greghulette/Wireless_Communication_Board-WCB/docs/hil_plan/WCB.md

# WCB HIL coverage re-scan: work plan WCB-WP12 to WCB-WP59

> Written 2026-09-27 by planning agents that read the code (and, for WCB, a verified coverage re-scan), for the
> away week's goal: a complete HIL tool for the WCBs, NaviCore and Intellex. It is a plan, not a spec: line numbers
> drift, and any claim is to be confirmed against the code before acting on it. Progress is tracked in
> [../HIL_TEST_AUDIT.md](../HIL_TEST_AUDIT.md) §6 and decisions in [../HIL_WEEK_DECISIONS.md](../HIL_WEEK_DECISIONS.md).

2026-09-27. Input: `scratchpad/wcb_rescan_gaps.json` (11 groups, 295 confirmed gap entries; the 5 refuted entries are
excluded). Code: HEAD `1f629a8`. Read-only: no port opened, nothing run.

**Line numbers.** The WP tables keep the scan's citations, which were taken at `c619dd6`. Commit `1f629a8` (tracker #94,
RMT PWM pulses) landed after the scan. It moved `WCB.ino` by -3 lines after :7949 and moved `WCB_PWM.cpp` by about
+80 lines after :155. §3 cites `1f629a8`, and every line there was re-checked by hand. For the full how, nearest test and
verifier notes of any row, look its id up in the JSON.

**Codes.** Mode: U = unattended; O = opt-in (bench.json key named); A = attended (per D7 these still run in the nightly
full runs when ticked). Effort: S = under half a day, M = about a day, L = several days, or reboot-heavy, or needs a
firmware fix first. **BUG-n** = the test is expected to fail until §3 item n is fixed. Write it as a `(should)` test.

---

## 1. How much of the WCB is not covered

The re-scan verified 295 gap entries against 1,941 checked behaviours (the two mechanical scans account for 644 of
those): 19 high, 98 medium and 178 low risk, of which 208 are untested and 87 partial. The two mechanical scans overlap the behaviour groups heavily. After merging
duplicates, **214 distinct behaviours** remain uncovered: **18 high, 75 medium, 121 low**. 177 are firmware
(9 H / 54 M / 114 L) and 37 are Wizard (9 H / 21 M / 7 L).

Testability of the 214:
- 176 can be tested unattended on today's bench.
- 25 need an opt-in or someone at the bench.
- 13 are blocked: 4 need a probe feature, 2 need hardware the bench lacks, and 7 need a firmware fault knob or are dead
  code.

The command surface itself is well pinned. What is missing falls into four areas:
- **Concurrency and ordering:** the loop-prevention race, restart versus config pull, and the boot load order.
- **Multi-actor mesh paths the bench never combines:** relay pushes, Wizard-origin FRAGs, permanent auto-join,
  controller-routed traffic, and daisy-chained Maestros.
- **Persistence:** non-default values across a reboot, and behaviour on a full NVS.
- **The Wizard's push side:** only a single one-label direct push is tested.

The scan also exposed **32 firmware findings, 3 high and 12 medium (§3). 26 are outright defects.** Among them:
- saved PWM mappings load before the board number;
- `?HW` accepts the other chip's pin map (a boot loop on a classic ESP32);
- a race drops typed broadcasts from the mesh;
- ETM characterisation phase 3 never loads the mesh.

---

## 2. Work packages
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
