greghulette/Wireless_Communication_Board-WCB/Code/bin/WCB_S3_custom_bootloader_README.md

# WCB ESP32-S3 custom bootloader

**File:** `WCB_S3_custom_bootloader_16MB_wdt3s.bin`

A drop-in replacement for the stock Arduino-ESP32 3.3.4 S3 bootloader, identical
to it **except** the RTC watchdog timeout is shortened from 9000 ms → **3000 ms**.
Purpose: if a cold/marginal board stalls in the pre-app boot window, it
auto-resets and retries in ~3 s instead of sitting dark until someone presses
reset. The RTC WDT runs off the internal RC oscillator, so it still fires even
when a cold crystal is what's stalling the boot.
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
