greghulette/Wireless_Communication_Board-WCB/Images/21cropped.jpg

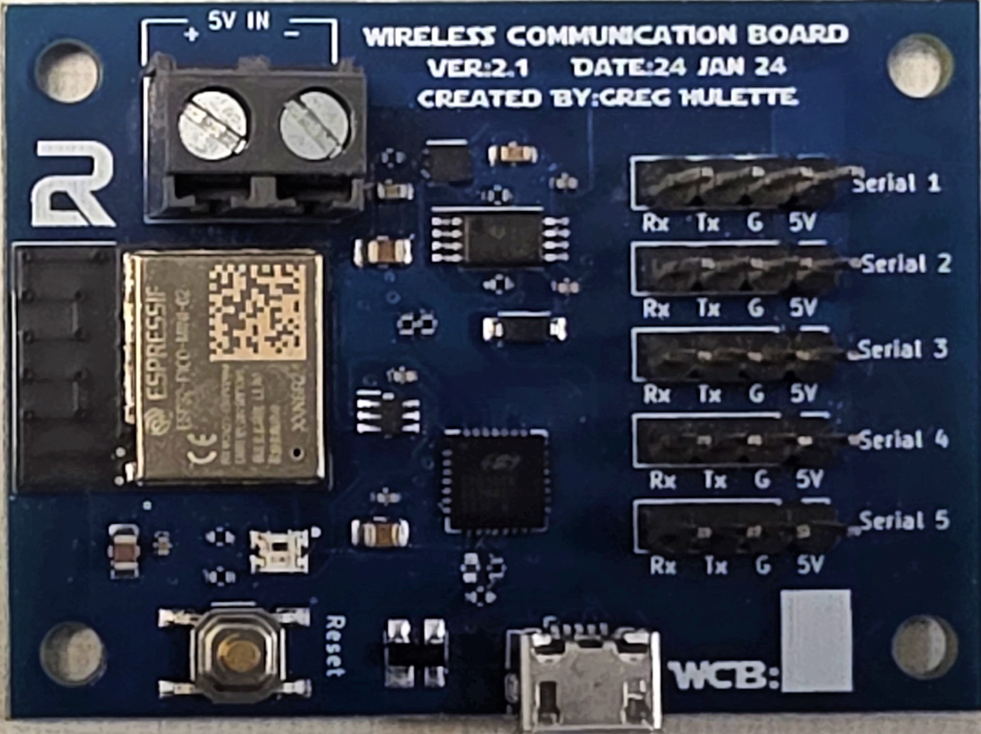
Images/21cropped.jpg
