greghulette/Wireless_Communication_Board-WCB/Images/24-1.png

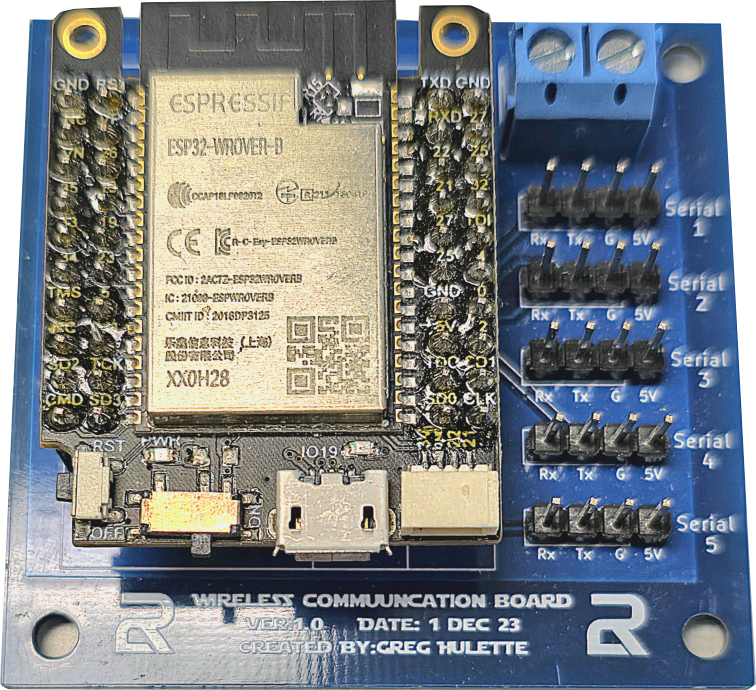
Images/24-1.png
