greghulette/Wireless_Communication_Board-WCB/Images/24.png

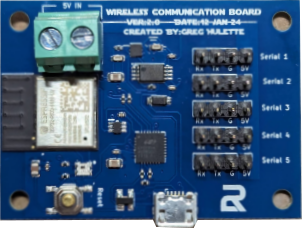
Images/24.png
