greghulette/Wireless_Communication_Board-WCB/Images/24cropped.jpg

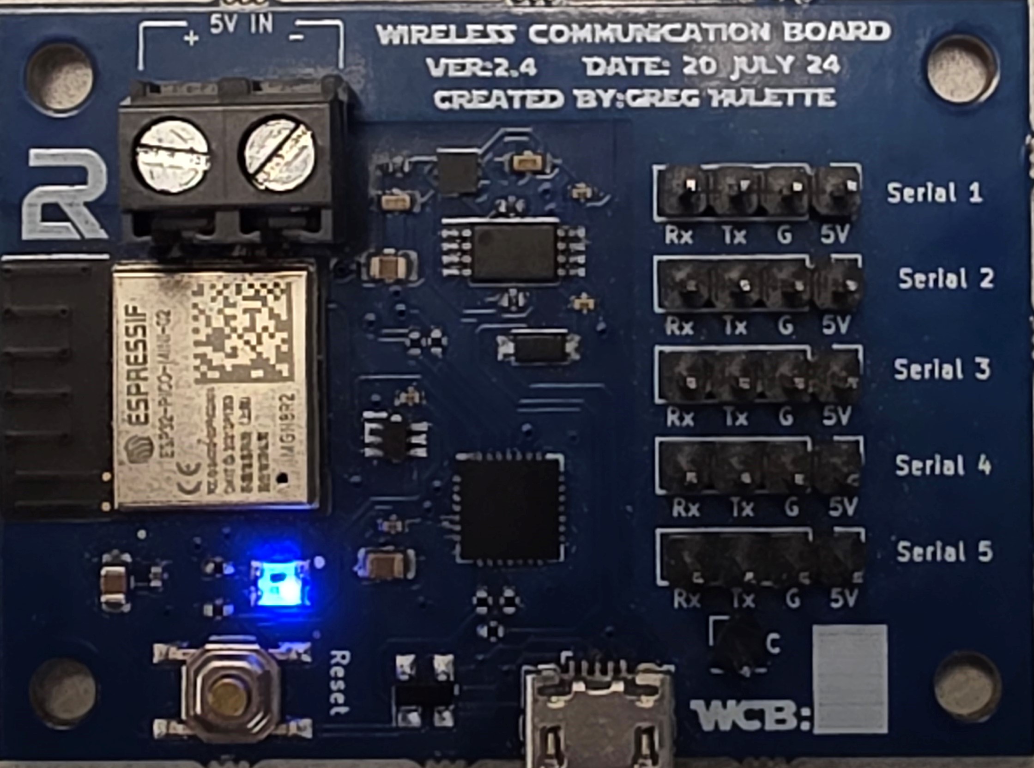
Images/24cropped.jpg
