greghulette/Wireless_Communication_Board-WCB/Images/32-1.png

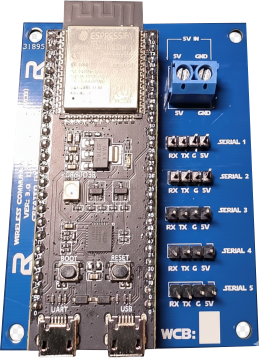
Images/32-1.png
