greghulette/Wireless_Communication_Board-WCB/Images/CAD3.1.png

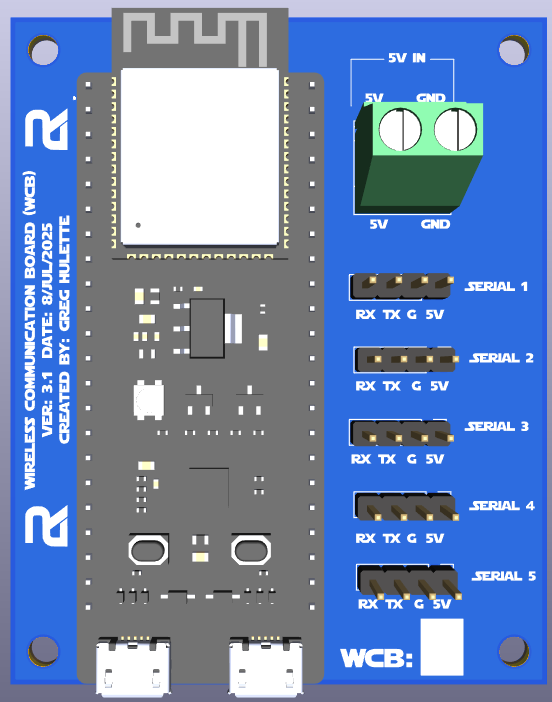
Images/CAD3.1.png
