greghulette/Wireless_Communication_Board-WCB/Images/CAD3.1_Bare.png

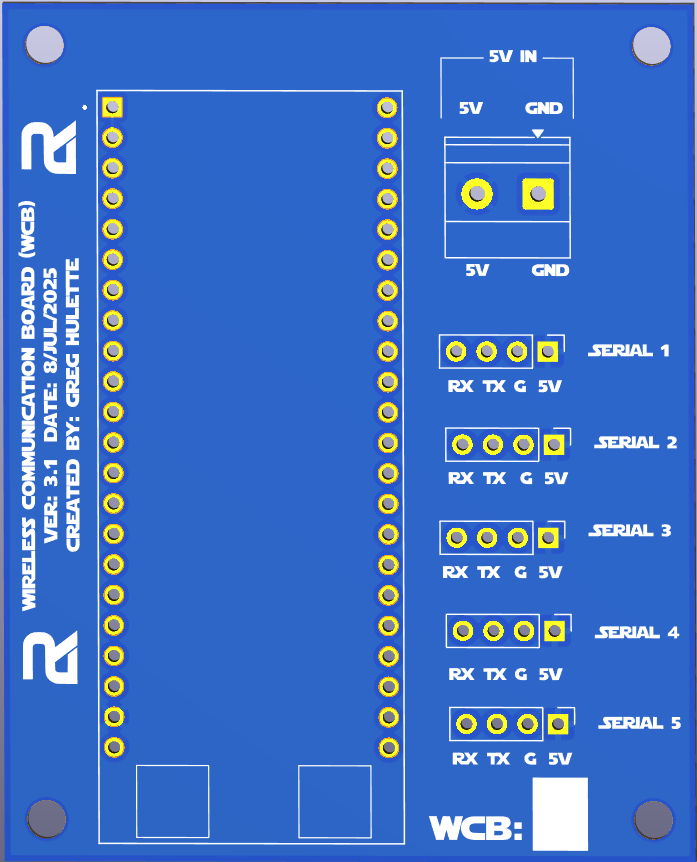
Images/CAD3.1_Bare.png
