greghulette/Wireless_Communication_Board-WCB/Images/CAD3.2.png

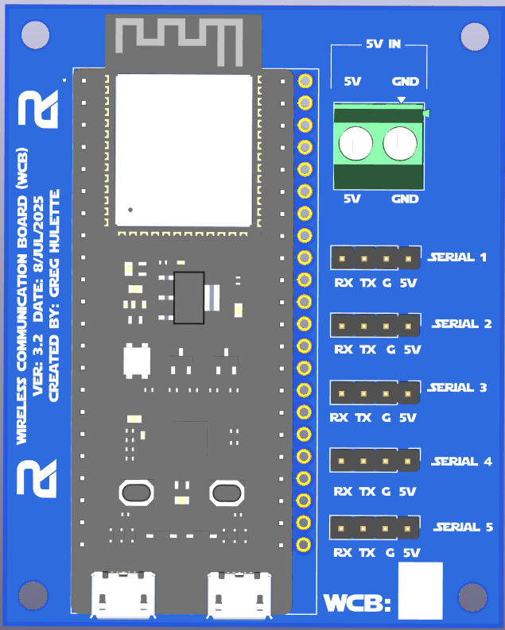
Images/CAD3.2.png
