greghulette/Wireless_Communication_Board-WCB/Images/CAD3.2_Bare.png

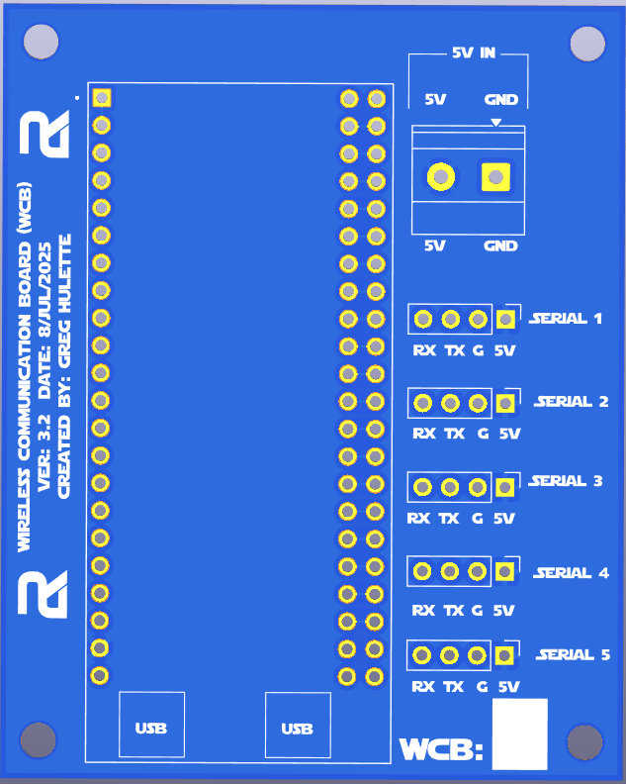
Images/CAD3.2_Bare.png
