greghulette/Wireless_Communication_Board-WCB/Images/CADImage.png

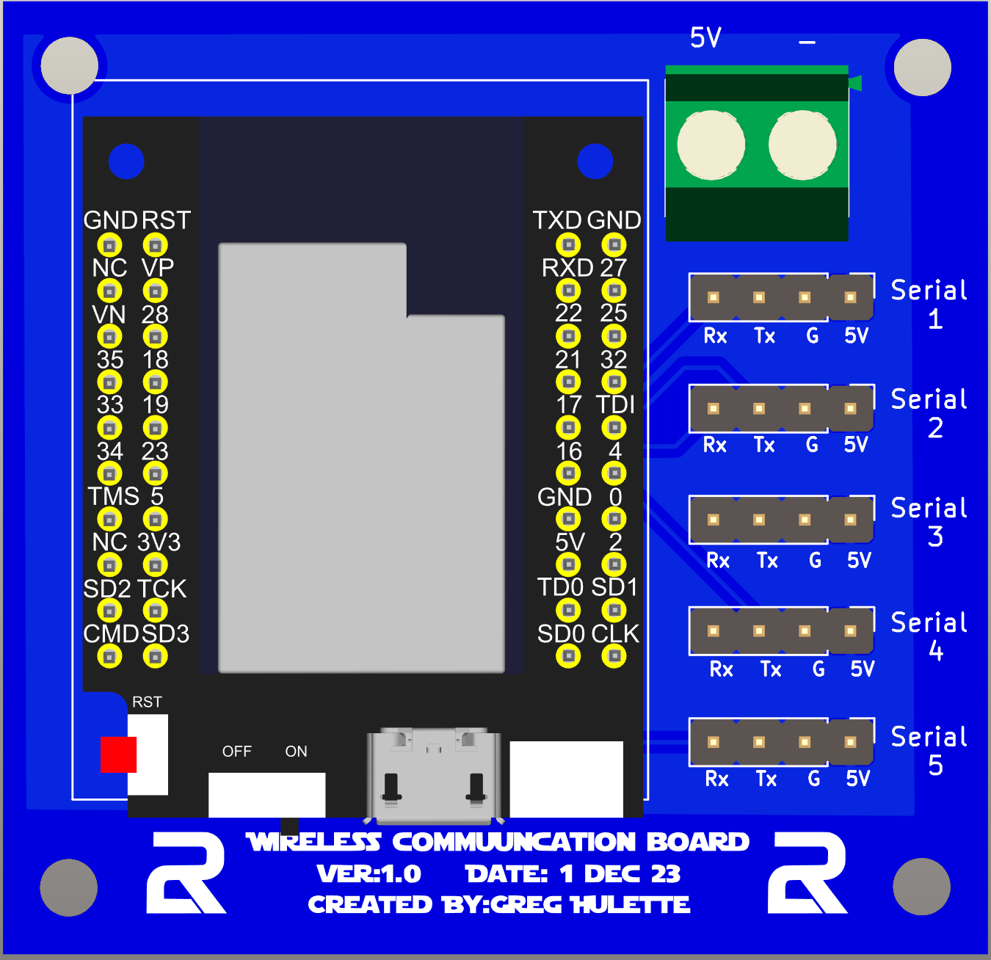
Images/CADImage.png
