greghulette/Wireless_Communication_Board-WCB/Images/Code_Preferences.png

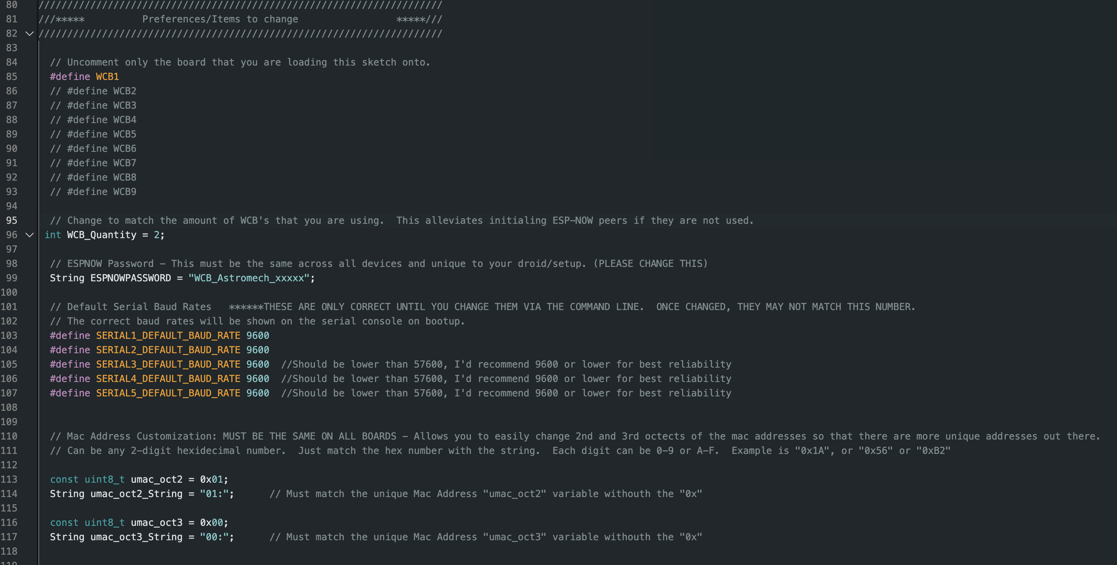
Images/Code_Preferences.png
