greghulette/Wireless_Communication_Board-WCB/Images/DataConnection.png

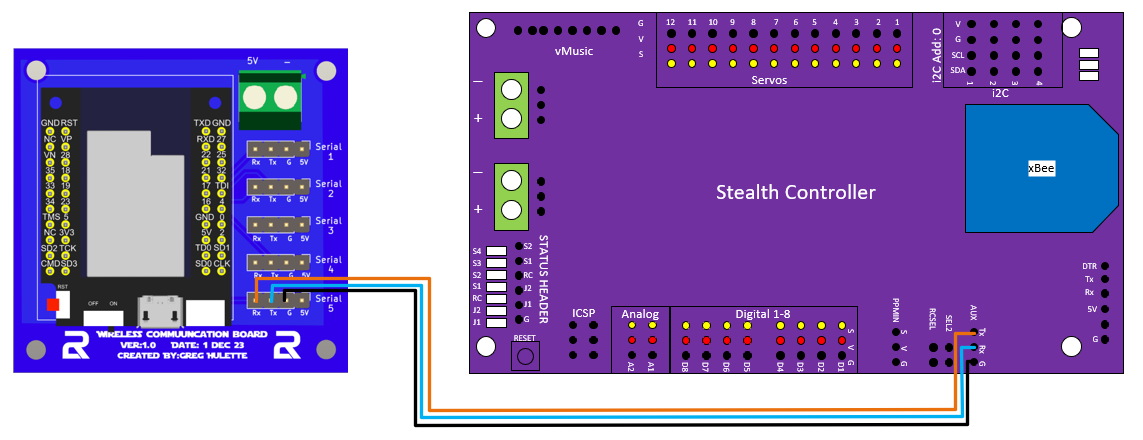
Images/DataConnection.png
