greghulette/Wireless_Communication_Board-WCB/Images/DimensionsV1.0.png

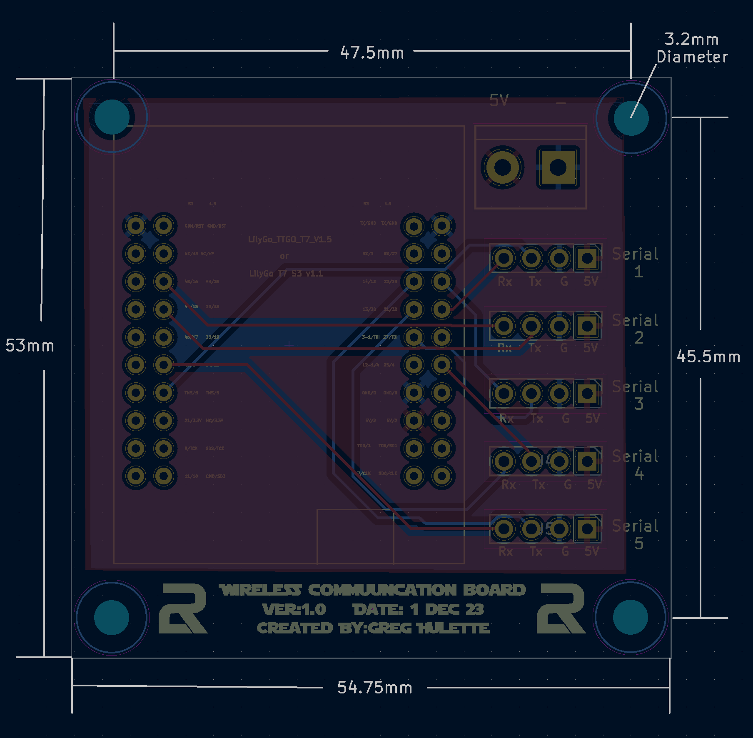
Images/DimensionsV1.0.png
