greghulette/Wireless_Communication_Board-WCB/Images/DimensionsV2.1.png

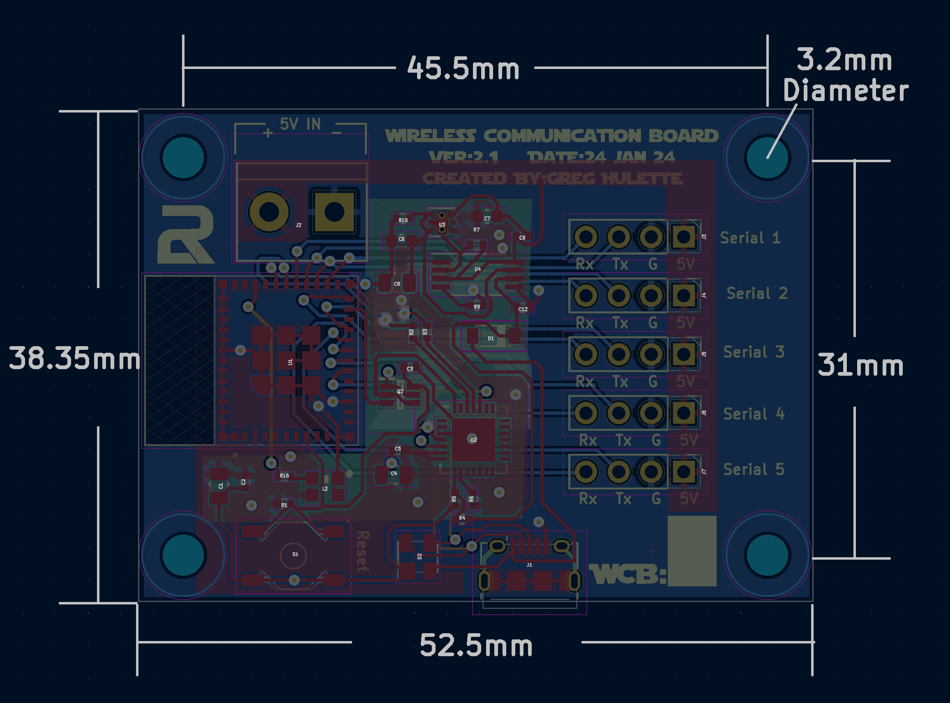
Images/DimensionsV2.1.png
