greghulette/Wireless_Communication_Board-WCB/Images/DimensionsV3.1.png

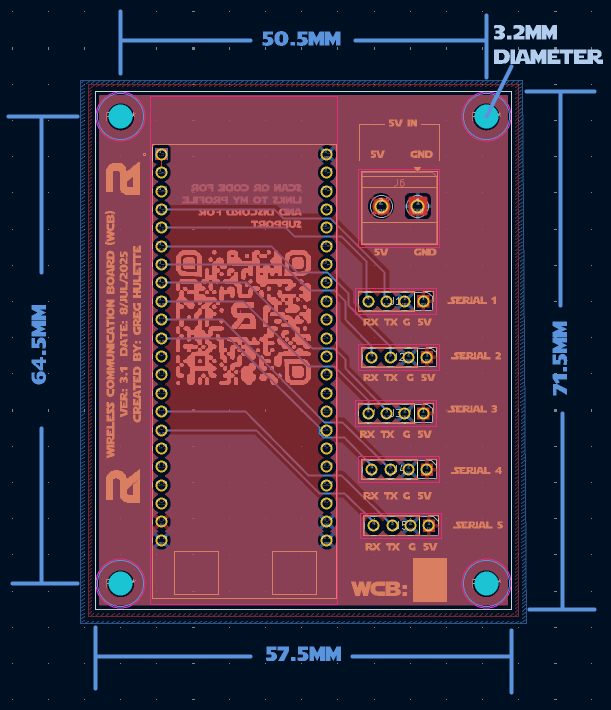
Images/DimensionsV3.1.png
