greghulette/Wireless_Communication_Board-WCB/Images/gif/Broadcasts/OverviewImage Pololu Forum.png

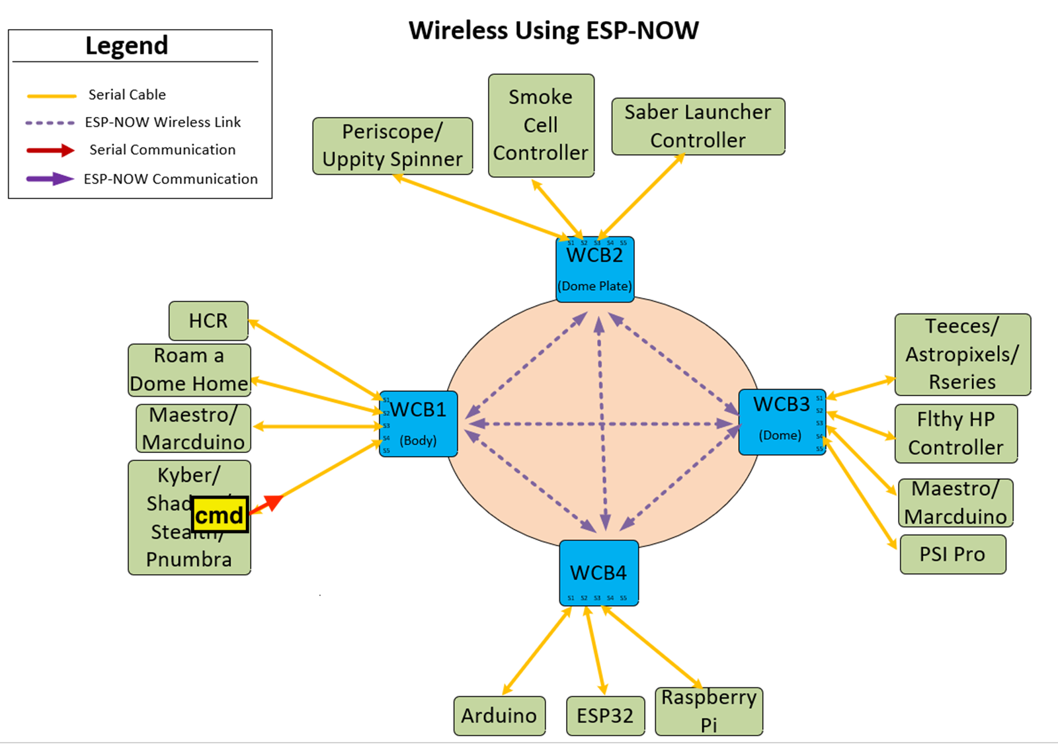
Images/gif/Broadcasts/OverviewImage Pololu Forum.png
