greghulette/Wireless_Communication_Board-WCB/Images/HW2.3CAD.png

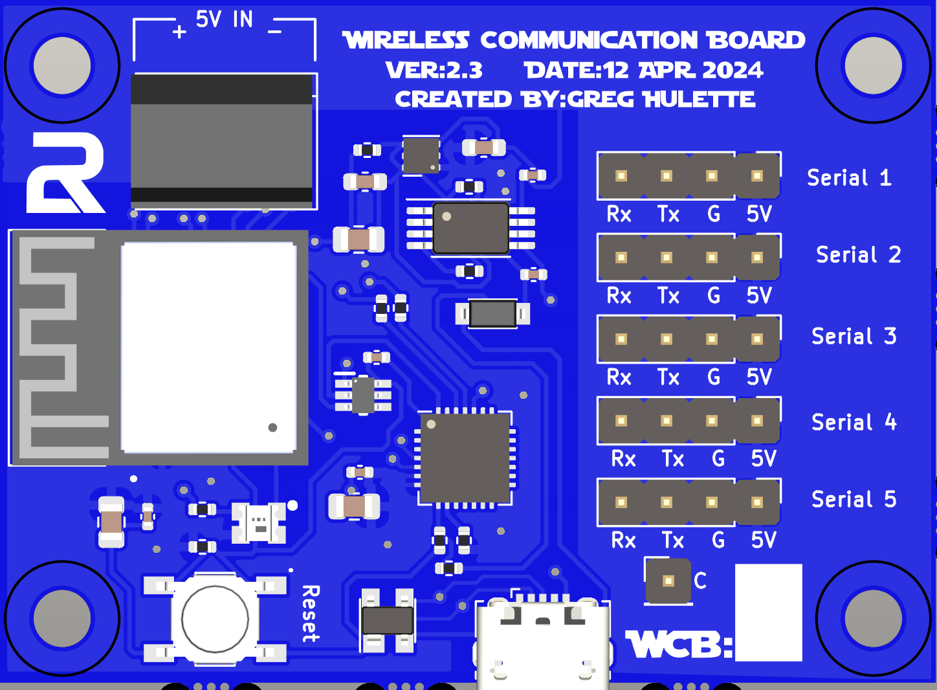
Images/HW2.3CAD.png
