greghulette/Wireless_Communication_Board-WCB/Images/HWV2.1_CAD.png

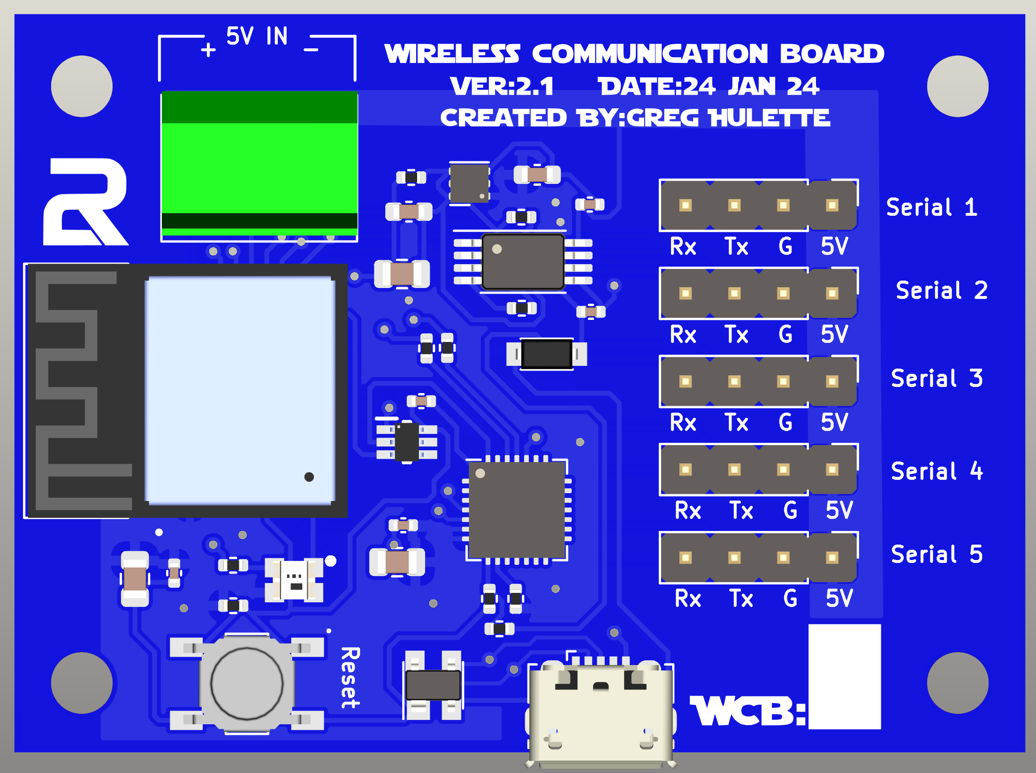
Images/HWV2.1_CAD.png
