greghulette/Wireless_Communication_Board-WCB/Images/Kyber_Close_Up.png

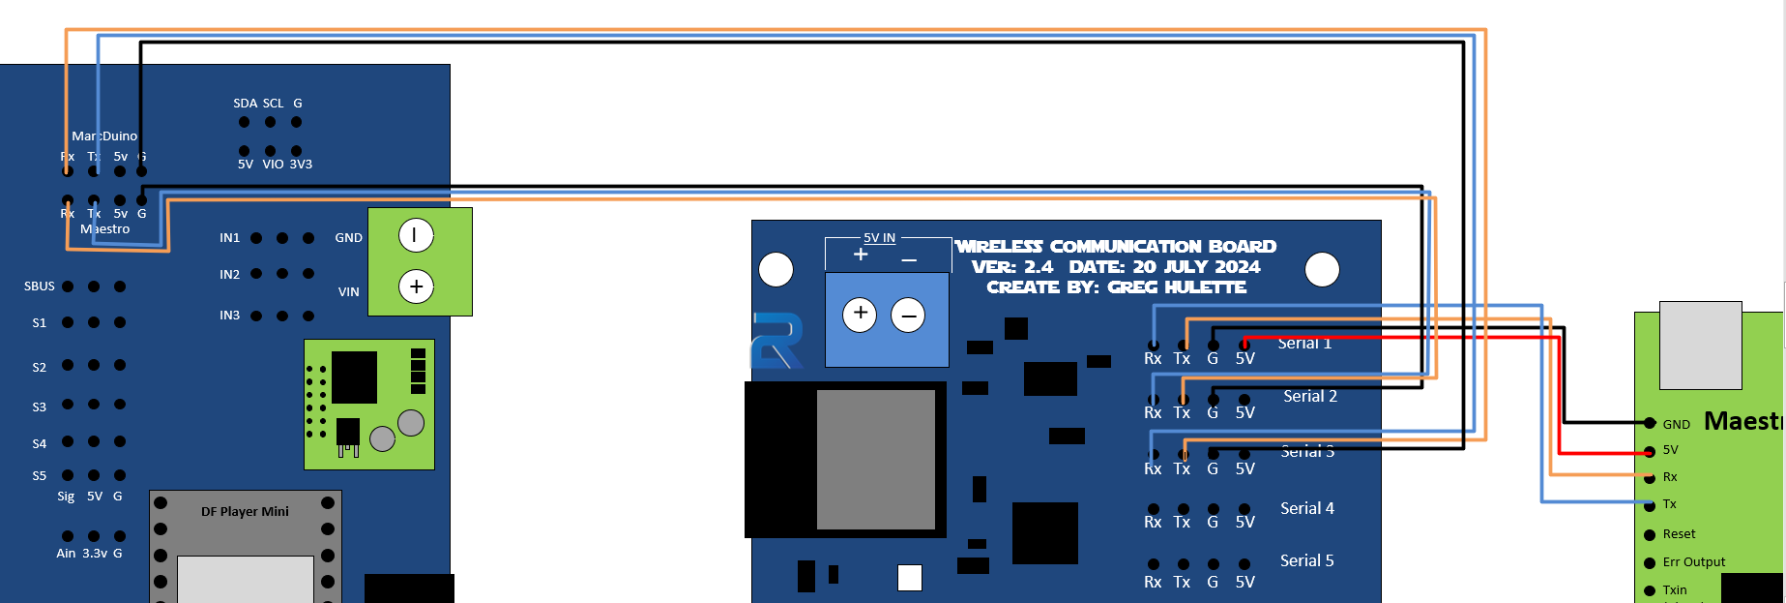
Images/Kyber_Close_Up.png
