greghulette/Wireless_Communication_Board-WCB/Images/LabelOnly.jpg

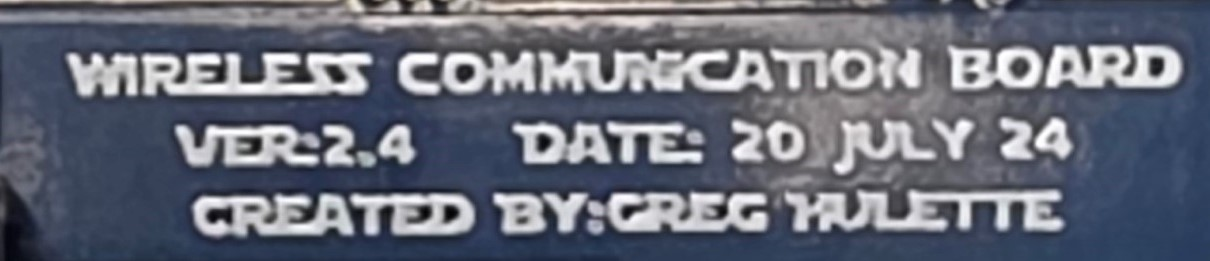
Images/LabelOnly.jpg
