greghulette/Wireless_Communication_Board-WCB/Images/Network_Model_1.jpg

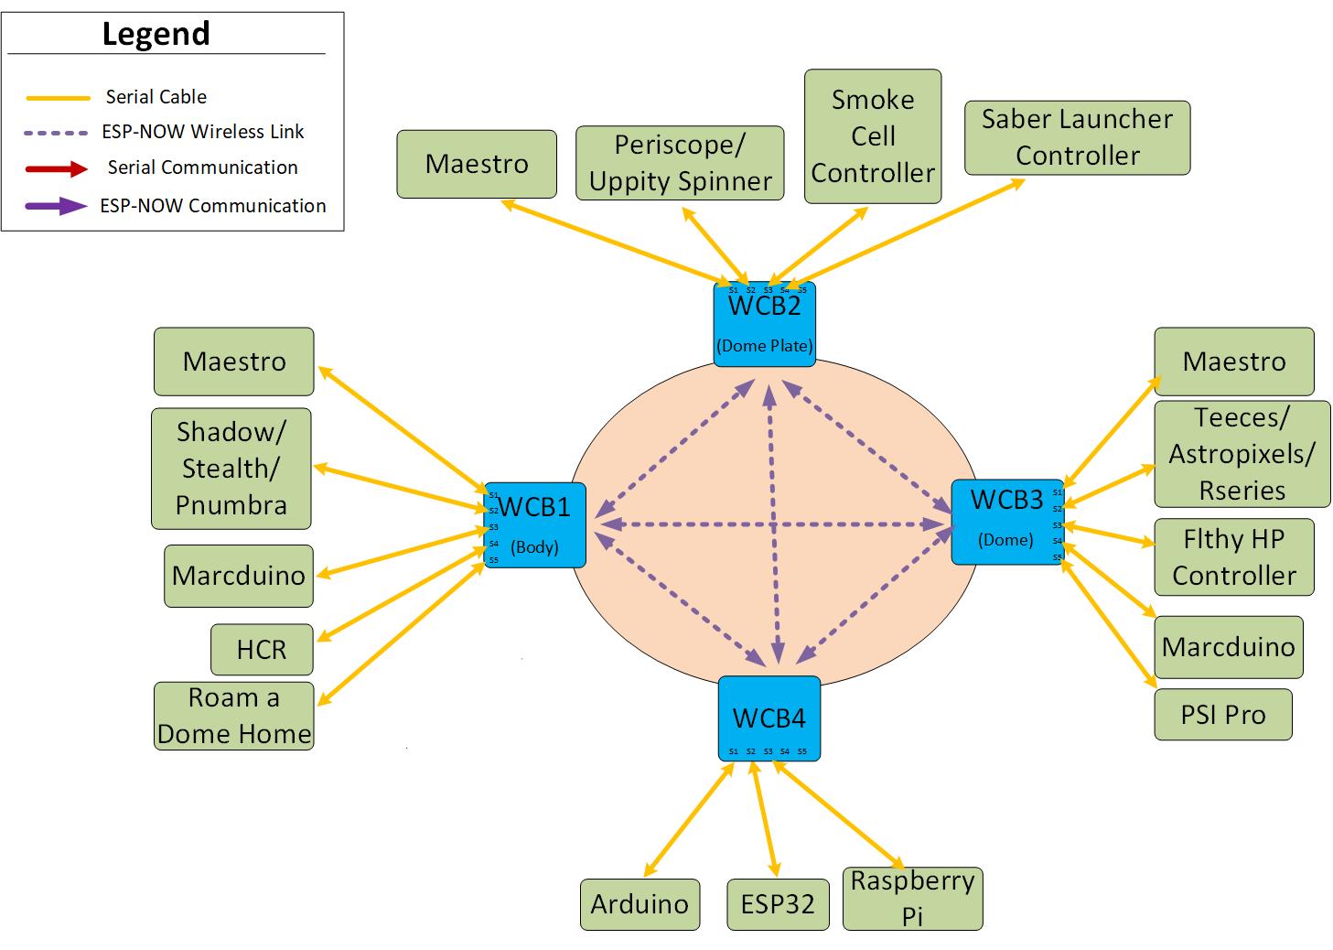
Images/Network_Model_1.jpg
