greghulette/Wireless_Communication_Board-WCB/Images/PowerOptions.png

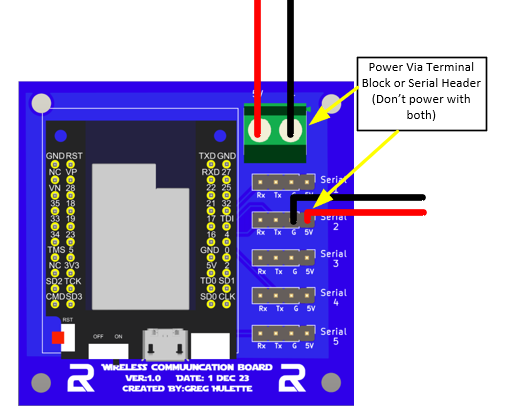
Images/PowerOptions.png
