greghulette/Wireless_Communication_Board-WCB/Images/PowerV2.1.png

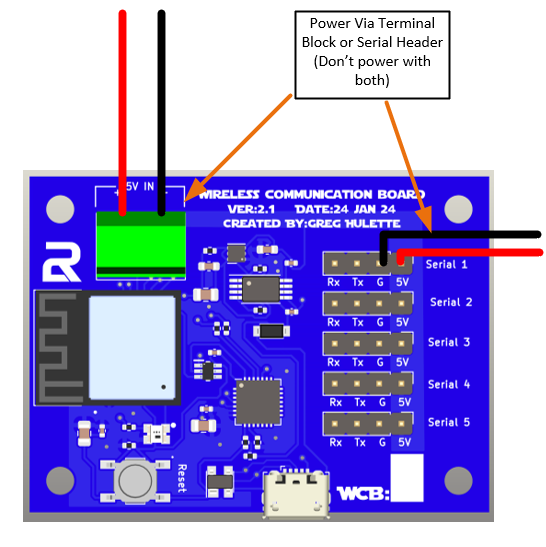
Images/PowerV2.1.png
