greghulette/Wireless_Communication_Board-WCB/Images/Preferences_Overview.png

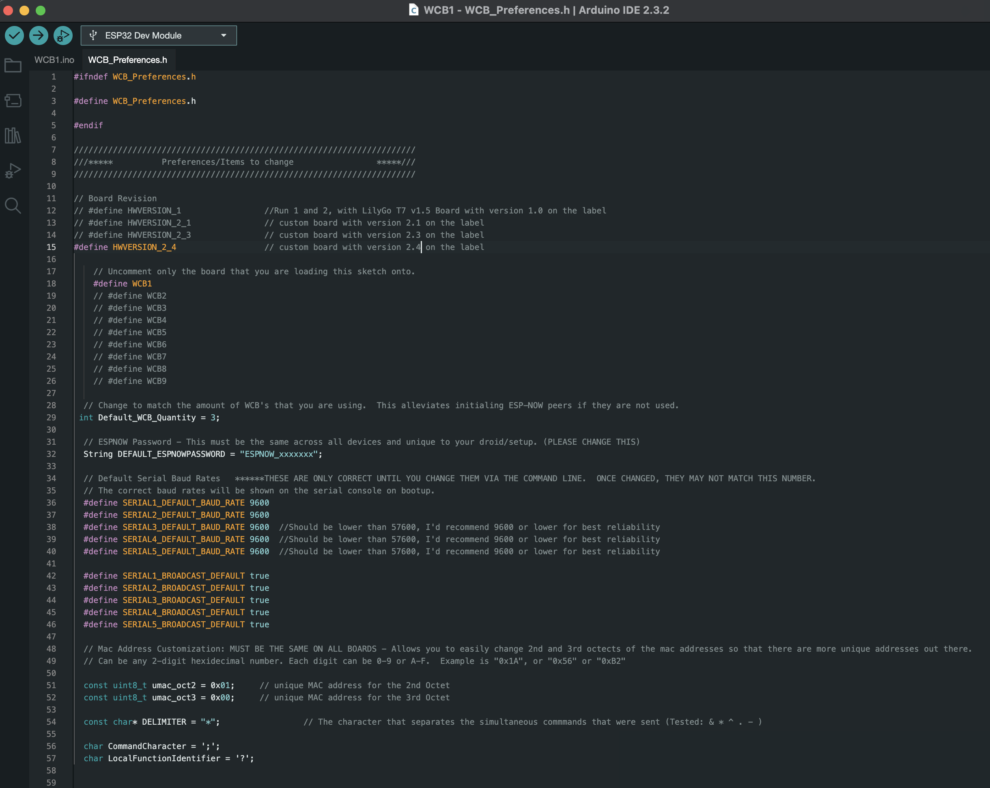
Images/Preferences_Overview.png
