greghulette/Wireless_Communication_Board-WCB/Images/SerialOnlyConceptTransmissionOption1.png

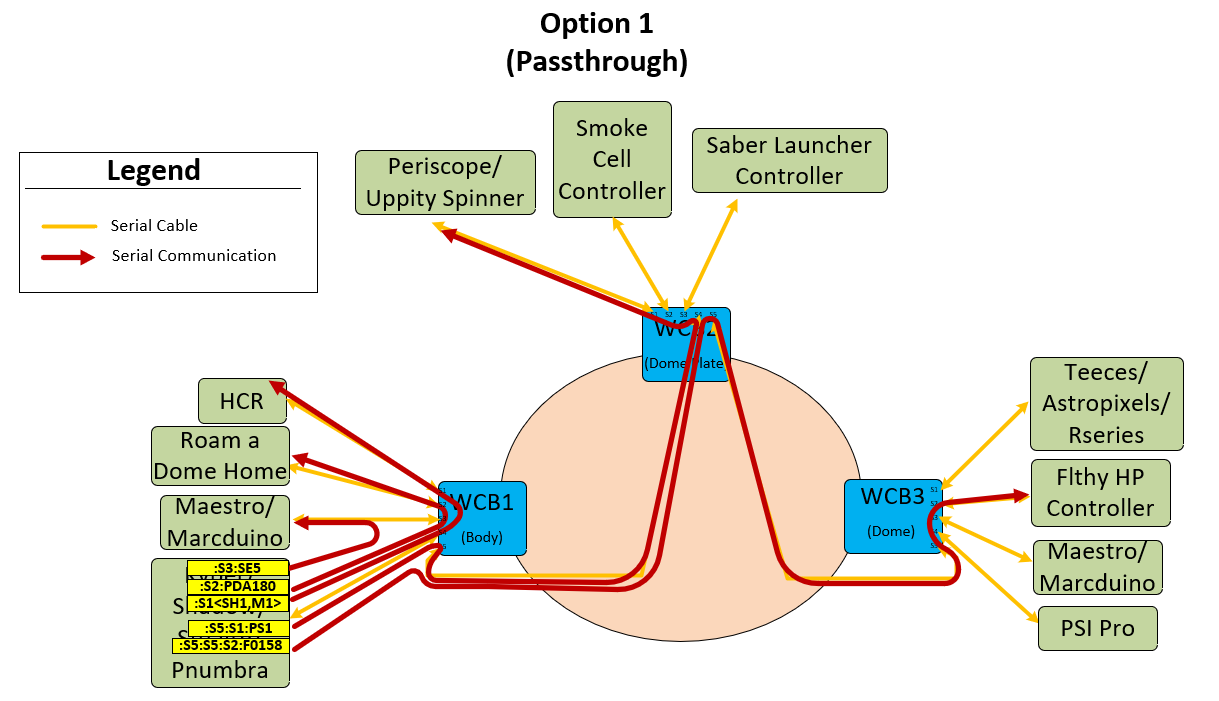
Images/SerialOnlyConceptTransmissionOption1.png
