greghulette/Wireless_Communication_Board-WCB/Images/SerialOnlyConceptTransmissionOption2.png

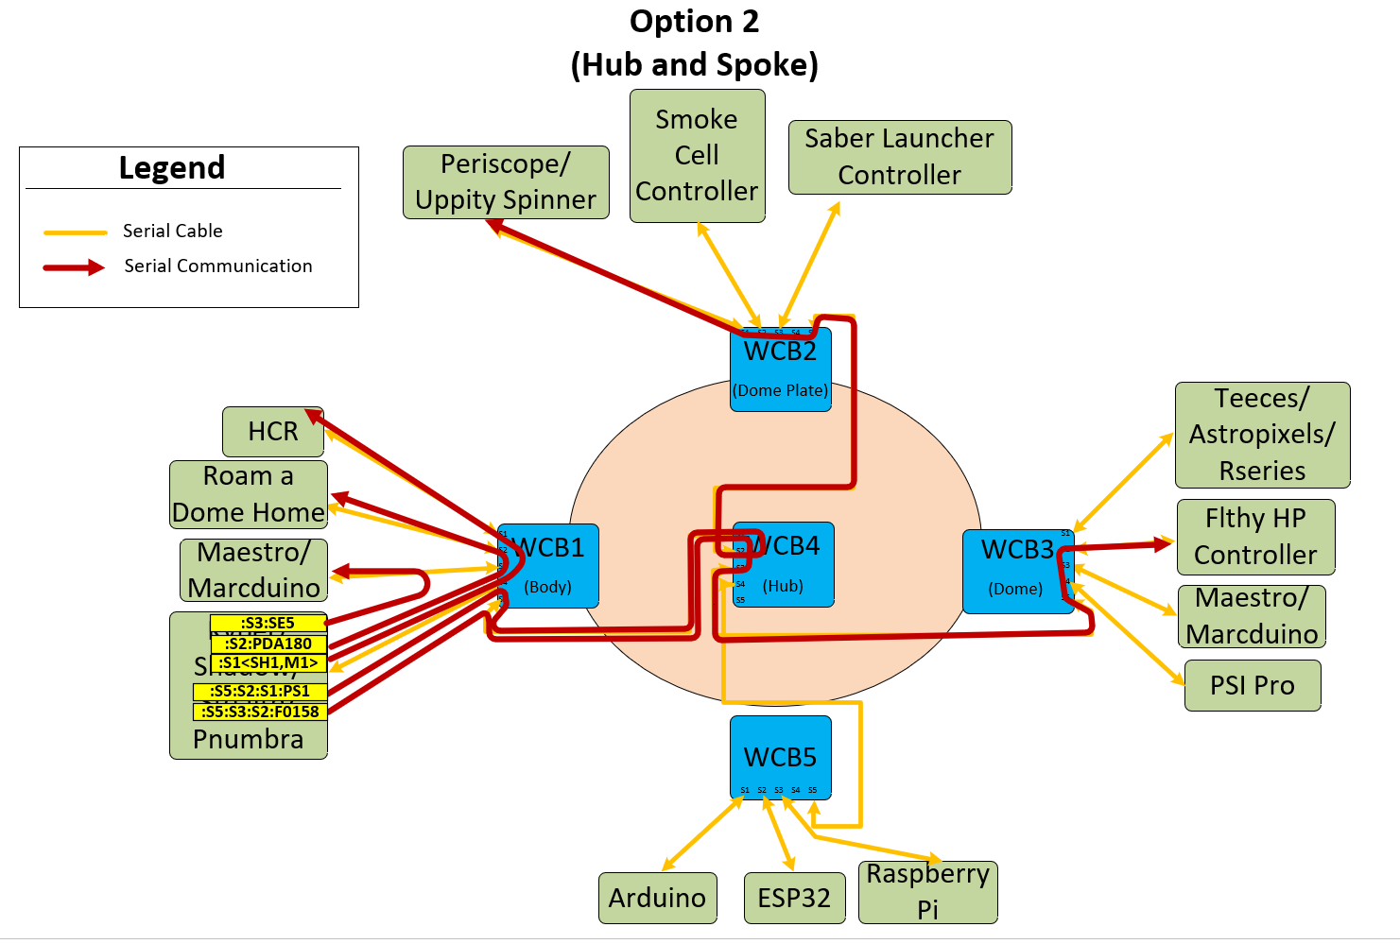
Images/SerialOnlyConceptTransmissionOption2.png
