greghulette/Wireless_Communication_Board-WCB/Images/Title.png

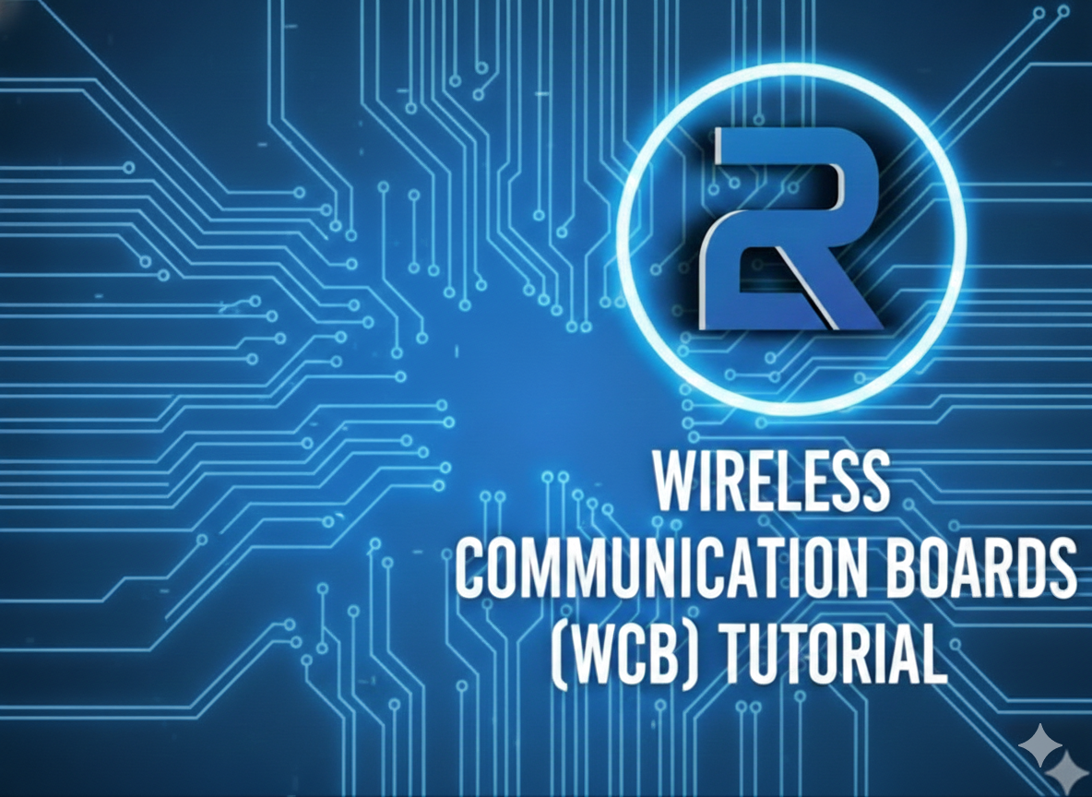
Images/Title.png
