greghulette/Wireless_Communication_Board-WCB/Images/Title_1.png

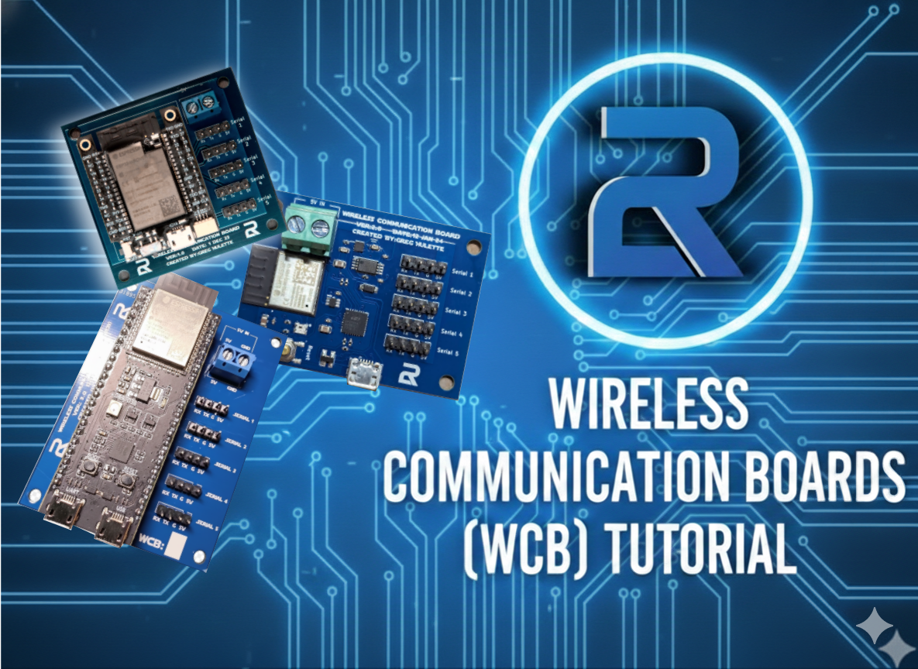
Images/Title_1.png
