greghulette/Wireless_Communication_Board-WCB/Images/WCB_Preferences_Tab.png

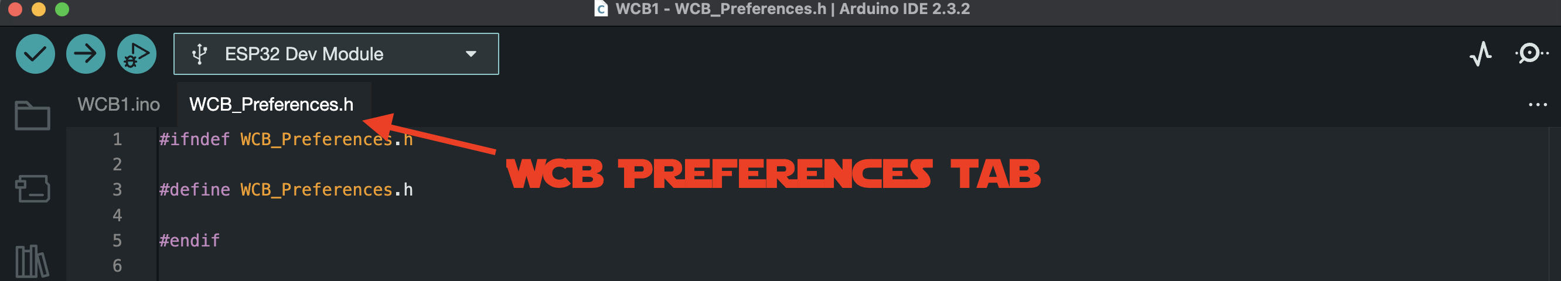
Images/WCB_Preferences_Tab.png
