greghulette/Wireless_Communication_Board-WCB/PCB/Wireless Communication Board (WCB)V3.2/Images/Comparison2.4to3.0.png

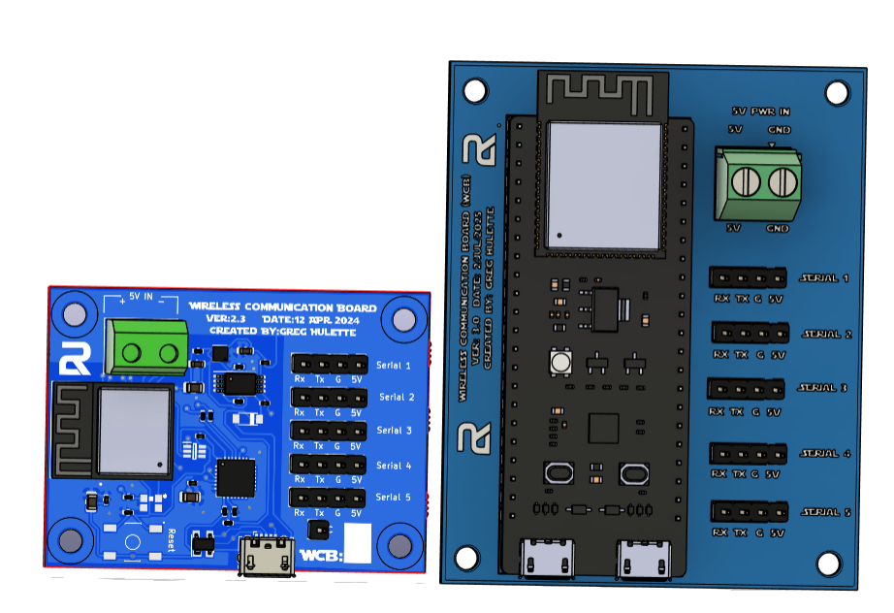
PCB/Wireless Communication Board (WCB)V3.2/Images/Comparison2.4to3.0.png
