greghulette/Wireless_Communication_Board-WCB/PCB/Wireless Communication Board (WCB)V3.2/Images/Image_of_3.1.jpg

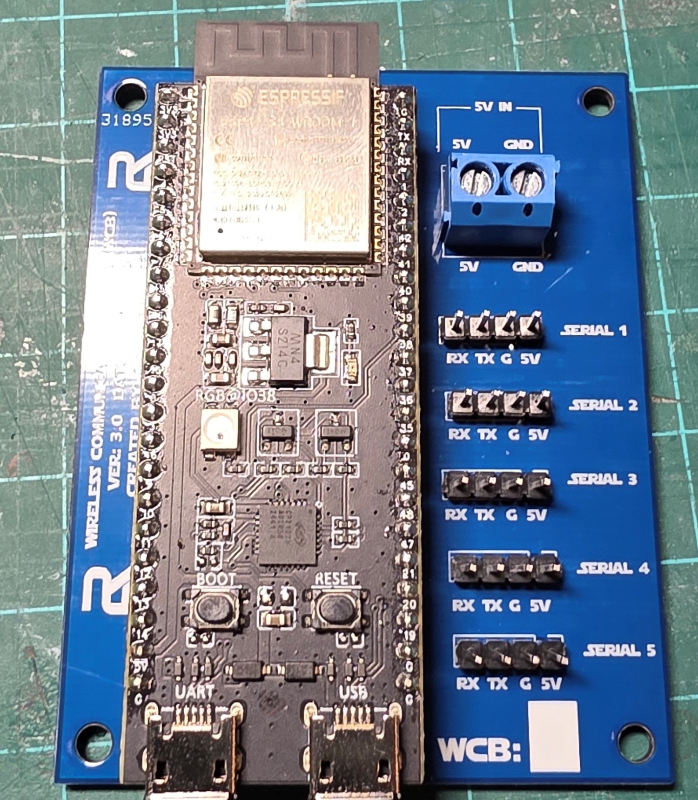
PCB/Wireless Communication Board (WCB)V3.2/Images/Image_of_3.1.jpg
