greghulette/Wireless_Communication_Board-WCB/Images/3.1_Instructions/components.jpg

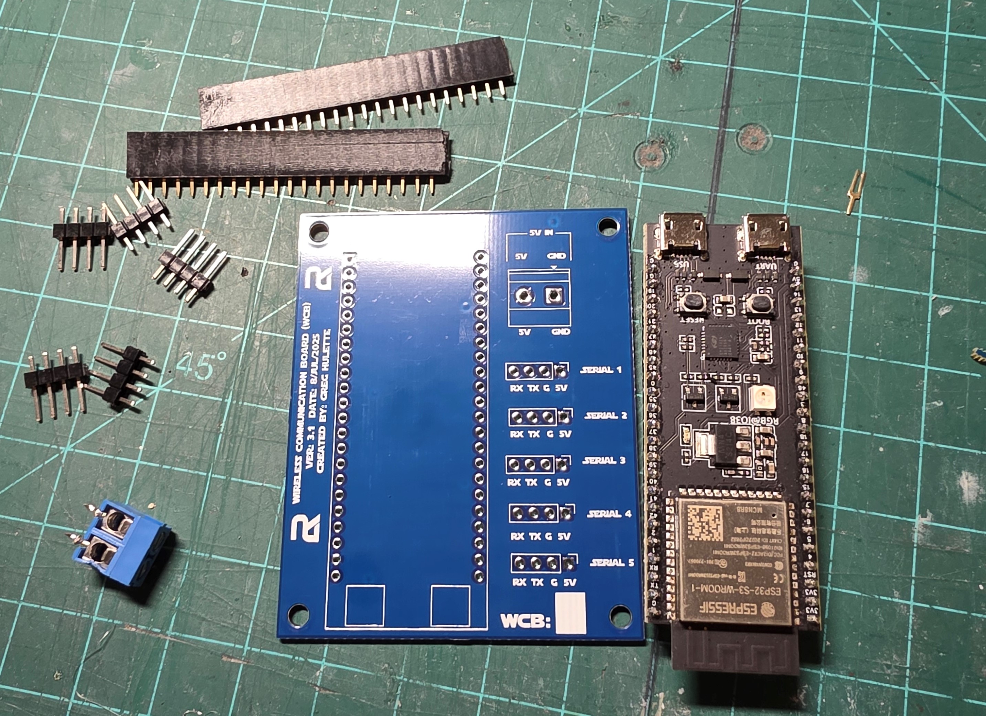
Images/3.1_Instructions/components.jpg
