greghulette/Wireless_Communication_Board-WCB/Images/3.1_Instructions/jlc_order2.png

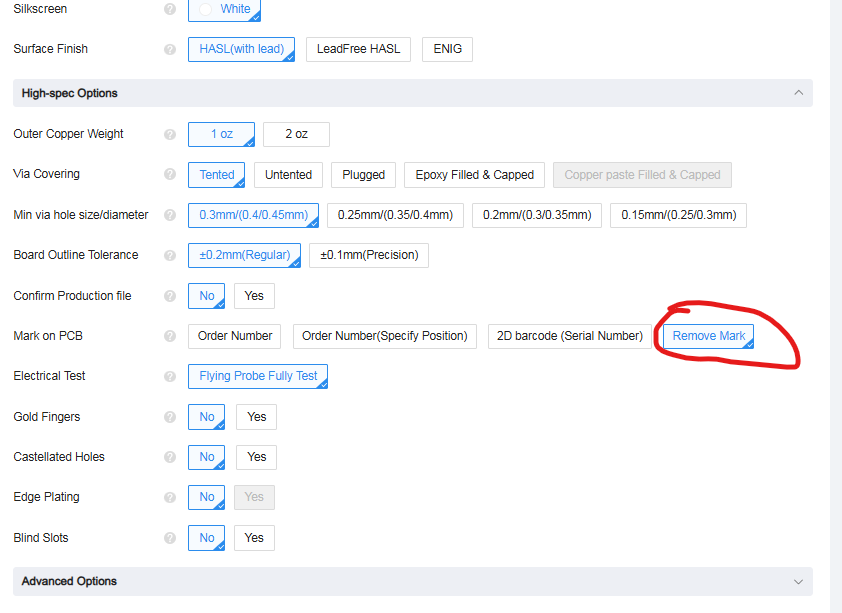
Images/3.1_Instructions/jlc_order2.png
