greghulette/Wireless_Communication_Board-WCB/Images/3.1_Instructions/jlc_home.png

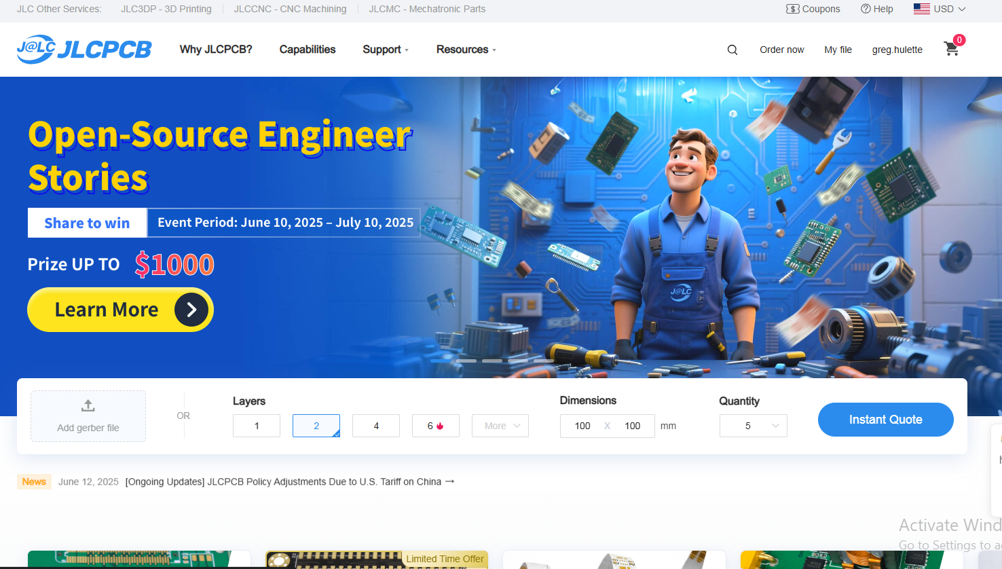
Images/3.1_Instructions/jlc_home.png
