greghulette/Wireless_Communication_Board-WCB/Images/3.1_Instructions/Solder13.jpg

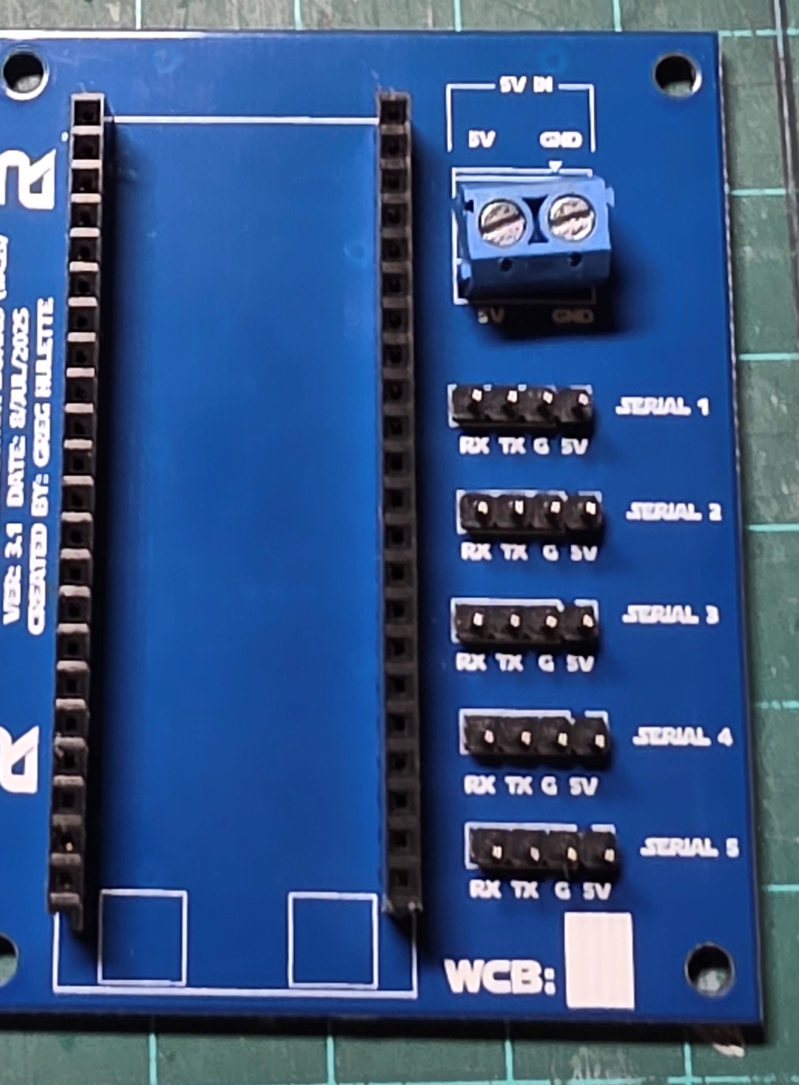
Images/3.1_Instructions/Solder13.jpg
