greghulette/Wireless_Communication_Board-WCB/Images/3.1_Instructions/Solder14.jpg

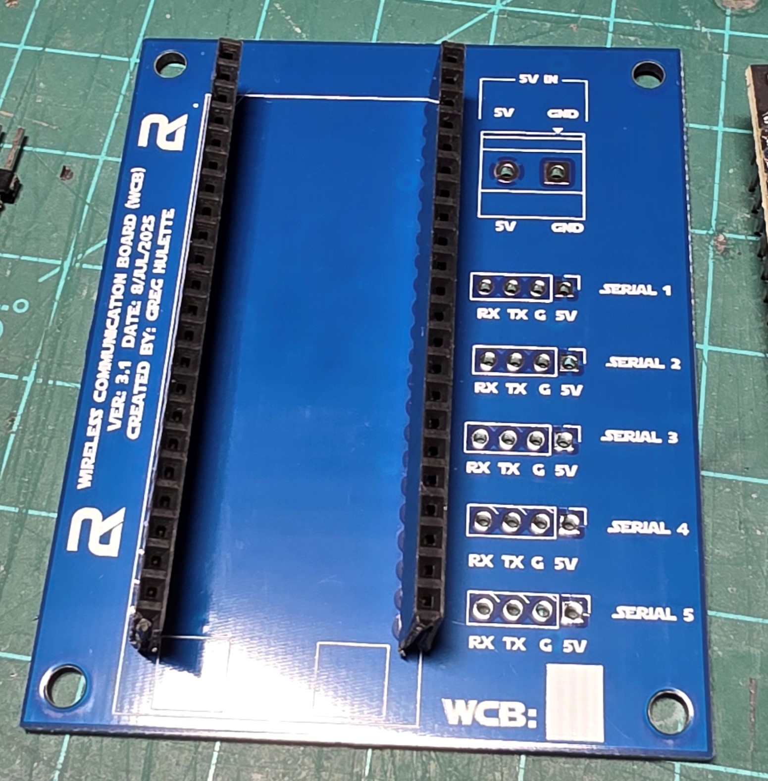
Images/3.1_Instructions/Solder14.jpg
