greghulette/Wireless_Communication_Board-WCB/Images/Kyber Wiring.png

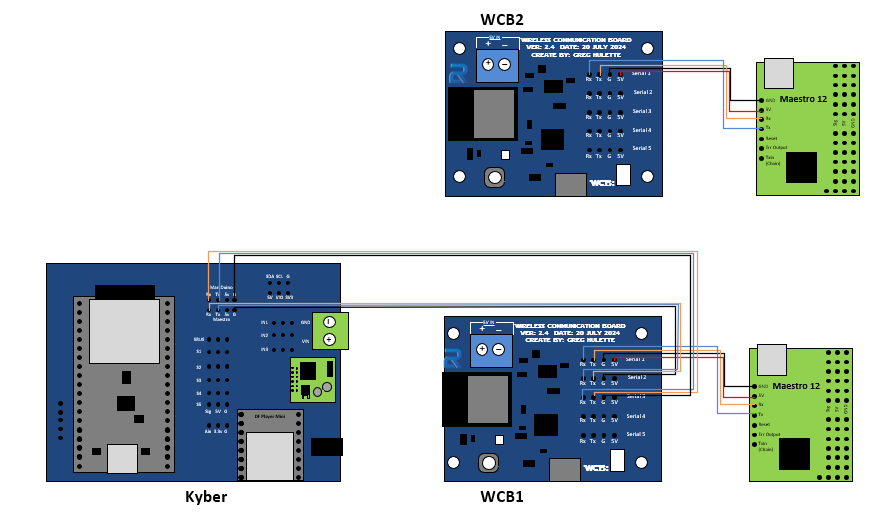
Images/Kyber Wiring.png
