greghulette/Wireless_Communication_Board-WCB/Images/SerialOnlyWiring.png

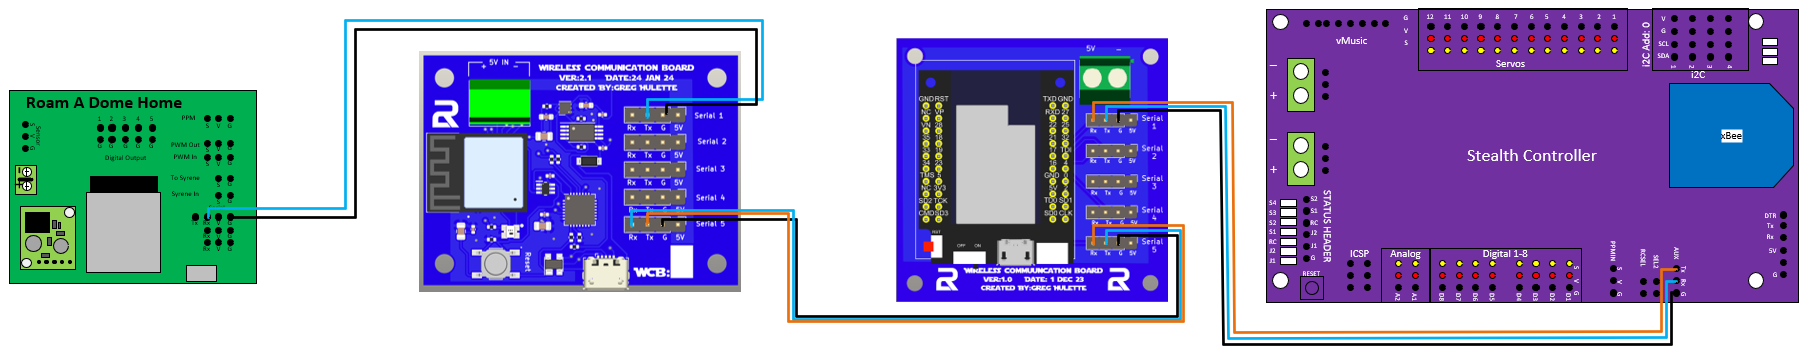
Images/SerialOnlyWiring.png
