greghulette/Wireless_Communication_Board-WCB/Images/Cropped_Actual_Pin_Issue.jpeg

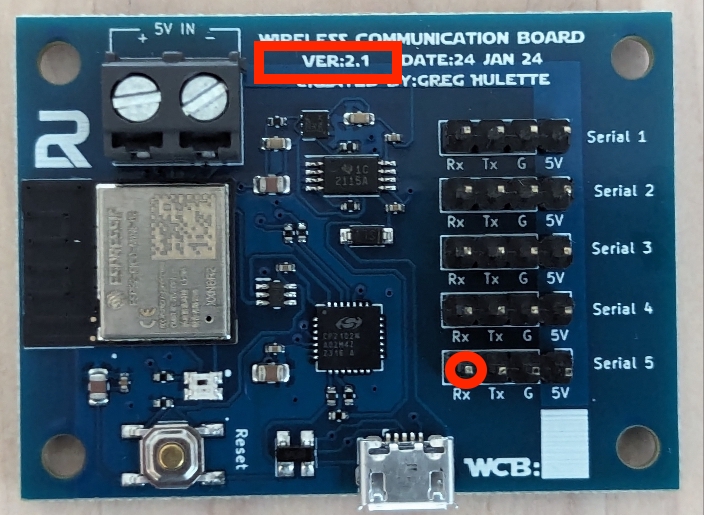
Images/Cropped_Actual_Pin_Issue.jpeg
