greghulette/Wireless_Communication_Board-WCB/Images/Issues with 2.3/Chain 5V Layer.png

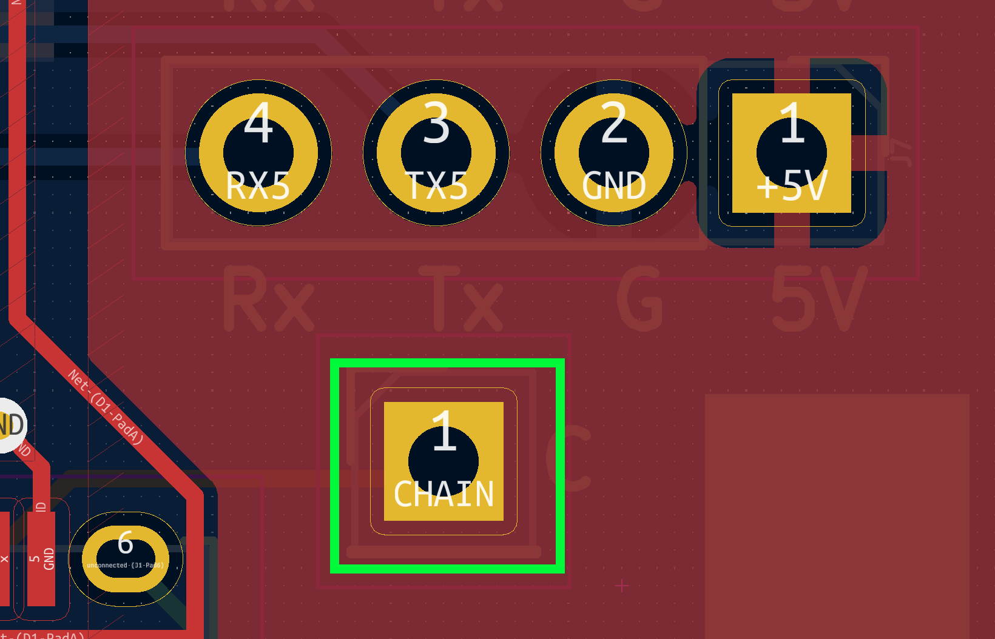
Images/Issues with 2.3/Chain 5V Layer.png
