greghulette/Wireless_Communication_Board-WCB/Images/Issues with 2.3/Xray.jpg

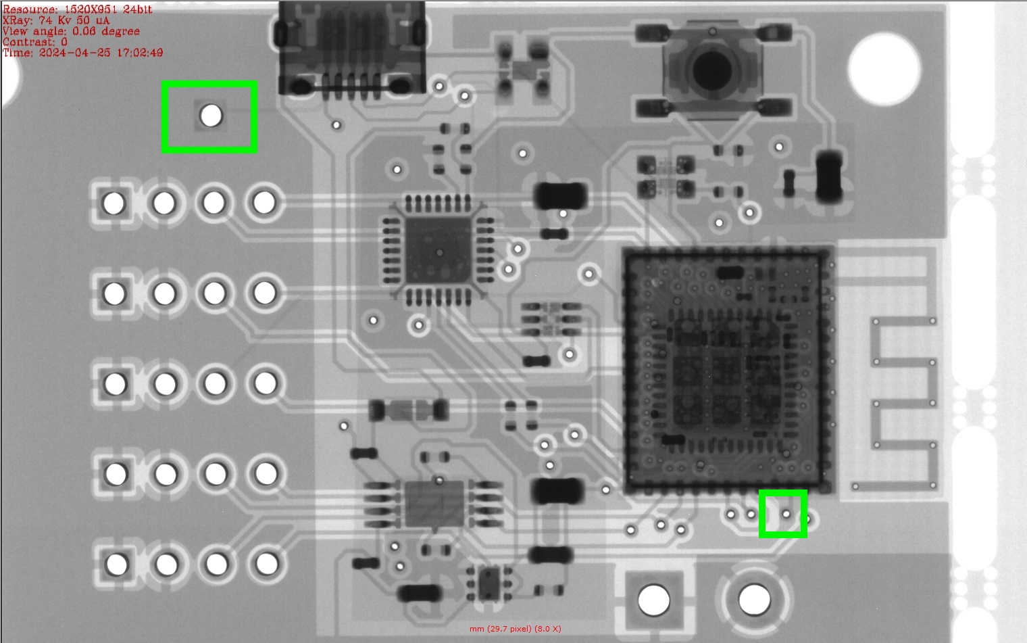
Images/Issues with 2.3/Xray.jpg
