greghulette/Wireless_Communication_Board-WCB/Code/WCB/WCB_Help.cpp

#include "WCB_RemoteTerm.h"  // Must be first — redirects Serial → WCBDebugSerial
#include "WCB_Help.h"
#include "WCB_Storage.h"

extern char commandDelimiter;
extern char LocalFunctionIdentifier;
extern char CommandCharacter;


void printCommandHelp(const String &cmd) {
    String c = cmd;
    c.trim();
    c.toUpperCase();

    // ================================================================
    if (c == "DEBUG") {

        Serial.println(F("---------------------------------------------------"));
        Serial.println(F("---------------------------------------------------"));
        Serial.println(F("\nUsage: ?DEBUG,<command>[,value]"));
        Serial.println(F("\nDescription:"));
        Serial.println(F("  Controls debug output for various subsystems. Debug output is"));
        Serial.println(F("  printed to the USB serial monitor. Enabling debug on a busy"));
        Serial.println(F("  system can produce a lot of output and may affect performance."));
        Serial.println(F("\nCommands:"));
        Serial.println(F("  ON                Enable main debug output"));
        Serial.println(F("  OFF               Disable main debug output"));
        Serial.println(F("  MAESTRO,ON        Enable Maestro and Kyber frame debug"));
        Serial.println(F("  MAESTRO,OFF       Disable it (KYBER,ON / KYBER,OFF set the same flag)"));
        Serial.println(F("  PWM,ON            Enable PWM passthrough debug"));
        Serial.println(F("                      Shows pulse widths and output routing"));
        Serial.println(F("  PWM,OFF           Disable PWM passthrough debug"));
        Serial.println(F("  ETM,ON            Enable ETM packet/ACK/retry debug"));
        Serial.println(F("                      Shows sequence numbers, ACKs, retries"));
        Serial.println(F("  ETM,OFF           Disable ETM debug"));
        Serial.println(F("\nTest knobs (mesh config pull, see ?MGMT?):"));
        Serial.println(F("  PULLFAULT,OOM     The next config pull this board accepts fails its"));
        Serial.println(F("                      reply buffer allocation and answers CFGERR"));
        Serial.println(F("                      NOMEM (+ an empty reply if it fits one line)."));
        Serial.println(F("                      One-shot; disarms after firing or after 60 s"));
        Serial.println(F("  PULLFAULT,LINE    For 60 s every config walk (?backup, a config"));
        Serial.println(F("                      pull) loses its WCBCH line as if out of"));
        Serial.println(F("                      memory: ?backup warns, a pull answers NOMEM"));
        Serial.println(F("  PULLFAULT,OFF     Disarm PULLFAULT (both kinds)"));
        Serial.println(F("  SEQNVS            The next boot (once) keeps stored sequences in"));
        Serial.println(F("                      NVS, the sequence store's fallback; the boot"));
        Serial.println(F("                      after moves them back into the store"));
        Serial.println(F("  PULLPART,<n>      Data bytes per part when this board sends a"));
        Serial.println(F("                      config in parts (512-2880; 0 or OFF = 2880)"));
        Serial.println(F("\nExamples:"));
        Serial.println(F("  ?DEBUG,ON"));
        Serial.println(F("  ?DEBUG,ETM,ON"));
        Serial.println(F("  ?DEBUG,PWM,OFF"));
        Serial.println(F("  ?DEBUG,PULLPART,600    - Split a large config into more parts"));
        Serial.println(F("\nNotes:"));
        Serial.println(F("  - Debug settings are NOT saved to NVS and reset on reboot"));
        Serial.println(F("  - PULLFAULT, PULLPART and SEQNVS are RAM-only and never in ?backup"));
        Serial.println(F("  - ETM debug is very verbose during characterization runs"));
        Serial.println(F("  - PWM debug will print for every pulse received"));
        Serial.println(F("\nLegacy commands:"));
        Serial.println(F("  ?DON / ?DOFF           - Main debug"));
        Serial.println(F("  ?DMON / ?DMOFF         - Maestro/Kyber debug (also ?DKON / ?DKOFF)"));
        Serial.println(F("  ?DPWMON / ?DPWMOFF     - PWM debug"));
        Serial.println(F("  ?DETMON / ?DETMOFF     - ETM debug"));

    // ================================================================
    } else if (c == "MAP") {
        Serial.println(F("---------------------------------------------------"));
        Serial.println(F("---------------------------------------------------"));
        Serial.println(F("\nUsage: ?MAP,<type>,<options>"));
        Serial.println(F("\nDescription:"));
        Serial.println(F("  Configures how data is routed between serial ports, both locally"));
        Serial.println(F("  and across WCB boards via ESP-NOW. Two mapping types exist:"));
        Serial.println(F("  SERIAL maps string commands from one port to destinations."));
        Serial.println(F("  PWM maps RC pulse-width signals from an input port to outputs."));
        Serial.println(F("  Mappings are saved to NVS and restored on reboot."));
        Serial.println(F("\nSERIAL Commands:"));
        Serial.println(F("  SERIAL,Sx,dest        Map port x to destination (string/command mode)"));
        Serial.println(F("                          Data is forwarded as text strings"));
        Serial.println(F("  SERIAL,Sx,R,dest      Map port x to destination (raw/binary mode)"));
        Serial.println(F("                          Raw bytes forwarded, no string processing"));
        Serial.println(F("  SERIAL,LIST           List all active serial mappings"));
        Serial.println(F("  SERIAL,CLEAR,Sx       Remove mapping for port x"));
        Serial.println(F("  SERIAL,CLEAR,ALL      Remove all serial mappings"));
        Serial.println(F("\nPWM Commands:"));
        Serial.println(F("  PWM,Sx,dest           Map PWM input port x to destination"));
        Serial.println(F("                          Triggers reboot to apply pin changes"));
        Serial.println(F("  PWM,OUT,Sx            Designate port x as PWM output only"));
        Serial.println(F("                          Used on remote boards receiving PWM"));
        Serial.println(F("  PWM,LIST              List all active PWM mappings"));
        Serial.println(F("  PWM,CLEAR,Sx          Remove PWM mapping for port x"));
        Serial.println(F("  PWM,CLEAR,ALL         Remove all PWM mappings"));
        Serial.println(F("\nCombined:"));
        Serial.println(F("  CLEAR,ALL             Remove ALL serial and PWM mappings"));
        Serial.println(F("\nDestination format:"));
        Serial.println(F("  Sx                    Local serial port x (1-5)"));
        Serial.println(F("  WxSy                  Remote WCB x, serial port y"));
        Serial.println(F("  Multiple destinations can be comma separated"));
        Serial.println(F("\nExamples:"));
        Serial.println(F("  ?MAP,SERIAL,S3,S4              - Forward S3 to local S4"));
        Serial.println(F("  ?MAP,SERIAL,S3,W2S1            - Forward S3 to WCB2 S1"));
        Serial.println(F("  ?MAP,SERIAL,S3,R,S4            - Forward S3 raw to S4"));
        Serial.println(F("  ?MAP,PWM,S3,S4                 - PWM passthrough S3 to S4"));
        Serial.println(F("  ?MAP,PWM,S3,W2S1               - PWM passthrough S3 to WCB2 S1"));
        Serial.println(F("  ?MAP,PWM,OUT,S4                - Set S4 as PWM output"));
        Serial.println(F("\nNotes:"));
        Serial.println(F("  - PWM input ports cannot be used for normal serial communication"));
        Serial.println(F("  - PWM cannot use the Kyber port (Kyber LOCAL) or S1 (Maestro REMOTE)"));
        Serial.println(F("  - Remote PWM destinations auto-configure the remote board"));
        Serial.println(F("  - PWM mappings trigger a reboot to apply hardware changes"));
        Serial.println(F("\nLegacy commands:"));
        Serial.println(F("  ?SMSx,dest    / ?SMSxR,dest    - Serial map string/raw"));
        Serial.println(F("  ?SMRSx        - Remove serial mapping"));
        Serial.println(F("  ?SMLIST       - List serial mappings"));
        Serial.println(F("  ?SMCLEAR      - Clear all serial mappings"));
        Serial.println(F("  ?PMSx,dest    - PWM map"));
        Serial.println(F("  ?POSx         - PWM output port"));
        Serial.println(F("  ?PRSx         - Remove PWM mapping"));
        Serial.println(F("  ?PLIST        - List PWM mappings"));
        Serial.println(F("  ?PCLEAR       - Clear all PWM mappings"));

    // ================================================================
    } else if (c == "BAUD") {
        Serial.println(F("---------------------------------------------------"));
        Serial.println(F("---------------------------------------------------"));
        Serial.println(F("\nUsage: ?BAUD,Sx,<rate>"));
        Serial.println(F("\nDescription:"));
        Serial.println(F("  Sets the baud rate for a serial port and saves it to NVS."));
        Serial.println(F("  Takes effect immediately without reboot."));
        Serial.println(F("  Hardware serial (S1, S2) supports all standard rates."));
        Serial.println(F("  Software serial (S3, S4, S5) works best at 9600-57600."));
        Serial.println(F("\nParameters:"));
        Serial.println(F("  Sx            Serial port number (S1-S5)"));
        Serial.println(F("  rate          Baud rate - valid values:"));
        Serial.println(F("                  110, 300, 600, 1200, 2400, 9600, 14400,"));
        Serial.println(F("                  19200, 38400, 57600, 115200, 128000, 256000"));
        Serial.println(F("\nExamples:"));
        Serial.println(F("  ?BAUD,S1,57600     - Set S1 to 57600 (Maestro default)"));
        Serial.println(F("  ?BAUD,S2,9600      - Set S2 to 9600"));
        Serial.println(F("  ?BAUD,S3,38400     - Set S3 to 38400"));
        Serial.println(F("\nNotes:"));
        Serial.println(F("  - Default baud rate for all ports is 9600"));
        Serial.println(F("  - Maestro servo controllers require 57600"));
        Serial.println(F("  - Configure a Maestro with ?MAESTRO,M<id>:W<wcb>S<port>:<baud> (see ?MAESTRO)"));
        Serial.println(F("  - Saved to NVS, persists across reboots"));
        Serial.println(F("\nLegacy commands:"));
        Serial.println(F("  ?BAUDSx,rate  (e.g. ?BAUDS1,57600)"));
        Serial.println(F("  ?Sxrate       (e.g. ?S157600 - no comma; ?Sx,rate is NOT accepted)"));

    // ================================================================
    } else if (c == "LABEL") {
        Serial.println(F("---------------------------------------------------"));
        Serial.println(F("---------------------------------------------------"));
        Serial.println(F("\nUsage: ?LABEL,Sx,<text>  /  ?LABEL,CLEAR,Sx  /  ?LABEL,CLEAR,ALL"));
        Serial.println(F("\nDescription:"));
        Serial.println(F("  Assigns a human-readable label to a serial port. Labels appear"));
        Serial.println(F("  in debug output and config listings to make it easier to identify"));
        Serial.println(F("  which device is connected to which port."));
        Serial.println(F("\nCommands:"));
        Serial.println(F("  Sx,text           Set label for port x"));
        Serial.println(F("                      Maximum 30 characters"));
        Serial.println(F("  CLEAR,Sx          Remove label from port x"));
        Serial.println(F("  CLEAR,ALL         Remove all port labels"));
        Serial.println(F("\nExamples:"));
        Serial.println(F("  ?LABEL,S1,Marcduino"));
        Serial.println(F("  ?LABEL,S2,MP3 Trigger"));
        Serial.println(F("  ?LABEL,S3,Periscope"));
        Serial.println(F("  ?LABEL,CLEAR,S1"));
        Serial.println(F("  ?LABEL,CLEAR,ALL"));
        Serial.println(F("\nNotes:"));
        Serial.println(F("  - Labels are saved to NVS and persist across reboots"));
        Serial.println(F("  - Labels appear in ?CONFIG and ?BACKUP output"));
        Serial.println(F("  - Labels appear in debug serial output when enabled"));
        Serial.println(F("\nLegacy commands:"));
        Serial.println(F("  ?SLSx,label   - Set label  (e.g. ?SLS1,Marcduino)"));
        Serial.println(F("  ?SLCSx        - Clear label (e.g. ?SLCS1)"));

    // ================================================================
    } else if (c == "BCAST") {
        Serial.println(F("---------------------------------------------------"));
        Serial.println(F("---------------------------------------------------"));
        Serial.println(F("\nUsage: ?BCAST,<IN/OUT>,Sx,<ON/OFF>  /  ?BCAST,RESET"));
        Serial.println(F("\nDescription:"));
        Serial.println(F("  Controls broadcast behavior per serial port. Two independent"));
        Serial.println(F("  settings exist per port: INPUT controls whether commands received"));
        Serial.println(F("  on that port get broadcast to other ports and ESP-NOW. OUTPUT"));
        Serial.println(F("  controls whether broadcast commands get sent OUT that port."));
        Serial.println(F("\nCommands:"));
        Serial.println(F("  IN,Sx,ON          Allow broadcasts from port x input"));
        Serial.println(F("                      Commands received on Sx will be broadcast"));
        Serial.println(F("  IN,Sx,OFF         Block broadcasts from port x input"));
        Serial.println(F("                      Commands received on Sx stay local only"));
        Serial.println(F("  OUT,Sx,ON         Include port x in broadcast output"));
        Serial.println(F("                      Broadcast commands will be sent to Sx"));
        Serial.println(F("  OUT,Sx,OFF        Exclude port x from broadcast output"));
        Serial.println(F("                      Broadcast commands will NOT be sent to Sx"));
        Serial.println(F("  RESET             Reset all broadcast settings to defaults"));
        Serial.println(F("                      All ports enabled for input and output"));
        Serial.println(F("\nExamples:"));
        Serial.println(F("  ?BCAST,IN,S3,OFF       - Don't broadcast S3 input (e.g. sensor)"));
        Serial.println(F("  ?BCAST,OUT,S2,OFF      - Don't send broadcasts to S2"));
        Serial.println(F("  ?BCAST,IN,S1,ON        - Re-enable broadcasting from S1"));
        Serial.println(F("  ?BCAST,RESET           - Restore all defaults"));
        Serial.println(F("\nNotes:"));
        Serial.println(F("  - Settings are saved to NVS and persist across reboots"));
        Serial.println(F("  - Serial mappings (?MAP,SERIAL) override broadcast behavior"));
        Serial.println(F("  - Maestro ports are automatically excluded from broadcasts"));
        Serial.println(F("  - PWM output ports are automatically excluded from broadcasts"));
        Serial.println(F("\nLegacy commands:"));
        Serial.println(F("  ?SBISxON / ?SBISxOFF   - Broadcast input  (e.g. ?SBIS3OFF)"));
        Serial.println(F("  ?SBOSxON / ?SBOSxOFF   - Broadcast output (e.g. ?SBOS2OFF)"));
        Serial.println(F("  ?RESET_BROADCAST        - Reset all settings"));

    // ================================================================
    } else if (c == "KYBER") {
        Serial.println(F("---------------------------------------------------"));
        Serial.println(F("---------------------------------------------------"));
        Serial.println(F("\nUsage: ?KYBER,<command>"));
        Serial.println(F("\nDescription:"));
        Serial.println(F("  Configures integration with the Kyber RC system for lightsaber"));
        Serial.println(F("  and droid sound/motion control. Kyber communicates via a"));
        Serial.println(F("  proprietary serial protocol that is forwarded across WCB boards."));
        Serial.println(F("  LOCAL means Kyber is physically connected to this board."));
        Serial.println(F("  REMOTE means the Maestro is local but Kyber is on another board."));
        Serial.println(F("\nCommands:"));
        Serial.println(F("  LOCAL             Kyber on this board, broadcast mode"));
        Serial.println(F("                      Keeps the Kyber's current port (S2 if not local yet)"));
        Serial.println(F("                      The other hardware port stays normal (Maestro, device or PWM)"));
        Serial.println(F("                      Kyber data broadcast to all remote WCBs"));
        Serial.println(F("  LOCAL,Sx,Mx:WxSx:baud,...  Configure Kyber local AND all Maestros"));
        Serial.println(F("                                in a single command"));
        Serial.println(F("                                Sx  = Kyber serial port on this board"));
        Serial.println(F("                                Then list Maestro configs same as ?MAESTRO"));
        Serial.println(F("                                Generates copy-paste setup for all WCBs"));
        Serial.println(F("  REMOTE            Maestro local, Kyber on another board"));
        Serial.println(F("                      S1=Maestro only"));
        Serial.println(F("                      Receives Kyber data via ESP-NOW"));
        Serial.println(F("  CLEAR             Disable Kyber integration entirely"));
        Serial.println(F("  LIST              Show current Kyber configuration and targets"));
        Serial.println(F("\nExamples:"));
        Serial.println(F("  ?KYBER,LOCAL      - Kyber here, broadcast mode (current port, else S2)"));
        Serial.println(F("  ?KYBER,LOCAL,S1,M1:W1S2:115200,M2:W2S1:115200,M3:W3S1:57600"));
        Serial.println(F("  ?MAESTRO,REMOTE   - This board has Maestro, controller elsewhere (canonical)"));
        Serial.println(F("  ?KYBER,REMOTE     - Alias for ?MAESTRO,REMOTE (same function)"));
        Serial.println(F("  ?KYBER,CLEAR      - Disable Kyber"));
        Serial.println(F("  ?KYBER,LIST       - Show configuration"));
        Serial.println(F("\nNotes:"));
        Serial.println(F("  - 'REMOTE' = this board hosts a Maestro driven remotely (Kyber OR NaviCore)."));
        Serial.println(F("    It accepts Pololu/Maestro packets over the mesh. ?MAESTRO,REMOTE is the"));
        Serial.println(F("    canonical name; ?KYBER,REMOTE remains a working alias."));
        Serial.println(F("  - Kyber LOCAL owns only its own port: S1 or S2 (S3-S5 are refused)."));
        Serial.println(F("    That port cannot also host a local Maestro - either command refuses it."));
        Serial.println(F("    The other hardware port is an ordinary port (command, Maestro, device or PWM)."));
        Serial.println(F("  - Moving the Kyber to the other port, ?MAESTRO,REMOTE and ?KYBER,CLEAR each give"));
        Serial.println(F("    the old Kyber port back (9600 baud, broadcasts in/out on) unless a Maestro or"));
        Serial.println(F("    another device is configured there."));
        Serial.println(F("  - Targeted mode: a local Maestro's Kyber target follows its slot - a new"));
        Serial.println(F("    ?MAESTRO slot adds it, ?MAESTRO,CLEAR removes it (the freed port then"));
        Serial.println(F("    follows its ?BCAST flags)."));
        Serial.println(F("  - HCR/MP3/DFP/WLED and PWM refuse only the Kyber's own port"));
        Serial.println(F("  - REMOTE reserves S1 only (Maestro)"));
        Serial.println(F("  - ?KYBER,LOCAL refuses a port a device, PWM or local Maestro already uses"));
        Serial.println(F("  - Setting is saved to NVS and restored on reboot"));
        Serial.println(F("  - Reboot required after changing mode"));
        Serial.println(F("\nLegacy commands:"));
        Serial.println(F("  ?KYBER_LOCAL / ?KYBER_REMOTE / ?KYBER_CLEAR / ?KYBER_LIST"));
        Serial.println(F("  ?MAESTRO_REMOTE  (canonical underscore form)"));

    // ================================================================
    } else if (c == "ETM") {
        Serial.println(F("---------------------------------------------------"));
        Serial.println(F("---------------------------------------------------"));
        Serial.println(F("\nUsage: ?ETM,<command>[,value]"));
        Serial.println(F("\nDescription:"));
        Serial.println(F("  Ensured Transmission Mode (ETM) guarantees command delivery"));
        Serial.println(F("  between WCB boards using ACK packets, automatic retries, and"));
        Serial.println(F("  heartbeat monitoring. When enabled, every unicast and broadcast"));
        Serial.println(F("  command is acknowledged. Unacknowledged commands are retried up"));
        Serial.println(F("  to 3 times before being marked as failed. Heartbeats track which"));
        Serial.println(F("  boards are online. ALL boards must have ETM set the same way or"));
        Serial.println(F("  messages will be silently ignored."));
        Serial.println(F("\nCommands:"));
        Serial.println(F("  ON                Enable ETM on this board"));
        Serial.println(F("  OFF               Disable ETM on this board"));
        Serial.println(F("  TIMEOUT,ms        Milliseconds to wait for ACK before retry"));
        Serial.println(F("                      Default: 500ms"));
        Serial.println(F("                      Recommended: run ?ETM,CHAR to find best value"));
        Serial.println(F("  HB,sec            Heartbeat broadcast interval in seconds"));
        Serial.println(F("                      Default: 10 sec (+/- 1 sec random)"));
        Serial.println(F("  MISS,count        Missed heartbeats before board marked offline"));
        Serial.println(F("                      Default: 3"));
        Serial.println(F("  BOOT,sec          Random heartbeat window on boot"));
        Serial.println(F("                      Prevents all boards transmitting simultaneously"));
        Serial.println(F("                      Default: 2 sec"));
        Serial.println(F("  COUNT,n           Test messages per board per phase during CHAR"));
        Serial.println(F("                      Range: 10-200, Default: 20"));
        Serial.println(F("  DELAY,ms          Delay between messages during CHAR"));
        Serial.println(F("                      Default: 100ms"));
        Serial.println(F("  CHAR              Run network characterization test"));
        Serial.println(F("                      Tests 3 phases: baseline, broadcast, loaded"));
        Serial.println(F("                      Outputs recommended TIMEOUT value when done"));
        Serial.println(F("                      ETM debug is auto-disabled during test for"));
        Serial.println(F("                      accurate timing and restored when complete"));
        Serial.println(F("  CHKSM,ON/OFF      Enable/disable CRC32 checksum on ETM packets"));
        Serial.println(F("                      Detects corrupted packets before execution"));
        Serial.println(F("                      Default: ON"));
        Serial.println(F("                      ALL boards must match or packets are rejected"));
        Serial.println(F("\nExamples:"));
        Serial.println(F("  ?ETM,ON"));
        Serial.println(F("  ?ETM,TIMEOUT,300"));
        Serial.println(F("  ?ETM,HB,15"));
        Serial.println(F("  ?ETM,MISS,5"));
        Serial.println(F("  ?ETM,CHAR"));
        Serial.println(F("\nNotes:"));
        Serial.println(F("  - ETM packet size is 252 bytes vs 249 bytes normal"));
        Serial.println(F("  - PWM passthrough always bypasses ETM for low latency"));
        Serial.println(F("  - Raw Kyber data always bypasses ETM"));
        Serial.println(F("  - Boards not yet seen via heartbeat will still receive commands"));
        Serial.println(F("  - Run ?ETM,CHAR before setting TIMEOUT for best results"));
        Serial.println(F("  - Settings saved to NVS and persist across reboots"));
        Serial.println(F("  - CHKSM adds 12 bytes overhead, reducing max command to 187 chars"));
        Serial.println(F("  - CHKSM must match across all boards or all packets are rejected"));
        Serial.println(F("\nLegacy commands:"));
        Serial.println(F("  ?ETMON / ?ETMOFF"));
        Serial.println(F("  ?ETMTIMEOUTms      (e.g. ?ETMTIMEOUT300)"));
        Serial.println(F("  ?ETMHBsec          (e.g. ?ETMHB10)"));
        Serial.println(F("  ?ETMMISScount      (e.g. ?ETMMISS3)"));
        Serial.println(F("  ?ETMBOOTsec        (e.g. ?ETMBOOT2)"));
        Serial.println(F("  ?ETMCHARCOUNTn     (e.g. ?ETMCHARCOUNT20)"));
        Serial.println(F("  ?ETMCHARDELAYms    (e.g. ?ETMCHARDELAY100)"));
        Serial.println(F("  ?ETMCHAR"));

    // ================================================================
    } else if (c == "MAC") {
        Serial.println(F("---------------------------------------------------"));
        Serial.println(F("---------------------------------------------------"));
        Serial.println(F("\nUsage: ?MAC,<octet>,<hex_value>"));
        Serial.println(F("\nDescription:"));
        Serial.println(F("  Sets the 2nd and 3rd octets of the ESP-NOW MAC address used by"));
        Serial.println(F("  all WCB boards. These two octets form a group identifier - only"));
        Serial.println(F("  boards sharing the same octets 2 and 3 will communicate with"));
        Serial.println(F("  each other. This allows multiple independent WCB systems to"));
        Serial.println(F("  operate in the same RF space without interference."));
        Serial.println(F("\nParameters:"));
        Serial.println(F("  octet         Which octet to set: 2 or 3"));
        Serial.println(F("  hex_value     Two hex digits (00-FF)"));
        Serial.println(F("\nExamples:"));
        Serial.println(F("  ?MAC,2,AB          - Set 2nd octet to 0xAB"));
        Serial.println(F("  ?MAC,3,CD          - Set 3rd octet to 0xCD"));
        Serial.println(F("\nNotes:"));
        Serial.println(F("  - ALL boards in the same system must have identical octets 2 and 3"));
        Serial.println(F("  - Default value is 0x00 for both octets"));
        Serial.println(F("  - Full MAC format: 02:xx:xx:00:00:WCB# (xx = your octets)"));
        Serial.println(F("  - The receive filter changes at once, so this board stops hearing the old group;"));
        Serial.println(F("    its own address and its peers' change at the next reboot - reboot every board"));
        Serial.println(F("  - Saved to NVS and persists across reboots"));
        Serial.println(F("\nLegacy commands:"));
        Serial.println(F("  ?M2xx   (e.g. ?M2AB)"));
        Serial.println(F("  ?M3xx   (e.g. ?M3CD)"));

    // ================================================================
    } else if (c == "EPASS") {
        Serial.println(F("---------------------------------------------------"));
        Serial.println(F("---------------------------------------------------"));
        Serial.println(F("\nUsage: ?EPASS,<password>"));
        Serial.println(F("\nDescription:"));
        Serial.println(F("  Sets the ESP-NOW network password used to validate incoming"));
        Serial.println(F("  messages. Only messages containing the correct password are"));
        Serial.println(F("  processed. This provides a basic layer of protection against"));
        Serial.println(F("  messages from other ESP-NOW devices in the area."));
        Serial.println(F("\nParameters:"));
        Serial.println(F("  password      1-39 characters, lowercase recommended"));
        Serial.println(F("\nExamples:"));
        Serial.println(F("  ?EPASS,mysecretpassword"));
        Serial.println(F("  ?EPASS,r2d2_droid_network"));
        Serial.println(F("\nNotes:"));
        Serial.println(F("  - ALL boards in the system must use the same password"));
        Serial.println(F("  - Default: change_me_or_risk_takeover"));
        Serial.println(F("  - Maximum 39 characters"));
        Serial.println(F("  - Saved to NVS and persists across reboots"));
        Serial.println(F("  - Takes effect immediately without reboot"));
        Serial.println(F("\nLegacy commands:"));
        Serial.println(F("  ?EPASSpassword   (e.g. ?EPASSmy_password)"));

    // ================================================================
    } else if (c == "WCB") {
        Serial.println(F("---------------------------------------------------"));
        Serial.println(F("---------------------------------------------------"));
        Serial.println(F("\nUsage: ?WCB,<number>"));
        Serial.println(F("\nDescription:"));
        Serial.println(F("  Sets this board's WCB number (1-20). The WCB number determines"));
        Serial.println(F("  the board's MAC address and how it is addressed in unicast"));
        Serial.println(F("  commands. Each board in a system must have a unique number."));
        Serial.println(F("  WCB1 is typically the primary/master board."));
        Serial.println(F("\nParameters:"));
        Serial.println(F("  number        1-20, must be unique in the system"));
        Serial.println(F("\nExamples:"));
        Serial.println(F("  ?WCB,1         - Set this board as WCB1"));
        Serial.println(F("  ?WCB,2         - Set this board as WCB2"));
        Serial.println(F("\nNotes:"));
        Serial.println(F("  - Reboot required after changing WCB number"));
        Serial.println(F("  - MAC address last byte will be set to this number"));
        Serial.println(F("  - Use ?WCBQ to set the total number of boards in the system"));
        Serial.println(F("  - Saved to NVS and persists across reboots"));
        Serial.println(F("\nLegacy commands:"));
        Serial.println(F("  ?WCBx   (e.g. ?WCB2)"));

    // ================================================================
    } else if (c == "WCBQ") {
        Serial.println(F("---------------------------------------------------"));
        Serial.println(F("---------------------------------------------------"));
        Serial.println(F("\nUsage: ?WCBQ,<quantity>"));
        Serial.println(F("\nDescription:"));
        Serial.println(F("  Sets the baseline (FLOOR) number of WCB boards in the system —"));
        Serial.println(F("  boards 1..quantity are always registered as ESP-NOW peers. With WDP"));
        Serial.println(F("  auto-join on (the default), boards heard on the mesh beyond this floor"));
        Serial.println(F("  are added automatically, so WCBQ no longer has to cover every board."));
        Serial.println(F("\nParameters:"));
        Serial.println(F("  quantity      Baseline number of WCB boards (1-20)"));
        Serial.println(F("\nExamples:"));
        Serial.println(F("  ?WCBQ,1        - Single board (rely on auto-join for the rest)"));
        Serial.println(F("  ?WCBQ,2        - Two board floor"));
        Serial.println(F("  ?WCBQ,3        - Three board floor"));
        Serial.println(F("\nNotes:"));
        Serial.println(F("  - Takes effect immediately — peer registrations reconcile live (no reboot)"));
        Serial.println(F("  - WDP auto-join (?WDP,AUTOJOIN) can extend membership above this floor"));
        Serial.println(F("  - ETM uses membership to know which boards to expect heartbeats from"));
        Serial.println(F("  - Saved to NVS and persists across reboots"));
        Serial.println(F("\nLegacy commands:"));
        Serial.println(F("  ?WCBQx   (e.g. ?WCBQ2)"));

    // ================================================================
    } else if (c == "MAESTRO") {
        Serial.println(F("---------------------------------------------------"));
        Serial.println(F("---------------------------------------------------"));
        Serial.println(F("\nUsage: ?MAESTRO,<command>[,options]"));
        Serial.println(F("\nDescription:"));
        Serial.println(F("  Configures Pololu Maestro servo controller integration. Multiple"));
        Serial.println(F("  Maestro controllers can be configured across different WCB boards."));
        Serial.println(F("  Each Maestro is assigned an ID (M1-M8) and mapped to a specific"));
        Serial.println(F("  WCB board and serial port. Commands targeting a Maestro ID are"));
        Serial.println(F("  automatically routed to the correct board and port."));
        Serial.println(F("\nCommands:"));
        Serial.println(F("  Mx:WxSx:baud      Configure a Maestro mapping"));
        Serial.println(F("                      Mx  = Maestro ID (M1-M8; 9 & 0 are reserved"));
        Serial.println(F("                            runtime targets - all-local / all)"));
        Serial.println(F("                      WxSx = WCB number and serial port"));
        Serial.println(F("                      baud = serial baud rate (usually 57600)"));
        Serial.println(F("  LIST              List all configured Maestro mappings"));
        Serial.println(F("  CLEAR,x           Clear Maestro config by ID number"));
        Serial.println(F("  CLEAR,ALL         Clear all Maestro configurations"));
        Serial.println(F("\nExamples:"));
        Serial.println(F("  ?MAESTRO,M1:W1S1:57600              - Maestro 1 on WCB1 S1"));
        Serial.println(F("  ?MAESTRO,M1:W1S1:57600,M2:W2S1:57600 - Two Maestros"));
        Serial.println(F("  ?MAESTRO,LIST                       - Show all configurations"));
        Serial.println(F("  ?MAESTRO,CLEAR,ALL                  - Remove all configs"));
        Serial.println(F("\nTriggering a Maestro at runtime (;M commands):"));
        Serial.println(F("  ;M<id><seq>            Restart script at subroutine (NO comma)"));
        Serial.println(F("                           id 1-8 = a Maestro ; seq = 0-255"));
        Serial.println(F("                           ;M11 = Maestro1 sub1 ; ;M25 = M2 sub5"));
        Serial.println(F("                           ;M0<seq> = ALL Maestros (e.g. ;M02)"));
        Serial.println(F("                           ;M9<seq> = all LOCAL Maestros (this board)"));
        Serial.println(F("  ;M<dev>,<n>[,<param>]  Same trigger, comma spelling. ;M1,1 is"));
        Serial.println(F("                           identical to ;M11. Optional param -> 0x28."));
        Serial.println(F("  ;M<dev>,<verb>[,args]  Native Pololu servo/query (dev 1-8; 0=all, 9=local):"));
        Serial.println(F("    setTarget,<ch>,<val>   channel <ch> to target (1/4-us, 0-16383)"));
        Serial.println(F("    setSpeed,<ch>,<val>    channel speed limit (0-16383)"));
        Serial.println(F("    setAccel,<ch>,<val>    channel acceleration (0-255)"));
        Serial.println(F("    goHome                 all channels to home"));
        Serial.println(F("    stopScript             stop the running Maestro script"));
        Serial.println(F("    sub,<n>[,<param>]      run subroutine <n> 0-255 [+param 0-16383]"));
        Serial.println(F("    getPosition,<ch>       -> RAM var m<dev>pos<ch>  (0-16383)"));
        Serial.println(F("    getMovingState         -> RAM var m<dev>moving   (0 or 1)"));
        Serial.println(F("    getErrors              -> RAM var m<dev>err (clears on read)"));
        Serial.println(F("    e.g. ;M2,setTarget,0,6000  ;M2,goHome  ;M5,setSpeed,3,10"));
        Serial.println(F("  After the comma: a number = subroutine, a verb name = servo."));
        Serial.println(F("  A bad verb/arg is rejected (nothing is sent to the Maestro)."));
        Serial.println(F("\nget* queries are ASYNC (device 1-8 only): the reply lands in a"));
        Serial.println(F("  RAM variable (not saved to NVS) that IF reads. Query and IF must"));
        Serial.println(F("  be SEPARATE triggers (IF evaluates when its chain is invoked, so"));
        Serial.println(F("  the reply must already have arrived, ~5ms):"));
        Serial.println(F("    step1:  ;M2,getMovingState"));
        Serial.println(F("    step2:  IF,m2moving=0^;SEQnextmove   (triggered after step1)"));
        Serial.println(F("  Cross-board: issue the query from the ASKING board (;M2,getMovingState);"));
        Serial.println(F("  it auto-forwards to the host and the answer routes back to THIS board's"));
        Serial.println(F("  RAM var. Do NOT ;w-wrap a get — the reply would stay on the target board."));
        Serial.println(F("\nNotes:"));
        Serial.println(F("  - Maestro requires 57600 baud on the connected serial port"));
        Serial.println(F("  - Set baud rate with: ?BAUD,Sx,57600"));
        Serial.println(F("  - Commands are sent as binary Pololu protocol packets"));
        Serial.println(F("  - Trigger scripts / drive servos with the ;M runtime commands above"));
        Serial.println(F("  - Saved to NVS and persists across reboots"));
        Serial.println(F("  - No slot for this board's own id? ;M<own id>, ;M9 and the ;M0 extra frame use the"));
        Serial.println(F("    legacy Maestro on S1 (device id = WCB number) - unless S1 is the Kyber port or"));
        Serial.println(F("    an HCR/MP3/DFPlayer/WLED/PWM port, when nothing is sent."));
        Serial.println(F("\nLegacy commands:"));
        Serial.println(F("  ?MAESTRO_LIST / ?MAESTRO_CLEAR (every slot) / ?MAESTRO_DEFAULT"));
        Serial.println(F("  ?MAESTROconfig    (e.g. ?MAESTROM1:W1S1:57600)"));

    // ================================================================
    } else if (c == "MP3") {
        Serial.println(F("---------------------------------------------------"));
        Serial.println(F("---------------------------------------------------"));
        Serial.println(F("\nUsage: ?MP3,<command>[,options]"));
        Serial.println(F("\nDescription:"));
        Serial.println(F("  Configures and controls a SparkFun MP3 Trigger v2.x connected to"));
        Serial.println(F("  a local serial port. One MP3 Trigger per WCB board. Any free serial"));
        Serial.println(F("  port (S1-S5) can be used. Audio commands are sent via ;A,..."));
        Serial.println(F("  Volume is sent automatically before every play command."));
        Serial.println(F("\nConfiguration Commands:"));
        Serial.println(F("  S<port>:<baud>:V<vol>  Configure MP3 Trigger (all fields required)"));
        Serial.println(F("                           port: 1-5 (any free port)"));
        Serial.println(F("                           baud: 9600 or 38400 (either works on any port)"));
        Serial.println(F("                           vol:  0-64 (0=loudest, 64=inaudible)"));
        Serial.println(F("  LIST                   Show current configuration"));
        Serial.println(F("  CLEAR                  Remove configuration, free the port"));
        Serial.println(F("  ONERR,<key>            Run stored command <key> on device error"));
        Serial.println(F("  ONERR,CLEAR            Remove error callback"));
        Serial.println(F("\nExamples:"));
        Serial.println(F("  ?MP3,S2:9600:V25              - MP3 Trigger on S2, 9600 baud, vol 25"));
        Serial.println(F("  ?MP3,S1:38400:V20             - S1 at 38400 baud, vol 20"));
        Serial.println(F("  ?MP3,LIST                     - Show configuration"));
        Serial.println(F("  ?MP3,CLEAR                    - Remove configuration"));
        Serial.println(F("  ?MP3,ONERR,errsequence        - Run ;Cerrsequence on error"));
        Serial.println(F("  ?MP3,ONERR,CLEAR              - Remove error callback"));
        Serial.println(F("\nAudio Playback Commands (use ;A,...):"));
        Serial.println(F("  ;A,PLAY,<n>                Play track n (1-255, by filename order)"));
        Serial.println(F("  ;A,PLAY,<n>,ONFIN,<key>    Play track n, run ;C<key> when finished"));
        Serial.println(F("  ;A,PLAY,<n>,<key>          Same — implicit callback syntax"));
        Serial.println(F("  ;A,PLAYFS,<n>              Play track n (0-255, by SD card order)"));
        Serial.println(F("  ;A,PLAYFS,<n>,ONFIN,<key>  Play by SD order with finish callback"));
        Serial.println(F("  ;A,PLAYFS,<n>,<key>        Same — implicit callback syntax"));
        Serial.println(F("  ;A,STOP                    Start/Stop toggle"));
        Serial.println(F("  ;A,NEXT                    Skip to next track"));
        Serial.println(F("  ;A,PREV                    Skip to previous track"));
        Serial.println(F("  ;A,VOL,<n>                 Set volume: 0=loudest, 64=inaudible"));
        Serial.println(F("  ;A,VOLUP                   Louder by 5 steps (floor: 0)"));
        Serial.println(F("  ;A,VOLDN                   Quieter by 5 steps (ceiling: 64)"));
        Serial.println(F("  ;A,COUNT                   Request total track count (prints to USB)"));
        Serial.println(F("  ;A,VER                     Request firmware version (prints to USB)"));
        Serial.println(F("\nCallback Notes:"));
        Serial.println(F("  - Callbacks are per-play only — not global"));
        Serial.println(F("  - New ;A,PLAY overwrites any pending callback from previous play"));
        Serial.println(F("  - 'X' (finished) fires callback  |  'x' (cancelled) clears it"));
        Serial.println(F("  - Callback key refers to a stored sequence (see ?SEQ)"));
        Serial.println(F("\nStatus Responses (printed to USB serial):"));
        Serial.println(F("  [MP3] Track finished  - Received 'X' — track completed normally"));
        Serial.println(F("  [MP3] Track cancelled - Received 'x' — stopped during playback"));
        Serial.println(F("  [MP3] Error: ...      - Received 'E' — track not found or fault"));
        Serial.println(F("  [MP3] Status: ...     - Received '=' string (version / track count)"));
        Serial.println(F("\nMulti-WCB Usage:"));
        Serial.println(F("  Each WCB has its own MP3 Trigger on its own serial port."));
        Serial.println(F("  To trigger audio on another WCB, use the ;W routing:"));
        Serial.println(F("    ;W2,;A,PLAY,5             Play track 5 on WCB2's MP3 Trigger"));
        Serial.println(F("    ;W2,;A,PLAY,5,ONFIN,done  Play on WCB2 with finish callback"));
        Serial.println(F("\nNotes:"));
        Serial.println(F("  - Port is dedicated: broadcast I/O is disabled on the MP3 port"));
        Serial.println(F("  - Volume is sent before every PLAY/PLAYFS command automatically"));
        Serial.println(F("  - Current volume tracked in NVS and persists across reboots"));
        Serial.println(F("  - MP3 Trigger always boots at full volume (hardware default)"));
        Serial.println(F("  - Saved to NVS and persists across reboots"));

    // ================================================================
    } else if (c == "DFP" || c == "DFPLAYER") {
        Serial.println(F("---------------------------------------------------"));
        Serial.println(F("---------------------------------------------------"));
        Serial.println(F("\nUsage: ?DFP,<command>[,options]   (config/query)"));
        Serial.println(F("       ;D,<command>[,options]    (runtime playback)"));
        Serial.println(F("\nDescription:"));
        Serial.println(F("  Configures and controls a DFRobot DFPlayer Mini (and YX5300 /"));
        Serial.println(F("  MH2024K clones) on a local serial port. One DFPlayer per WCB."));
        Serial.println(F("  It is the ALTERNATE audio device to the MP3 Trigger (?MP3 / ;A);"));
        Serial.println(F("  a board can host both, on different ports."));
        Serial.println(F("\n  TWO DIFFERENCES FROM THE MP3 TRIGGER:"));
        Serial.println(F("    - Baud is FIXED at 9600 by the module. Nothing else works."));
        Serial.println(F("    - Volume is 0-30 where 0=SILENT and 30=LOUDEST. That is the"));
        Serial.println(F("      INVERSE of the MP3 Trigger's 0-64 (0=loudest). Do not copy"));
        Serial.println(F("      a volume value between the two."));
        Serial.println(F("\nConfiguration Commands:"));
        Serial.println(F("  S<port>[:<baud>][:V<vol>]  Configure DFPlayer"));
        Serial.println(F("                           port: 1-5 (any free port)"));
        Serial.println(F("                           baud: optional, must be 9600"));
        Serial.println(F("                           vol:  0-30 (0=silent, 30=loudest)"));
        Serial.println(F("  LIST                   Show current configuration"));
        Serial.println(F("  CLEAR                  Remove configuration, free the port"));
        Serial.println(F("  REMOTE,W<n>            Route ;D to the DFPlayer on WCB<n>"));
        Serial.println(F("  REMOTE,OFF             Stop routing ;D to a remote host"));
        Serial.println(F("  ONERR,<key>            Run stored command <key> on device error"));
        Serial.println(F("  ONERR,CLEAR            Remove error callback"));
        Serial.println(F("\nExamples:"));
        Serial.println(F("  ?DFP,S2                       - DFPlayer on S2, 9600 baud, vol 20"));
        Serial.println(F("  ?DFP,S2:9600:V20              - Same, fully spelled out"));
        Serial.println(F("  ?DFP,S3:V25                   - S3, baud implied, volume 25"));
        Serial.println(F("  ?DFP,LIST                     - Show configuration"));
        Serial.println(F("  ?DFP,CLEAR                    - Remove configuration"));
        Serial.println(F("\nPlayback Commands (use ;D,...):"));
        Serial.println(F("  ;D,PLAY,<n>                Play track n (1-2999, global index)"));
        Serial.println(F("  ;D,PLAY,<n>,ONFIN,<key>    Play track n, run ;C<key> when finished"));
        Serial.println(F("  ;D,FOLDER,<f>,<t>          Play /<f>/<t>.mp3 (f 1-99, t 1-255)"));
        Serial.println(F("  ;D,MP3FOLDER,<n>           Play track n from the /MP3 folder"));
        Serial.println(F("  ;D,STOP                    Stop playback"));
        Serial.println(F("  ;D,NEXT / ;D,PREV          Skip forward / back"));
        Serial.println(F("  ;D,PAUSE / ;D,RESUME       Pause / resume"));
        Serial.println(F("  ;D,RANDOM                  Play a random track"));
        Serial.println(F("  ;D,VOL,<n>                 Set volume: 0=silent, 30=loudest"));
        Serial.println(F("  ;D,VOLUP / ;D,VOLDN        Louder / quieter by 2 steps"));
        Serial.println(F("  ;D,LOOP,<n>                Repeat track n forever"));
        Serial.println(F("  ;D,LOOPALL,<0|1>           Loop the whole card off / on"));
        Serial.println(F("  ;D,LOOPFOLDER,<f>          Loop folder f"));
        Serial.println(F("  ;D,EQ,<0-5>                Normal/Pop/Rock/Jazz/Classic/Bass"));
        Serial.println(F("  ;D,DEVICE,<n>              1=USB 2=SD 3=AUX 4=Sleep 5=Flash"));
        Serial.println(F("  ;D,RESET                   Reset the module"));
        Serial.println(F("  ;D,STATUS                  Query play status (prints to USB)"));
        Serial.println(F("\nMulti-board:"));
        Serial.println(F("    ;W2,;D,PLAY,5             Play track 5 on WCB2's DFPlayer"));
        Serial.println(F("  A ;D on a board with no DFPlayer is auto-routed to the board"));
        Serial.println(F("  that advertises one (WDP capability), same as ;A and ;H."));
        Serial.println(F("\nNotes:"));
        Serial.println(F("  - Port is dedicated: broadcast I/O is disabled on the DFPlayer port"));
        Serial.println(F("  - A DFPlayer needs ~1.5-3s after power-on before it accepts commands"));
        Serial.println(F("  - Volume is NOT re-sent before each play (the module remembers it)"));
        Serial.println(F("  - Current volume tracked in NVS and persists across reboots"));
        Serial.println(F("  - Clone modules vary: RANDOM/EQ/LOOPFOLDER may be no-ops on some"));

    // ================================================================
    } else if (c == "HCR") {
        Serial.println(F("---------------------------------------------------"));
        Serial.println(F("---------------------------------------------------"));
        Serial.println(F("\nUsage: ?HCR,<command>[,options]   (config/query)"));
        Serial.println(F("       ;H,<command>[,options]    (runtime actions)"));
        Serial.println(F("\nDescription:"));
        Serial.println(F("  Native Human-Cyborg Relations (HCR) Vocalizer integration."));
        Serial.println(F("  One HCR per WCB on a reserved serial port. The WCB sends"));
        Serial.println(F("  commands and polls live status. Drive it locally (serial/web),"));
        Serial.println(F("  remotely (ESP-NOW unicast), or via the RC-Controller raw"));
        Serial.println(F("  forward - all to the same HCR."));
        Serial.println(F("\nConfiguration Commands (?HCR,...):"));
        Serial.println(F("  PORT,Sx:baud      Reserve & configure the HCR port"));
        Serial.println(F("                      baud: 9600/19200/38400/57600/115200"));
        Serial.println(F("                      (S3-S5 software serial: up to 57600)"));
        Serial.println(F("  CLEAR             Release the HCR port"));
        Serial.println(F("  LIST              Show HCR configuration and link status"));
        Serial.println(F("  POLL,<sec>        Auto-poll interval (default 10; OFF to stop)"));
        Serial.println(F("  STATUS            Show cached HCR status  [HCR:...]"));
        Serial.println(F("  REFRESH           Poll the HCR immediately"));
        Serial.println(F("  GET,<field>       Show one cached value (EMOTION,H|S|M|C /"));
        Serial.println(F("                      DURATION / OVERRIDE / MUSE / WAVCOUNT /"));
        Serial.println(F("                      PLAYING,V|A|B / VOL,V|A|B). VOL also"));
        Serial.println(F("                      asks the HCR; the answer shows next time"));
        Serial.println(F("\nRuntime Actions (use ;H,...):"));
        Serial.println(F("  ;H,STIM,e,lvl       Stimulate  e=H|S|M|C  lvl=MOD|STRONG"));
        Serial.println(F("  ;H,TRIGGER,e,lvl    Trigger (same payload as STIM)"));
        Serial.println(F("  ;H,OVERLOAD         Overload vocalization"));
        Serial.println(F("  ;H,SETEMOTION,e,0-100  Set an emotion level directly"));
        Serial.println(F("  ;H,RESETEMOTIONS    Reset all emotions to 0"));
        Serial.println(F("  ;H,OVERRIDE,0|1     Personality-chip emotion override"));
        Serial.println(F("  ;H,STOPEMOTE[,NOW|GRACEFUL]"));
        Serial.println(F("                      Stop the current emote. NOW (default)"));
        Serial.println(F("                      cuts it off; GRACEFUL lets the vocalizer"));
        Serial.println(F("                      finish the sound it is making"));
        Serial.println(F("  ;H,MUSE             Trigger one muse"));
        Serial.println(F("  ;H,MUSE,0|1|TOGGLE  Disable / enable / toggle muse"));
        Serial.println(F("  ;H,MUSE,GAP,min,max Set muse gap range (seconds)"));
        Serial.println(F("  ;H,PLAY,A|B,0-9999  Play a WAV on channel A/B"));
        Serial.println(F("  ;H,PLAY,A|B,file,FADEIN,sec  Play, ramp 0->current vol"));
        Serial.println(F("  ;H,STOPWAV,A|B      Stop WAV on a channel"));
        Serial.println(F("  ;H,VOL[,V|A|B],0-100  Set volume (no channel = all V/A/B)"));
        Serial.println(F("  ;H,VOLUP[,V|A|B][,step]  Volume up (no channel = all; step default 5)"));
        Serial.println(F("  ;H,VOLDN[,V|A|B][,step]  Volume down (no channel = all; step default 5)"));
        Serial.println(F("  ;H,FADEIN,A|B,sec   Ramp 0 -> current volume"));
        Serial.println(F("  ;H,FADEOUT,A|B,sec  Ramp -> 0, StopWAV, restore vol"));
        Serial.println(F("  ;H,STOP[,NOW|GRACEFUL]"));
        Serial.println(F("                      Stop all audio and emotes. GRACEFUL"));
        Serial.println(F("                      applies to the vocalizer only — WAV"));
        Serial.println(F("                      channels always stop at once"));
        Serial.println(F("  ;H,FN,fn,chan,track Numeric dispatch (RC fn/chan/track)"));
        Serial.println(F("                      fn 20 = graceful emote stop, 21 = graceful"));
        Serial.println(F("                      stop all (same bytes as ;H,STOP*,GRACEFUL)"));
        Serial.println(F("  ;H,RAW,<string>     Send a literal HCR string verbatim"));
        Serial.println(F("\nExamples:"));
        Serial.println(F("  ?HCR,PORT,S1:9600             - HCR on S1 at 9600 baud"));
        Serial.println(F("  ?HCR,POLL,5                   - Poll status every 5 s"));
        Serial.println(F("  ?HCR,STATUS                   - Show cached status"));
        Serial.println(F("  ;H,STIM,H,STRONG              - Strong happy stimulation"));
        Serial.println(F("  ;H,PLAY,A,42                  - Play WAV 42 on channel A"));
        Serial.println(F("  ;H,VOL,V,80                   - Vocalizer volume 80"));
        Serial.println(F("  ;H,RAW,<MM,QM>                - Literal HCR string"));
        Serial.println(F("  ;W2,;H,STIM,M,STRONG          - Stimulate WCB2's HCR"));
        Serial.println(F("\nNotes:"));
        Serial.println(F("  - HCR status is poll-based; STATUS reflects the last poll"));
        Serial.println(F("      (age = s since the HCR last answered, -1 = never; rx = replies;"));
        Serial.println(F("       vage = s since it last confirmed all of vV/vA/vB, -1 = not yet)"));
        Serial.println(F("  - A volume set via ;H,VOL/VOLUP/VOLDN/fades/FN shows in STATUS at"));
        Serial.println(F("      once; the next poll after it replaces it with the HCR's report"));
        Serial.println(F("  - Port is dedicated: broadcast I/O is disabled on it"));
        Serial.println(F("  - Debug: ?DEBUG,HCR,ON (or dhcron) logs commands sent +"));
        Serial.println(F("      every reply as [HCR-RX]; ?DEBUG,HCR,OFF / dhcroff"));
        Serial.println(F("  - Saved to NVS and persists across reboots"));

    // ================================================================
    } else if (c == "WLED") {
        Serial.println(F("---------------------------------------------------"));
        Serial.println(F("\nUsage: ?WLED,<command>[,options]   (config/query)"));
        Serial.println(F("       ;L,<command>[,options]     (runtime actions)"));
        Serial.println(F("\nDescription:"));
        Serial.println(F("  Drive a stock WLED node over a reserved serial port using"));
        Serial.println(F("  WLED's JSON API (no custom WLED firmware). Author the looks"));
        Serial.println(F("  in WLED's web UI; the WCB fires presets / power / brightness."));
        Serial.println(F("  Wire WCB TX -> WLED RX + ground; WLED listens at 115200 on a"));
        Serial.println(F("  build whose LED pin is NOT on GPIO1/3 (GPIO2/16 is fine)."));
        Serial.println(F("\nConfiguration Commands (?WLED,...):"));
        Serial.println(F("  <id>:W<wcb>S<port>:<baud>  Configure WLED <id> on a board + port"));
        Serial.println(F("                      use a HARDWARE port (S1/S2) at 115200"));
        Serial.println(F("  CLEAR             Release all WLED slots"));
        Serial.println(F("  CLEAR,<id>        Release just WLED <id>"));
        Serial.println(F("  LIST              Show WLED configuration and link status"));
        Serial.println(F("  STATUS            Show status  [WLED:...]"));
        Serial.println(F("\nRuntime Actions — ID-ADDRESSED (;L<id>,...):"));
        Serial.println(F("  ;L<id>,ON / OFF / TOGGLE    Power"));
        Serial.println(F("  ;L<id>,BRI,0-255    Master brightness"));
        Serial.println(F("  ;L<id>,PS,<n>       Recall preset n (primary workflow)"));
        Serial.println(F("  ;L<id>,COL,RRGGBB   Solid colour (RRGGBBWW for RGBW)"));
        Serial.println(F("  ;L<id>,FX,<n>[,sx,ix]  Effect by index (+ speed/intensity)"));
        Serial.println(F("  ;L<id>,PAL,<n>      Palette by index"));
        Serial.println(F("  ;L<id>,JSON,{...}   Raw /json/state passthrough (escape hatch)"));
        Serial.println(F("\nExamples:"));
        Serial.println(F("  ?WLED,1:W3S2:115200           - WLED id 1 on WCB3 port S2"));
        Serial.println(F("  ;L1,PS,3                      - Fire preset 3 on WLED id 1"));
        Serial.println(F("  ;L1,COL,FF0000                - Solid red on WLED id 1"));
        Serial.println(F("  ;W4,;L1,PS,2                  - Preset 2 on WCB4's WLED"));
        Serial.println(F("\nNotes:"));
        Serial.println(F("  - Fire-and-forget: the WCB does not read WLED back"));
        Serial.println(F("  - One slot per WLED ID; ;L<id> routes to whichever board hosts it"));
        Serial.println(F("  - Port is dedicated: broadcast I/O is disabled on it"));
        Serial.println(F("  - Saved to NVS and persists across reboots"));

    // ================================================================
    } else if (c == "MGMT") {
        Serial.println(F("---------------------------------------------------"));
        Serial.println(F("---------------------------------------------------"));
        Serial.println(F("\nUsage: ?MGMT,<verb>,<target WCB>[,...]"));
        Serial.println(F("\nDescription:"));
        Serial.println(F("  Relays a management request to another board over ESP-NOW. THIS"));
        Serial.println(F("  board is the relay: the target answers over the mesh and the reply"));
        Serial.println(F("  prints here as one [MGMT:<tag>,<n>] line. Normally driven by the"));
        Serial.println(F("  Wizard, not by hand."));
        Serial.println(F("\nCommands:"));
        Serial.println(F("  PULL,<n>          WCB n's config:  [MGMT:CONFIG,n]<config>"));
        Serial.println(F("                      Over 2912 characters it cannot come back this"));
        Serial.println(F("                      way: [MGMT:CFGERR,n]NOPARTS,..."));
        Serial.println(F("  PULL,<n>,P        The same, and a config over 2912 characters comes"));
        Serial.println(F("                      back in parts, one line each:"));
        Serial.println(F("                      [MGMT:CFGPART,n]P<id>,<k>,<K>:<data>~"));
        Serial.println(F("                      The <data> of parts 1..K of one <id>, joined,"));
        Serial.println(F("                      is the config"));
        Serial.println(F("  STATS,<n>         WCB n's ?STATS:  [MGMT:STATS,n]"));
        Serial.println(F("  SEQ,<n>           WCB n's sequence names:  [MGMT:SEQ,n]"));
        Serial.println(F("  SEQGET,<n>,<key>  One sequence from WCB n:  [MGMT:SEQVAL,n]"));
        Serial.println(F("  ETM,CHAR,<n>      ETM characterization on WCB n:  [MGMT:ETM,n]"));
        Serial.println(F("  FRAG,...          One fragment of a Wizard config push"));
        Serial.println(F("\nPull errors ([MGMT:CFGERR,n]<CODE>,<detail>):"));
        Serial.println(F("  NOMEM             The target was out of memory - try again"));
        Serial.println(F("  CHANGED           The config changed while it was sent - try again"));
        Serial.println(F("  NOPARTS           Over 2912 characters and no request for parts"));
        Serial.println(F("                      arrived (every ,P copy lost, or an older"));
        Serial.println(F("                      Wizard/relay): ask again with ,P"));
        Serial.println(F("  TOOBIG            Too large even in parts: ?backup over USB"));
        Serial.println(F("\nExamples:"));
        Serial.println(F("  ?MGMT,PULL,3         - Config of WCB3"));
        Serial.println(F("  ?MGMT,PULL,3,P       - Config of WCB3, in parts if it is large"));
        Serial.println(F("  ?MGMT,SEQGET,3,wave  - Sequence 'wave' from WCB3"));
        Serial.println(F("\nNotes:"));
        Serial.println(F("  - A config pull carries the mesh password and any WiFi passphrase"));
        Serial.println(F("  - Older relays treat PULL,<n>,P as PULL,<n>"));
        Serial.println(F("  - Test knobs, on the TARGET: ?DEBUG,PULLPART and ?DEBUG,PULLFAULT"));

    // ================================================================
    } else if (c == "OTA" || c == "OTALOCAL") {
        Serial.println(F("---------------------------------------------------"));
        Serial.println(F("---------------------------------------------------"));
        Serial.println(F("\nFirmware Update (OTA)"));
        Serial.println(F("\nDescription:"));
        Serial.println(F("  Writes a new firmware image to this board's INACTIVE OTA slot"));
        Serial.println(F("  and reboots into it. Two transports share the same write core:"));
        Serial.println(F("  ?OTALOCAL over direct USB, and ?OTA which RELAYS a stream over"));
        Serial.println(F("  ESP-NOW to another WCB. Normally driven by the Wizard, not by"));
        Serial.println(F("  hand — the commands below are the wire protocol it speaks."));
        Serial.println(F("\nLocal (this board, over USB) — ?OTALOCAL,...:"));
        Serial.println(F("  STATUS                    Show OTA slot / session state"));
        Serial.println(F("  BAUD,<rate>               Raise the USB baud for the transfer"));
        Serial.println(F("  BEGIN,<imageSize>,<fam>   Start a session (fam: 0=ESP32 1=ESP32-S3)"));
        Serial.println(F("  DATA,<offset>,<base64>    Write one chunk"));
        Serial.println(F("  END                       Verify, set boot partition, reboot"));
        Serial.println(F("  ABORT                     Cancel and roll back the session"));
        Serial.println(F("\nRelay (drive a REMOTE board over the mesh) — ?OTA,...:"));
        Serial.println(F("  BEGIN,<target>,<session>,<imageSize>,<fam>  Start on target WCB"));
        Serial.println(F("  DATA,<target>,<session>,<offset>,<base64>   Forward one chunk"));
        Serial.println(F("  END,<target>,<session>  /  ABORT,<target>,<session>"));
        Serial.println(F("\nNotes:"));
        Serial.println(F("  - The image is written to the inactive slot; a failed or aborted"));
        Serial.println(F("    session leaves the RUNNING firmware untouched."));
        Serial.println(F("  - Requires the min_spiffs partition scheme (2 x ~1.9MB OTA slots)."));
        Serial.println(F("  - Each chunk is acknowledged with [OTA:ACK,...] for flow control."));
        Serial.println(F("  - RC/telemetry passthrough is paused while chunks are flowing so"));
        Serial.println(F("    it cannot crowd out those ACK lines."));
        Serial.println(F("  - Settings in NVS are preserved across an OTA."));

    // ================================================================
    } else if (c == "VAR") {
        Serial.println(F("---------------------------------------------------"));
        Serial.println(F("---------------------------------------------------"));
        Serial.println(F("\nUser Variables + Conditional Execution"));
        Serial.println(F("\nDescription:"));
        Serial.println(F("  Named, persistent integer variables (boolean = 0/non-zero),"));
        Serial.println(F("  usable in stored sequences to gate commands. Up to 100 vars."));
        Serial.println(F("  Names: 1-15 chars, case-sensitive, letters/digits/underscore."));
        Serial.println(F("  Undefined variables read as 0. Per-board (each board's own NVS)."));
        Serial.println(F("\nSet / mutate (runtime) -- ;V (volatile) / ;VP (persistent):"));
        Serial.println(F("  ;V,<name>,<int>       Set (VOLATILE: RAM-only, no flash wear)"));
        Serial.println(F("  ;VP,<name>,<int>      Set + persist to NVS (survives reboot)"));
        Serial.println(F("  ;V,<name>,true|false  Set to 1 / 0"));
        Serial.println(F("  ;V,<name>,TOGGLE      Flip: non-zero -> 0, 0 -> 1"));
        Serial.println(F("  ;V,<name>,INC[,n]     Add n (default 1)"));
        Serial.println(F("  ;V,<name>,DEC[,n]     Subtract n (default 1)"));
        Serial.println(F("  (;VP takes the same verbs. Default is VOLATILE; ;VP promotes"));
        Serial.println(F("   a volatile var, ;V never demotes a persistent one.)"));
        Serial.println(F("\nManage -- ?VAR:"));
        Serial.println(F("  ?VAR,LIST             List all variables and values"));
        Serial.println(F("  ?VAR,SET,<name>,<v>   Create/update a variable (absolute value)"));
        Serial.println(F("  ?VAR,GET,<name>       Show one variable"));
        Serial.println(F("  ?VAR,CLEAR,<name>     Delete one variable"));
        Serial.println(F("  ?VAR,CLEAR,ALL        Delete all variables"));
        Serial.println(F("  (?VAR,SET creates/updates as PERSISTENT, same as ;VP)"));
        Serial.println(F("\nConditional -- IF (gates the NEXT delimited command):"));
        Serial.println(F("  IF,<name><op><int>             op = =  !=  <  >  <=  >="));
        Serial.println(F("  IF,<cond>,AND|OR,<cond>,...    left-to-right, no parentheses"));
        Serial.println(F("\nExamples:"));
        Serial.println(F("  ;V,domeanimations,0            - disable a flag (volatile)"));
        Serial.println(F("  ;V,volume,INC,5                - volume += 5 (volatile)"));
        Serial.println(F("  ;VP,startupmode,2              - persist a setting to NVS"));
        Serial.println(F("  IF,domeanimations=1^;M11       - run M1 sub1 only if flag is 1"));
        Serial.println(F("  IF,mode>2,AND,armed=1^;M13     - compound condition"));
        Serial.println(F("  IF,flag=1^;t500^;M2,goHome     - if flag, wait 500ms, then home"));
        Serial.println(F("\nNotes:"));
        Serial.println(F("  - IF gates its next command; ;t delays between them are fine"));
        Serial.println(F("    (a false IF skips the delay AND the command)."));
        Serial.println(F("  - Evaluated when the sequence is invoked, not after delays."));
        Serial.println(F("  - Set & test in SEPARATE sequences: ;V,x,1^IF,x=1^cmd reads"));
        Serial.println(F("    the OLD value (the ;V hasn't run yet at evaluate time)."));
        Serial.println(F("  - Chained IFs AND together (IF,a=1^IF,b=2^cmd); compound IF is clearer."));
        Serial.println(F("  - IF can't ride inside ;t or ;w payloads — gate the whole"));
        Serial.println(F("    token instead: IF,cond^;t500^cmd / IF,cond^;w2,cmd"));
        Serial.println(F("  - Only PERSISTENT vars (;VP / ?VAR,SET) are saved to NVS &"));
        Serial.println(F("    in ?backup. Volatile (;V) vars are RAM-only -- use them for"));
        Serial.println(F("    fast-changing values so you don't wear out the flash."));

    // ================================================================
    } else if (c == "SEQ") {
        Serial.println(F("---------------------------------------------------"));
        Serial.println(F("---------------------------------------------------"));
        Serial.println(F("\nUsage: ?SEQ,<command>[,key[,value]]"));
        Serial.println(F("\nDescription:"));
        Serial.println(F("  Stores and manages named command sequences in the board's sequence"));
        Serial.println(F("  store: a small file system in flash, apart from the settings (NVS)."));
        Serial.println(F("  A sequence is a string of chained commands saved under a short"));
        Serial.println(F("  key name. Once saved, sequences can be triggered from any serial"));
        Serial.println(F("  port or ESP-NOW using the recall command. Sequences can contain"));
        Serial.println(F("  timer commands for choreographed multi-step animations."));
        Serial.println(F("\nCommands:"));
        Serial.println(F("  SAVE,key,value    Save a command sequence under key name"));
        Serial.println(F("                      key: short name, no spaces"));
        Serial.println(F("                      value: command string (can include delimiters)"));
        Serial.println(F("  CLEAR,key         Delete a stored sequence by key name"));
        Serial.println(F("  CLEAR,ALL         Delete all stored sequences"));
        Serial.println(F("  LIST              List all stored sequences and their contents"));
        Serial.println(F("\nTo run a stored sequence:"));
        Serial.println(F("  ;Ckey  (or ;SEQkey)  Run sequence 'key' MESH-WIDE: every board"));
        Serial.println(F("                       that has 'key' runs its own copy once, no"));
        Serial.println(F("                       matter which board you type it on"));
        Serial.println(F("  ;Ckey,L (or ;SEQkey,L)  Run 'key' on THIS board ONLY (no mesh)"));
        Serial.println(F("\nExamples:"));
        Serial.println(F("  ?SEQ,SAVE,wave,CMD1^CMD2^CMD3      - Save sequence 'wave'"));
        Serial.println(F("  ?SEQ,SAVE,spin,;T500,SPIN^;T1000,STOP  - Timed sequence"));
        Serial.println(F("  ;Cwave                             - Run 'wave' everywhere it exists"));
        Serial.println(F("  ;Cwave,L                           - Run 'wave' on this board only"));
        Serial.println(F("  ?SEQ,LIST                          - Show all sequences"));
        Serial.println(F("  ?SEQ,NAMES                         - Names only, one parseable line"));
        Serial.println(F("  ?SEQ,GET,wave                      - One sequence: key,status,value"));
        Serial.println(F("  ?MGMT,SEQ,3                        - Names from WCB3 over the mesh"));
        Serial.println(F("  ?MGMT,SEQGET,3,wave                - One sequence from WCB3"));
        Serial.println(F("  ?SEQ,CLEAR,wave                    - Delete 'wave'"));
        Serial.println(F("  ?SEQ,CLEAR,ALL                     - Delete everything"));
        Serial.println(F("\nNotes:"));
        Serial.println(F("  - Key names are case sensitive"));
        Serial.println(F("  - A key is at most 15 characters; a sequence at most 3999"));
        Serial.println(F("  - The store holds 32 KB of sequences - hundreds; ?NVS shows how full"));
        Serial.println(F("  - A top-level ;Ckey fires on ALL boards that have 'key' (once each)."));
        Serial.println(F("    Same name on several boards = they all trigger together."));
        Serial.println(F("  - Add ,L to fire local-only: ;Ckey,L runs just this board."));
        Serial.println(F("  - Sequences can still call other sequences with ;Ckey; a NESTED ;C"));
        Serial.println(F("    inside a running sequence stays LOCAL (it does not re-fan out)."));
        Serial.println(F("  - A sequence may call the same sub-sequence any number of times, but never"));
        Serial.println(F("    itself (directly or in a ring): that recall is refused. Max 8 levels deep."));
        Serial.println(F("  - A called sequence containing ;T replaces the caller's remaining timed steps."));
        Serial.println(F("  - Timer commands (;T) create non-blocking delays between steps"));
        Serial.println(F("  - A ;T delay over 30 minutes is capped at 1800000 ms (and says so); a"));
        Serial.println(F("    negative one (;T-500) refuses the whole chain - nothing in it runs"));
        Serial.println(F("  - Saved to NVS and persists across reboots"));
        Serial.println(F("\nLegacy commands:"));
        Serial.println(F("  ?CSkey,value   - Save sequence  (e.g. ?CSwave,CMD1^CMD2)"));
        Serial.println(F("  ?CEkey         - Clear sequence (e.g. ?CEwave)"));
        Serial.println(F("  ?CCLEAR        - Clear all sequences"));

    // ================================================================
    } else if (c == "STATS") {
        Serial.println(F("---------------------------------------------------"));
        Serial.println(F("---------------------------------------------------"));
        Serial.println(F("\nUsage: ?STATS  /  ?STATS,RESET  /  ?STATS,RPT,..."));
        Serial.println(F("\nDescription:"));
        Serial.println(F("  Displays ESP-NOW transmission statistics since last reboot."));
        Serial.println(F("  Shows counts for command messages, PWM passthrough, and raw"));
        Serial.println(F("  Kyber data separately. When ETM is enabled, also shows per-board"));
        Serial.println(F("  delivery confirmation, retry counts, and failure rates."));
        Serial.println(F("\nCommands:"));
        Serial.println(F("  (none)            Display all current statistics"));
        Serial.println(F("  RESET             Reset all counters to zero"));
        Serial.println(F("  RPT,<fields>      Store a report from ANOTHER node (see below)"));
        Serial.println(F("\nOutput includes:"));
        Serial.println(F("  - Unicast command attempts, delivered, failed"));
        Serial.println(F("  - Delivery success rate percentage"));
        Serial.println(F("  - PWM passthrough message counts (if used)"));
        Serial.println(F("  - Raw Kyber data counts (if used)"));
        Serial.println(F("  - Per-board ETM stats when ETM is enabled"));
        Serial.println(F("  - Board online/offline status with last seen time"));
        Serial.println(F("  - Rows other nodes reported about THEMSELVES (?STATS,RPT)"));
        Serial.println(F("\nExamples:"));
        Serial.println(F("  ?STATS             - Show statistics"));
        Serial.println(F("  ?STATS,RESET       - Reset all counters"));
        Serial.println(F("\nReceiving reports from other nodes:"));
        Serial.println(F("  ?STATS,RPT,<from>,<sent>,<ackd>,<retries>,<failed>,<unguaranteed>,<bcast>,<recv>"));
        Serial.println(F("  A node (e.g. NaviCore) sends this to report ITS OWN counters."));
        Serial.println(F("  Stored here and listed under 'Reported by Other Nodes'."));
        Serial.println(F("  <from> is in the payload because a '?' command carries no sender id."));
        Serial.println(F("  All 8 fields are required — a short report is dropped, not stored."));
        Serial.println(F("\nNotes:"));
        Serial.println(F("  - Statistics reset automatically on reboot"));
        Serial.println(F("  - Reported rows are RAM-only; ?STATS,RESET clears them too"));
        Serial.println(F("  - A '?' command is handled locally: a report is never re-broadcast"));
        Serial.println(F("    and never written to this board's serial ports"));
        Serial.println(F("  - Use ?DEBUG,ETM,ON for detailed per-packet logging"));
        Serial.println(F("\nLegacy commands:"));
        Serial.println(F("  ?STATS         - Show stats"));
        Serial.println(F("  ?STATSRESET    - Reset stats"));

    // ================================================================
    } else if (c == "WIFI") {
        Serial.println(F("---------------------------------------------------"));
        Serial.println(F("---------------------------------------------------"));
        Serial.println(F("\nUsage: ?WIFI[,<mode>[,<ssid>,<password>]]"));
        Serial.println(F("\nDescription:"));
        Serial.println(F("  Give this board an IP presence so a phone or desktop app can"));
        Serial.println(F("  manage the mesh with no USB cable. OFF by default."));
        Serial.println(F("\nModes:"));
        Serial.println(F("  ?WIFI                    Show status (mode, IP, channel, free heap)"));
        Serial.println(F("  ?WIFI,OFF                ESP-NOW only (the default)"));
        Serial.println(F("  ?WIFI,AP,<ssid>,<pass>   Host an access point"));
        Serial.println(F("  ?WIFI,JOIN,<ssid>,<pass> Join an existing one (e.g. a NaviCore's)"));
        Serial.println(F("\nTHE CHANNEL IS NOT SEPARATELY CONFIGURABLE:"));
        Serial.println(F("  The ESP32 has ONE radio, so WiFi and ESP-NOW share a channel."));
        Serial.println(F("  It always follows ?WCBCH. A WiFi channel that disagreed with the"));
        Serial.println(F("  mesh would be a SILENT blackout — every packet dropped, nothing"));
        Serial.println(F("  logged on the other boards — so it is not offered as a choice."));
        Serial.println(F("  In JOIN mode the channel is VERIFIED after associating; if the"));
        Serial.println(F("  AP put us elsewhere the board disconnects rather than go deaf."));
        Serial.println(F("\nNotes:"));
        Serial.println(F("  - Settings apply on the NEXT REBOOT, like ?WCBCH."));
        Serial.println(F("  - The AP password is MANDATORY (8+ chars). This interface accepts"));
        Serial.println(F("    commands for the whole mesh with no credential of its own, so an"));
        Serial.println(F("    open AP would hand the droid to anyone in range."));
        Serial.println(F("  - Default AP SSID is WCB-<alias> (or WCB-<number> with no alias)."));
        Serial.println(F("  - JOIN retries forever and never falls back to hosting — a board"));
        Serial.println(F("    that quietly became an AP is a surprise nobody wants."));
        Serial.println(F("\nExamples:"));
        Serial.println(F("  ?WIFI,AP,R2-Dome,astromech1"));
        Serial.println(F("  ?WIFI,JOIN,NaviCore-20,mypassword"));
        Serial.println(F("  ?WIFI,OFF"));

    // ================================================================
    } else if (c == "WDP") {
        Serial.println(F("---------------------------------------------------"));
        Serial.println(F("---------------------------------------------------"));
        Serial.println(F("\nUsage: ?WDP[,<subcommand>]"));
        Serial.println(F("\nDescription:"));
        Serial.println(F("  Wireless Discovery Protocol — \"CDP/LLDP for WCBs.\" Every board"));
        Serial.println(F("  advertises its own identity + capabilities on the mesh and learns"));
        Serial.println(F("  its neighbors into a live table. Drives auto-config: controller"));
        Serial.println(F("  auto-adopt, Maestro-remote auto-enable, and dynamic PEER MEMBERSHIP"));
        Serial.println(F("  (auto-join) — boards heard on the mesh are added as peers and"));
        Serial.println(F("  remembered across reboots. Requires ETM enabled."));
        Serial.println(F("\nView:"));
        Serial.println(F("  ?WDP  /  ?WDP,LIST   Neighbor table (all boards + client devices)"));
        Serial.println(F("  ?WDP,<n>             Detail for one neighbor (caps, ports, Maestros)"));
        Serial.println(F("  ?WDP,STATUS          One-line status (en, autojoin, peers)"));
        Serial.println(F("  ?WDP,DUMP            Machine-readable dump (for the config tool)"));
        Serial.println(F("  ?WDP,DA              Serial-attached (@WDP1) devices per port"));
        Serial.println(F("\nSerial-attached devices (kept until forgotten; shared with every board):"));
        Serial.println(F("  ?WDP,DA,FORGET,S<n>           Forget every device on port S<n>"));
        Serial.println(F("  ?WDP,DA,FORGET,S<n>,<type>    Forget one device (type as listed, any case)"));
        Serial.println(F("  ?WDP,DA,CLEAR                 Forget all of them"));
        Serial.println(F("\nEnable / discovery:"));
        Serial.println(F("  ?WDP,ON  /  ?WDP,OFF          Enable/disable WDP (persisted; default ON)"));
        Serial.println(F("  ?WDP,AUTOJOIN                 Show auto-join state"));
        Serial.println(F("  ?WDP,AUTOJOIN,ON | ,OFF       Learn heard WCBs as peers (default ON)"));
        Serial.println(F("\nPeer membership:"));
        Serial.println(F("  ?WDP,ADD,<id>        Manually add WCB <id> as a (persisted) peer"));
        Serial.println(F("  ?WDP,FORGET,<id>     Drop one learned peer (frees its slot + NVS)"));
        Serial.println(F("  ?WDP,CLEAR           Drop ALL learned peers + wipe the neighbor table"));
        Serial.println(F("\nNotes:"));
        Serial.println(F("  - WCBQ is the FLOOR; auto-join extends membership above it"));
        Serial.println(F("  - Learned peers are permanent until FORGET/CLEAR (not aged out)"));
        Serial.println(F("  - See PEERSLIVE / the Wizard mesh panel for the live peer count"));

    // ================================================================
    } else if (c == "DELIM") {
        Serial.println(F("---------------------------------------------------"));
        Serial.println(F("\nDescription:"));
        Serial.println(F("  Sets the command delimiter character used to chain multiple"));
        Serial.println(F("  commands in a single transmission. The delimiter separates"));
        Serial.println(F("  individual commands within a chained command string."));
        Serial.println(F("\nParameters:"));
        Serial.println(F("  character     Single character to use as delimiter"));
        Serial.println(F("                  Default: ^"));
        Serial.println(F("\nExamples:"));
        Serial.println(F("  ?DELIM,^       - Set delimiter to ^ (default)"));
        Serial.println(F("  ?DELIM,|       - Set delimiter to |"));
        Serial.println(F("\nNotes:"));
        Serial.println(F("  - ALL boards in the system should use the same delimiter"));
        Serial.println(F("  - Choose a character not used in your commands"));
        Serial.println(F("  - Saved to NVS and persists across reboots"));
        Serial.println(F("  - Takes effect immediately without reboot"));
        Serial.println(F("\nLegacy commands:"));
        Serial.println(F("  ?Dx   (e.g. ?D^)"));

    // ================================================================
    } else if (c == "FUNCCHAR") {
        Serial.println(F("---------------------------------------------------"));
        Serial.println(F("---------------------------------------------------"));
        Serial.println(F("\nUsage: ?FUNCCHAR,<character>"));
        Serial.println(F("\nDescription:"));
        Serial.println(F("  Sets the local function identifier character. This is the"));
        Serial.println(F("  prefix character that tells the WCB a command is addressed"));
        Serial.println(F("  to this board's local functions rather than being broadcast."));
        Serial.println(F("  All WCB configuration commands start with this character."));
        Serial.println(F("\nParameters:"));
        Serial.println(F("  character     Single character, Default: ?"));
        Serial.println(F("\nExamples:"));
        Serial.println(F("  ?FUNCCHAR,?    - Set to ? (default)"));
        Serial.println(F("  ?FUNCCHAR,/    - Set to /"));
        Serial.println(F("\nNotes:"));
        Serial.println(F("  - Must not conflict with CommandCharacter (;)"));
        Serial.println(F("  - Saved to NVS and persists across reboots"));
        Serial.println(F("  - Takes effect immediately"));
        Serial.println(F("\nLegacy commands:"));
        Serial.println(F("  ?LFx   (e.g. ?LF?)"));

    // ================================================================
    } else if (c == "CMDCHAR") {
        Serial.println(F("---------------------------------------------------"));
        Serial.println(F("---------------------------------------------------"));
        Serial.println(F("\nUsage: ?CMDCHAR,<character>"));
        Serial.println(F("\nDescription:"));
        Serial.println(F("  Sets the command character prefix. This is the prefix used"));
        Serial.println(F("  for serial routing, WCB targeting, Maestro, stored sequence"));
        Serial.println(F("  recall, and PWM output commands. Commands starting with this"));
        Serial.println(F("  character are processed locally by the command parser."));
        Serial.println(F("\nParameters:"));
        Serial.println(F("  character     Single character, Default: ;"));
        Serial.println(F("\nCommand character prefixes:"));
        Serial.println(F("  ;Sx,msg       Send msg to serial port x"));
        Serial.println(F("  ;Wx,msg       Send msg to WCB x via ESP-NOW"));
        Serial.println(F("  ;Ckey         Run stored sequence 'key'"));
        Serial.println(F("  ;M<id><seq>   Trigger Maestro subroutine (;M11, or ;M1,1)"));
        Serial.println(F("  ;M<dev>,verb  Maestro servo verb (see ?MAESTRO for the list)"));
        Serial.println(F("  ;Pxnnnn       Output PWM pulse on port x (no comma, e.g. ;P11500)"));
        Serial.println(F("\nExamples:"));
        Serial.println(F("  ?CMDCHAR,;    - Set to ; (default)"));
        Serial.println(F("  ?CMDCHAR,:    - Set to :"));
        Serial.println(F("\nNotes:"));
        Serial.println(F("  - Must not conflict with LocalFunctionIdentifier (?)"));
        Serial.println(F("  - Saved to NVS and persists across reboots"));
        Serial.println(F("\nLegacy commands:"));
        Serial.println(F("  ?CCx   (e.g. ?CC;)"));

    // ================================================================
    } else if (c == "NVS") {
        Serial.println(F("---------------------------------------------------"));
        Serial.println(F("---------------------------------------------------"));
        Serial.println(F("\nUsage: ?NVS"));
        Serial.println(F("\nDescription:"));
        Serial.println(F("  Shows how full the settings storage (NVS) is and which namespace"));
        Serial.println(F("  uses what. Read-only. A full store refuses long sequences and the"));
        Serial.println(F("  variable table long before anything else says why."));
        Serial.println(F("\nOutput:"));
        Serial.println(F("  NVS: used=U free=F available=A total=T namespaces=N (P% used)"));
        Serial.println(F("    one line per namespace: its name and the entries it uses"));
        Serial.println(F("  Entries are 32-byte slots; a string or blob takes one per 32 bytes."));
        Serial.println(F("  'available' is what new data can use (free minus the GC reserve)."));

    // ================================================================
    } else if (c == "ERASE") {
        Serial.println(F("---------------------------------------------------"));
        Serial.println(F("---------------------------------------------------"));
        Serial.println(F("\nUsage: ?ERASE,NVS"));
        Serial.println(F("\nDescription:"));
        Serial.println(F("  Erases ALL settings stored in NVS flash memory and reboots."));
        Serial.println(F("  This returns the board to factory default settings. Use this"));
        Serial.println(F("  when troubleshooting configuration issues or preparing a board"));
        Serial.println(F("  for a fresh setup. Use ?BACKUP first to save your configuration."));
        Serial.println(F("\nWhat gets erased:"));
        Serial.println(F("  - WCB number and quantity"));
        Serial.println(F("  - MAC octets"));
        Serial.println(F("  - ESP-NOW password"));
        Serial.println(F("  - Baud rates"));
        Serial.println(F("  - Broadcast settings"));
        Serial.println(F("  - Serial/PWM mappings"));
        Serial.println(F("  - Stored sequences"));
        Serial.println(F("  - Kyber settings"));
        Serial.println(F("  - Hardware version"));
        Serial.println(F("  - ETM settings"));
        Serial.println(F("  - Serial labels"));
        Serial.println(F("  - WiFi settings, including their passwords"));
        Serial.println(F("  - Learned peers and saved serial-attached devices"));
        Serial.println(F("  - Devices (Maestro, HCR, MP3, DFPlayer, WLED), variables"));
        Serial.println(F("  - Anything else in NVS, including older firmware's leftovers"));
        Serial.println(F("\nExamples:"));
        Serial.println(F("  ?ERASE,NVS     - Erase everything and reboot"));
        Serial.println(F("\nWARNING: This cannot be undone! Use ?BACKUP first!"));
        Serial.println(F("\nLegacy commands:"));
        Serial.println(F("  ?WCB_ERASE"));

    // ================================================================
    } else if (c == "LED") {
        Serial.println(F("---------------------------------------------------"));
        Serial.println(F("---------------------------------------------------"));
        Serial.println(F("\nUsage: ?LED,PIN,<gpio_number>"));
        Serial.println(F("       ?LED,PIN"));
        Serial.println(F("\nDescription:"));
        Serial.println(F("  Overrides the default NeoPixel status LED GPIO pin for this board."));
        Serial.println(F("  Useful when the onboard LED is on a non-default pin (e.g. custom"));
        Serial.println(F("  ESP32-S3 modules). The new pin is saved to NVS and persists across"));
        Serial.println(F("  reboots. If no pin argument is given, reports the current GPIO."));
        Serial.println(F("\nArguments:"));
        Serial.println(F("  <gpio_number>  GPIO pin number (0-48)"));
        Serial.println(F("\nExamples:"));
        Serial.println(F("  ?LED,PIN,38    - Set NeoPixel LED to GPIO38 (HW 3.x default)"));
        Serial.println(F("  ?LED,PIN,48    - Set NeoPixel LED to GPIO48"));
        Serial.println(F("  ?LED,PIN       - Print the current LED pin"));
        Serial.println(F("\nNotes:"));
        Serial.println(F("  - Primarily intended for HW 3.1/3.2 (DIY ESP32-S3) boards"));
        Serial.println(F("  - Reinitializes the NeoPixel immediately after saving"));
        Serial.println(F("  - Saved to NVS and persists across reboots"));
        Serial.println(F("  - Default is determined by the hardware version (?HW,x)"));

    // ================================================================
    } else if (c == "HW") {
        Serial.println(F("---------------------------------------------------"));
        Serial.println(F("---------------------------------------------------"));
        Serial.println(F("\nUsage: ?HW,<version>"));
        Serial.println(F("\nDescription:"));
        Serial.println(F("  Sets the hardware version of this WCB board. This must be set"));
        Serial.println(F("  correctly before any other configuration as it determines the"));
        Serial.println(F("  pin mapping for all serial ports and the status LED. Setting"));
        Serial.println(F("  the wrong version will result in incorrect pin assignments."));
        Serial.println(F("\nVersions:"));
        Serial.println(F("  1             Version 1.0 (LilyGo T7 V1.5 ESP32)"));
        Serial.println(F("  21            Version 2.1 (Custom PCB)"));
        Serial.println(F("  23            Version 2.3 (Custom PCB)"));
        Serial.println(F("  24            Version 2.4 (Custom PCB)"));
        Serial.println(F("  31            Version 3.1 (DIY Version)"));
        Serial.println(F("  32            Version 3.2 (DIY Version)"));
        Serial.println(F("\nExamples:"));
        Serial.println(F("  ?HW,31         - Set hardware version to 3.1"));
        Serial.println(F("  ?HW,24         - Set hardware version to 2.4"));
        Serial.println(F("\nNotes:"));
        Serial.println(F("  - This should be the FIRST command sent to a new board"));
        Serial.println(F("  - Reboot required after changing hardware version"));
        Serial.println(F("  - Saved to NVS and persists across reboots"));
        Serial.println(F("  - Use ?CONFIG to verify current hardware version"));
        Serial.println(F("\nLegacy commands:"));
        Serial.println(F("  ?HWx   (e.g. ?HW31)"));

    // ================================================================
    } else {
        // Top-level help menu
        Serial.println(F("\n============================================================"));
        Serial.println(F("  Wireless Communication Board (WCB) - Command Reference"));
        Serial.println(F("============================================================"));
        Serial.println(F("  Type ??           - Show this help menu"));
        Serial.println(F("  Type ?COMMAND?    - Quick syntax for a specific command"));
        Serial.println(F("                      (e.g. ?ETM? or ?MAP?)"));
        Serial.println(F("------------------------------------------------------------"));
        Serial.println(F("\n  INITIAL SETUP (do this first on a new board):"));
        Serial.println(F("    ?HW,x           Set hardware version (required before anything else)"));
        Serial.println(F("    ?LED,PIN,x      Set NeoPixel LED GPIO pin (HW 3.1/3.2, saved to NVS)"));
        Serial.println(F("    ?WCB,x          Set this board's number (1-20)"));
        Serial.println(F("    ?WCBQ,x         Set total boards in system"));
        Serial.println(F("    ?MAC,2,xx       Set 2nd MAC group octet (all boards must match)"));
        Serial.println(F("    ?MAC,3,xx       Set 3rd MAC group octet (all boards must match)"));
        Serial.println(F("    ?EPASS,pass     Set ESP-NOW password   (all boards must match)"));
        Serial.println(F("\n  SERIAL PORTS:"));
        Serial.println(F("    ?BAUD,Sx,rate   Set baud rate for serial port x"));
        Serial.println(F("    ?LABEL,Sx,text  Set a label for serial port x"));
        Serial.println(F("    ?BCAST,IN/OUT   Control broadcast input/output per port"));
        Serial.println(F("    ?MAP,SERIAL     Route serial data between ports/boards"));
        Serial.println(F("    ?MAP,PWM        Route RC PWM signals between ports/boards"));
        Serial.println(F("\n  DEVICES:"));
        Serial.println(F("    ?KYBER          Configure Kyber RC integration"));
        Serial.println(F("    ?MAESTRO        Configure Maestro servo controller(s)"));
        Serial.println(F("    ?MP3            Configure SparkFun MP3 Trigger v2.x"));
        Serial.println(F("    ?DFP            Configure DFPlayer Mini audio module"));
        Serial.println(F("    ?HCR            Configure Human-Cyborg Relations Vocalizer"));
        Serial.println(F("    ?WLED           Configure WLED serial control (;L<id> runtime)"));
        Serial.println(F("\n  NETWORK:"));
        Serial.println(F("    ?ETM            Ensured Transmission Mode (ACK/retry/heartbeat)"));
        Serial.println(F("    ?STATS          ESP-NOW transmission statistics"));
        Serial.println(F("    ?NVS            Settings storage use, by namespace (read-only)"));
        Serial.println(F("    ?WDP            Mesh discovery + neighbor table (auto-join peers)"));
        Serial.println(F("    ?MGMT           Relay a config pull/push to another board (Wizard)"));
        Serial.println(F("\n  FIRMWARE UPDATE:"));
        Serial.println(F("    ?OTA            Relay a firmware image to another WCB over the mesh"));
        Serial.println(F("    ?OTALOCAL       Update THIS board over USB"));
        Serial.println(F("\n  COMMAND SEQUENCES:"));
        Serial.println(F("    ?SEQ,SAVE       Save a named command sequence"));
        Serial.println(F("    ?SEQ,LIST       List all saved sequences"));
        Serial.println(F("    ?SEQ,NAMES      Sequence inventory, machine-readable"));
        Serial.println(F("    ;Ckey           Run a saved sequence"));
        Serial.println(F("\n  VARIABLES & LOGIC:"));
        Serial.println(F("    ?VAR            Manage variables (LIST/SET/GET/CLEAR)"));
        Serial.println(F("    ;V / ;VP        Set a variable (volatile / persistent)"));
        Serial.println(F("    IF,name=value   Gate the next command on variable state"));
        Serial.println(F("\n  ROUTING COMMANDS:"));
        Serial.println(F("    ;Sx,msg         Send msg to serial port x"));
        Serial.println(F("    ;Wx,msg         Send msg to WCB x via ESP-NOW"));
        Serial.println(F("    ;M<id><seq>     Trigger Maestro subroutine (;M11, or ;M1,1)"));
        Serial.println(F("    ;M<dev>,verb    Maestro servo verb (setTarget/goHome/... - ?MAESTRO)"));
        Serial.println(F("    ;A,PLAY,n       Play track n on this board's MP3 Trigger"));
        Serial.println(F("    ;Ckey           Run stored sequence named key"));
        Serial.println(F("    msg             Broadcast msg to all ports and ESP-NOW"));
        Serial.println(F("\n  DEBUG:"));
        Serial.println(F("    ?DEBUG,ON/OFF   Enable/disable debug output"));
        Serial.println(F("    ?DEBUG,ETM      ETM packet/ACK/retry debug"));
        Serial.println(F("    ?DEBUG,PWM      PWM passthrough debug"));
        Serial.println(F("    ?DEBUG,MAESTRO  Maestro/Pololu serial packet debug (hex)"));
        Serial.println(F("    ?DEBUG,RAW      Raw serial byte-level forwarding debug (hex)"));
        Serial.println(F("\n  SYSTEM:"));
        Serial.println(F("    ?config         Print full configuration"));
        Serial.println(F("    ?backup         Print backup/restore commands"));
        Serial.println(F("    ?DELIM,x        Set command delimiter character (default ^)"));
        Serial.println(F("    ?FUNCCHAR,x     Set local function identifier (default ?)"));
        Serial.println(F("    ?CMDCHAR,x      Set command character (default ;)"));
        Serial.println(F("    ?ERASE,NVS      Erase ALL settings - WARNING: irreversible!"));
        Serial.println(F("    ?reboot         Reboot this board"));
        Serial.println(F("============================================================\n"));
    }
}
