greghulette/Wireless_Communication_Board-WCB/Code/WCB/WCB_HCR.cpp

#include "WCB_RemoteTerm.h"  // Must be first — redirects Serial → WCBDebugSerial
#include "WCB_HCR.h"
#include "WCB_Storage.h"
#include <Preferences.h>
#include "src/EspSoftwareSerial/SoftwareSerial.h"   // vendored (tracker #78)
#include "src/HumanCyborgRelationsAPI/hcr.h"  // WCB-patched HCR, bundled in-sketch (no lib install)
#include <WcbCmd.h>          // shared ;H translator (HcrCodec) + fade (HcrFade) — same lib NaviCore runs

// ---- Externs provided by WCB.ino / WCB_Storage.cpp ---------------------
extern int           WCB_Number;
extern int           Default_WCB_Quantity;   // for validating a ?HCR,REMOTE,W<n> host
extern bool          debugEnabled;
extern bool          debugHCR;     // toggled via ?DEBUG,HCR,ON|OFF or dhcron/dhcroff
extern char          LocalFunctionIdentifier;
extern char          commandDelimiter;
extern unsigned long baudRates[5];
extern bool          serialBroadcastEnabled[5];
extern bool          blockBroadcastFrom[5];
extern Preferences   preferences;

// updateBaudRate / saveBroadcastSettingsToPreferences / saveBroadcastBlockSettings
// / saveSerialLabelToPreferences are declared by WCB_Storage.h (included above).
extern Stream      &getSerialStream(int port);
extern void         applyLiveBaud(int port, uint32_t baud);
extern bool         isSerialPortUsedForWLED(int port);  // WCB_WLED.cpp — for the port-conflict guard
extern bool         isSerialPortUsedForDFP(int port);   // WCB_DFP.cpp  — for the port-conflict guard
extern bool         isSerialPortUsedForMaestro(int port);  // WCB_Maestro.cpp — local Maestro slots only

// Serial3-5 are WcbSoftSerial instances defined in WCB.ino (library RX + RMT TX).
// Serial1/Serial2 are the ESP32 core HardwareSerial globals.
#include "WCB_SoftSerial.h"

// ---------------------------------------------------------------------------
//  WcbHCR — thin subclass of HCRVocalizer.
//
//  We deliberately do NOT call HCRVocalizer::begin(): on ESP32 it re-opens
//  the UART with DEFAULT pins (clobbering the WCB's custom S1/S2 pin map) and
//  prints "Begin _serial" junk to the HCR. The WCB already owns/initialises
//  the port (applyLiveBaud), so we only need to (a) initialise the library's
//  protected state — the active constructors leave refreshSpeed/emote_*/etc.
//  indeterminate — and (b) set the poll refresh rate. Both are reachable here
//  because those members are `protected` in hcr.h.
// ---------------------------------------------------------------------------
class WcbHCR final : public HCRVocalizer {   // final: deleted via WcbHCR* only
public:
  WcbHCR(HardwareSerial *s, int baud) : HCRVocalizer(s, baud)  { _init(); }
  WcbHCR(SoftwareSerial *s, int baud) : HCRVocalizer(s, baud)  { _init(); }

  // We do NOT use the library's built-in refreshSpeed auto-poll because it's
  // a uint16_t (ms) and overflows for any pollSec >= 66 s. processHCRTick()
  // schedules hcrPoll() on its own millis() timer instead, which natively
  // supports the documented 3-3600 s range.

  // A volume the WCB commands shows in STATUS/GET at once (Volume_* is otherwise
  // written only by a parsed HCR reply). A poll sent after the set replaces it with
  // what the HCR itself reports; replies already in flight can't (onFrame).
  void cacheVolume(int ch, int v) {
    if (ch == CH_V) Volume_V = v; else if (ch == CH_A) Volume_A = v; else if (ch == CH_B) Volume_B = v;
  }

protected:
  void onFrame(const char *frame, bool parsed) override;   // defined below the module globals

private:
  void _init() {
    refreshSpeed   = 0;
    emote_happy    = emote_sad = emote_mad = emote_scared = 0;
    state_override = state_musing = state_files = 0;
    state_duration = 0.0f;
    state_chv      = state_cha = state_chb = 0;
    Volume_V       = Volume_A = Volume_B = 0;
    cmdPos         = 0;
  }
};

// ---- Module globals -----------------------------------------------------
HCRConfig hcrConfig = {};

static WcbHCR  *_hcr     = nullptr;   // live instance (heap; rebuilt on port change)
static Stream  *_hcrPort = nullptr;   // concrete port stream — used by ;H,RAW
static unsigned long _hcrLastRxMs     = 0;  // millis() of the last parsed HCR frame (STATUS age); 0 = none
static uint32_t      _hcrRxFrames     = 0;  // parsed HCR frames since beginHCR() (STATUS rx)
static unsigned long _hcrNextPollMs   = 0;  // next scheduled hcrPoll() — own timer
static unsigned long _hcrPollTxMs     = 0;  // millis() the last poll was sent; 0 = none since beginHCR()
static unsigned long _hcrQueryTxMs    = 0;  // millis() of the last TX that can bring QVx replies back (poll, GET,VOL, ;H,RAW); 0 = none
static unsigned long _hcrVolRxMs[3]   = { 0, 0, 0 };  // per channel: millis() the HCR last confirmed it (STATUS vage); 0 = never
static uint8_t       _hcrVolCopied    = 0;  // bit ch set = cache holds a commanded value no clean poll has confirmed yet
static bool          _hcrSeedOk       = false;  // replies may seed the shadow: no volume write since the last clean poll
static int8_t        _hcrVolCand[3]   = { -1, -1, -1 };  // last reported volume per channel, awaiting a 2nd agreeing reply
static uint8_t       _hcrVolSeeded    = 0;  // bit ch set = shadow seeded from the HCR since beginHCR()
static uint8_t       _hcrFastPolls    = 0;  // 3 s re-polls left while not all three volumes are seeded

// ---- Volume + fade → the shared WcbCmd codec / fade module ------------------
// HcrCodec is the SINGLE source of truth for per-channel commanded volume (0=V,
// 1=A, 2=B; range 0-99 — the device/library range: HCRVocalizer SetEmotion/
// SetVolume cap at 99). HcrFade synthesizes the non-blocking ramp the device has
// no native command for. BOTH are the same code NaviCore runs, so an HCR fades /
// steps volume identically whichever board drives it — one command source.
static HcrCodec hcrCodec;
static HcrFade  hcrFade;

// A volume write (ours, or an opaque ;H,RAW payload) makes every reply already in
// flight stale: it reports the volume from before the write. Seeding stops until
// the next poll, and the written channels (ch -1 = all) need two fresh agreeing
// replies again. A flag rather than timestamps: nothing here can wrap.
static void hcrNoteVolWrite(int ch) {
  _hcrSeedOk = false;
  for (int c = CH_V; c <= CH_B; c++) if (ch < 0 || ch == c) _hcrVolCand[c] = -1;
}

// Show what we just commanded (the codec's shadow, i.e. the value actually sent,
// clamped 0-99) for the written channels only (ch -1 = all) — the others keep the
// HCR's own report. ;H,RAW payloads are opaque and show after the next poll.
static void hcrCacheCommanded(int ch) {
  if (!_hcr) return;
  for (int c = CH_V; c <= CH_B; c++) if (ch < 0 || ch == c) {
    _hcr->cacheVolume(c, hcrCodec.getVol(c));
    _hcrVolCopied |= (uint8_t)(1 << c);
  }
}

// Set a channel volume through the shared codec (updates its shadow = user intent).
static void hcrSetVol(int ch, int v) {
  if (ch < 0 || ch > 2 || !_hcrPort) return;
  hcrCodec.emit(*_hcrPort, 17, ch, constrain(v, 0, 100));  // fn 17 = SetVolume (HCR range 0-100)
  hcrNoteVolWrite(ch);
  hcrCacheCommanded(ch);
}

// Current commanded volume — the codec's shadow. Starts at 50; seeded from the
// HCR's own reported volume once two consecutive poll replies agree (WcbHCR::onFrame,
// re-checked on every poll), and exact after any SetVolume on this port.
static int hcrCurVol(int ch) {
  int v = hcrCodec.getVol(ch);
  return (v >= 0) ? v : 50;
}

static void hcrCancelFade(int ch) { hcrFade.cancel(ch); }

// Begin a ramp on ch from->to over durSec (delegates to the shared HcrFade; every
// step writes through hcrCodec so its shadow and the emitted bytes stay in sync).
// stopAtEnd: on reaching the end, StopWAV(ch) then restore volume to restoreTo.
static void hcrStartFade(int ch, int from, int to, int durSec,
                         bool stopAtEnd, int restoreTo) {
  if (!_hcrPort) return;
  // HcrFade::start writes now only for an instant fade or to anchor a start point
  // that differs from the shadow; otherwise the first ramp step is the first write
  // (hcrStepFades copies it). Don't show an unsent value, e.g. the default 50.
  const bool writesNow = (durSec <= 0) || (from != hcrCodec.getVol(ch));
  hcrFade.start(hcrCodec, *_hcrPort, ch, from, to, durSec, stopAtEnd, restoreTo);
  hcrNoteVolWrite(ch);
  if (writesNow) hcrCacheCommanded(ch);
}

// Step all active fades — called every loop tick (non-blocking).
static void hcrStepFades() {
  if (!_hcrPort) return;
  bool was[3]; int before[3];
  for (int c = CH_V; c <= CH_B; c++) {
    was[c]    = hcrFade.active(c);
    before[c] = hcrCodec.getVol(c);
    if (was[c]) hcrNoteVolWrite(c);   // a ramp step (or its final write) may go out now
  }
  hcrFade.tick(hcrCodec, *_hcrPort);
  // Copy only what this tick actually wrote: a step moves the shadow, and the end of a
  // fade always writes (the final level; StopWAV + restore for a fade-out). A tick with
  // no step must not copy an unsent value (e.g. the default 50 before seeding).
  for (int c = CH_V; c <= CH_B; c++)
    if (was[c] && (hcrCodec.getVol(c) != before[c] || !hcrFade.active(c))) hcrCacheCommanded(c);
}

// Status poll — ONE container, ONE write. The HCR answers each query in its own
// <...> frame, so every reply arrives after the WCB has gone quiet. Queries sent
// back to back (<QVV>\n<QVA>\n...) lose all but the last reply on S3-S5, whose RX
// edge ISR is masked while we transmit (enableIntTx(false), WCB.ino
// applySoftSerialIntTx). The leading QM is sacrificial: its reply absorbs any
// overlap with our trailing '\n'. QD = emotions/override/muse/WAV count/duration/
// playing (11 values); QVV/QVA/QVB = the three volumes, which QD does not carry.
static const char HCR_POLL_FRAME[] = "<QM,QD,QVV,QVA,QVB>\n";

// True when no reply can still be on its way: nothing that asks the HCR a question
// (poll, GET,VOL, ;H,RAW) went out in the last 250 ms (a reply set takes ~100 ms).
static bool hcrRepliesQuiet() {
  return _hcrQueryTxMs == 0 || (millis() - _hcrQueryTxMs >= 250UL);
}

static void hcrPoll() {
  if (!_hcrPort) return;
  // Re-arm seeding — unless replies to an earlier poll, GET or RAW query may still be
  // arriving: they could predate a volume write made since, and would pass the gate.
  _hcrSeedOk = hcrRepliesQuiet();
  if (_hcrSeedOk) _hcrVolCopied = 0;   // this poll's replies postdate every copy so far
  _hcrPort->print(HCR_POLL_FRAME);   // Print::print -> one write(buf,len) call
  _hcrPollTxMs = _hcrQueryTxMs = millis();
  if (debugHCR) Serial.printf("[HCR-DBG] TX poll -> %s", HCR_POLL_FRAME);   // frame ends in \n
}

// Every frame the library receives lands here once it is parsed (loop task,
// from _hcr->update()). This is what STATUS age/rx report, and — with
// ?DEBUG,HCR,ON — the only visible trace of what the HCR actually sent.
void WcbHCR::onFrame(const char *frame, bool parsed) {
  if (debugHCR) Serial.printf("[HCR-RX] <%s>%s\n", frame, parsed ? "" : "  (ignored)");
  if (!parsed) return;
  _hcrLastRxMs = millis();
  _hcrRxFrames++;

  // Seed the codec's volume shadow (the VOLUP/VOLDN/FADE start point, else 50
  // after every boot) from what the HCR reports — only while no volume write has
  // happened since the last poll (_hcrSeedOk), never mid-fade, and only when two
  // consecutive replies for the channel agree, so one reply that survived
  // validation but lost a digit ("QVA,10" for 100) can't move it. A wrong shadow
  // matters: VOLUP/VOLDN and fade restores write it back to the HCR, which
  // persists PV* in its Config.txt. The library has already validated the frame
  // (numeric, 0-100). Clamped 0-99 by setVol.
  if (frame[0] == 'Q' && frame[1] == 'V' && frame[3] == ',') {
    int ch = (frame[2] == 'V') ? CH_V : (frame[2] == 'A') ? CH_A : (frame[2] == 'B') ? CH_B : -1;
    if (ch >= 0 && (_hcrVolCopied & (1 << ch))) {
      // The WCB set this channel after the last clean poll went out, so this reply
      // may predate the write (it was already on the wire). Keep showing what we
      // commanded, and don't count it as a confirmation. Seeding is off anyway: every
      // copy follows a volume write, which clears _hcrSeedOk.
      cacheVolume(ch, hcrCodec.getVol(ch));
      return;
    }
    if (ch >= 0) _hcrVolRxMs[ch] = millis();   // the HCR confirmed this channel (STATUS vage)
    if (ch >= 0 && _hcrSeedOk && !hcrFade.active(ch)) {
      int v = (int)GetVolume(ch);
      if (_hcrVolCand[ch] == v) {
        hcrCodec.setVol(ch, v);
        _hcrVolSeeded |= (uint8_t)(1 << ch);
      }
      _hcrVolCand[ch] = (int8_t)v;
    }
  }
}

// ==================== Port-conflict Query ================================

bool isSerialPortUsedForHCR(int port) {
  return hcrConfig.configured && hcrConfig.serialPort == (uint8_t)port;
}

// ==================== Lifecycle =========================================

void beginHCR() {
  // Tear down any previous instance.
  if (_hcr) { delete _hcr; _hcr = nullptr; }
  _hcrPort = nullptr;
  // A fade from the previous binding (paused while ?HCR,CLEAR left no port) must not
  // resume on the new one.
  for (int c = CH_V; c <= CH_B; c++) hcrCancelFade(c);

  if (!hcrConfig.configured ||
      hcrConfig.serialPort < 1 || hcrConfig.serialPort > 5) {
    return;
  }

  int baud = (int)hcrConfig.baudRate;
  switch (hcrConfig.serialPort) {
    case 1: _hcr = new WcbHCR(&Serial1, baud); _hcrPort = &Serial1; break;
    case 2: _hcr = new WcbHCR(&Serial2, baud); _hcrPort = &Serial2; break;
    case 3: _hcr = new WcbHCR(&Serial3, baud); _hcrPort = &Serial3; break;
    case 4: _hcr = new WcbHCR(&Serial4, baud); _hcrPort = &Serial4; break;
    case 5: _hcr = new WcbHCR(&Serial5, baud); _hcrPort = &Serial5; break;
    default: return;
  }
  // Auto-poll is driven by processHCRTick() on its own millis() timer
  // (handles full 3-3600 s range, unlike library's uint16_t refreshSpeed).
  // pollSec 0 = off (no auto poll). update() still parses incoming RX.
  // First tick polls immediately if pollSec>0. millis(), not 0: (long)(now - 0) is
  // negative once uptime passes 2^31 ms (~24.8 days), and no poll would ever fire.
  _hcrNextPollMs = millis();
  _hcrLastRxMs   = 0;  // fresh instance, empty cache — nothing received yet
  _hcrRxFrames   = 0;
  _hcrPollTxMs   = 0;
  _hcrQueryTxMs  = 0;
  _hcrVolRxMs[0] = _hcrVolRxMs[1] = _hcrVolRxMs[2] = 0;
  _hcrVolCopied  = 0;
  _hcrSeedOk     = false;
  _hcrVolCand[0] = _hcrVolCand[1] = _hcrVolCand[2] = -1;
  _hcrVolSeeded  = 0;  // re-seed the volume shadow from the next agreeing poll replies
  _hcrFastPolls  = 10; // up to 10 polls 3 s apart (~30 s) while not seeded, then pollSec
  Serial.printf("[HCR] Active on S%d at %lu baud, poll=%us\n",
                hcrConfig.serialPort,
                (unsigned long)hcrConfig.baudRate,
                (unsigned)hcrConfig.pollSec);
}

// Call once per loop() tick. Non-blocking: HCRVocalizer::update() parses up to
// HCR_BUFFER_SIZE waiting RX bytes per call. We schedule hcrPoll() ourselves on
// a millis() timer so pollSec can be the full documented 3-3600s range
// (library's refreshSpeed is uint16_t and would overflow at >=66s).
void processHCRTick() {
  if (!_hcr) return;
  _hcr->update();
  hcrStepFades();                 // non-blocking volume ramps

  // Own-timer auto-poll. pollSec==0 -> off; user can still ?HCR,REFRESH.
  // Held while a fade runs: it writes a <PVx..> step every 150 ms, which would land
  // inside the poll's ~60-90 ms reply window and garble it. Polls when the fade ends,
  // or once the poll is a whole pollSec overdue, so a long or looping fade can't stop
  // polling (a garbled reply is rejected by the library's validation).
  unsigned long now = millis();
  bool fading = hcrFade.active(CH_V) || hcrFade.active(CH_A) || hcrFade.active(CH_B);
  long overdueMs = (long)(now - _hcrNextPollMs);
  bool hold = fading && overdueMs < (long)((unsigned long)hcrConfig.pollSec * 1000UL);
  if (hcrConfig.pollSec > 0 && !hold && overdueMs >= 0) {
    hcrPoll();
    // Until all three volumes have been seeded from the HCR (e.g. it was still
    // booting when the first poll went out), retry every 3 s instead of pollSec so
    // VOLUP/VOLDN/FADE stop stepping from the default 50 as soon as it answers.
    // Bounded (_hcrFastPolls): an HCR that never answers all three (unpowered,
    // TX-only wiring, firmware before v5 has no QVx) falls back to pollSec.
    bool fast = (_hcrVolSeeded != 0x07) && _hcrFastPolls > 0;
    if (fast) _hcrFastPolls--;
    uint16_t sec = fast ? min<uint16_t>(hcrConfig.pollSec, 3) : hcrConfig.pollSec;
    _hcrNextPollMs   = now + (unsigned long)sec * 1000UL;
  }

  // When HCR debug is on, periodically dump the parsed status so the user
  // can watch what's coming back from the HCR (the library hides per-byte
  // RX). Throttled to the poll interval (min 2s) to avoid flooding.
  if (debugHCR) {
    static unsigned long _dbgNext = 0;
    if (now >= _dbgNext) {
      uint32_t everyMs = (hcrConfig.pollSec > 0 ? hcrConfig.pollSec : 2) * 1000UL;
      if (everyMs < 2000UL) everyMs = 2000UL;
      _dbgNext = now + everyMs;
      Serial.print("[HCR-DBG] status ");
      printHCRStatus();
    }
  }
}

// ==================== Argument parsing helpers ==========================

// Split a comma list, return field idx (0-based), trimmed. "" if absent.
static String hcrField(const String &s, int idx) {
  int start = 0;
  for (int i = 0; i < idx; i++) {
    int c = s.indexOf(',', start);
    if (c < 0) return "";
    start = c + 1;
  }
  int end = s.indexOf(',', start);
  String v = (end < 0) ? s.substring(start) : s.substring(start, end);
  v.trim();
  return v;
}

// Emotion: H/S/M/C or HAPPY/SAD/MAD/SCARED -> 0..3, OVERLOAD -> 4, else -1
static int hcrEmotion(const String &t) {
  String u = t; u.trim(); u.toUpperCase();
  if (u == "H" || u == "HAPPY")    return HAPPY;
  if (u == "S" || u == "SAD")      return SAD;
  if (u == "M" || u == "MAD")      return MAD;
  if (u == "C" || u == "SCARED")   return SCARED;
  if (u == "O" || u == "OVERLOAD") return OVERLOAD;
  return -1;
}

// Level: MOD/MODERATE/0 -> 0, STRONG/1 -> 1, else -1
static int hcrLevel(const String &t) {
  String u = t; u.trim(); u.toUpperCase();
  if (u == "MOD" || u == "MODERATE" || u == "0") return EMOTE_MODERATE;
  if (u == "STRONG" || u == "1")                 return EMOTE_STRONG;
  return -1;
}

// Audio channel: V/A/B -> 0/1/2, else -1
static int hcrChan(const String &t) {
  String u = t; u.trim(); u.toUpperCase();
  if (u == "V") return CH_V;
  if (u == "A") return CH_A;
  if (u == "B") return CH_B;
  return -1;
}

// Stop style for ;H,STOP / ;H,STOPEMOTE: "NOW" (also the empty field, i.e. the
// pre-existing two-field form) or "GRACEFUL". "" = not a style, so the caller
// can reject a typo instead of cutting the vocalizer off by accident.
static String hcrStopStyle(const String &t) {
  String u = t; u.trim(); u.toUpperCase();
  if (u == "" || u == "NOW" || u == "N" || u == "HARD")       return "NOW";
  if (u == "GRACEFUL" || u == "G" || u == "SOFT")             return "GRACEFUL";
  return "";
}

// ==================== Runtime dispatch (;H,...) =========================

void processHCRRuntimeCommand(const String &message) {
  // message arrives as "H,<verb>,<args...>" (leading 'H' from ;H routing).
  if (!_hcr || !hcrConfig.configured) {
    Serial.println("[HCR] Not configured — use ?HCR,PORT,Sx:baud first");
    return;
  }

  // Strip the leading "H" / "H,"
  String body = message;
  body.trim();
  if (body.length() >= 1 && (body[0] == 'H' || body[0] == 'h')) {
    body = (body.length() >= 2 && body[1] == ',') ? body.substring(2)
                                                  : body.substring(1);
  }
  body.trim();
  if (body.length() == 0) { Serial.println("[HCR] Empty ;H command"); return; }

  String verb = hcrField(body, 0);
  String vU   = verb; vU.toUpperCase();

  if (debugHCR) Serial.printf("[HCR-DBG] cmd in: ;H,%s\n", body.c_str());

  // ---- RAW: send the remainder verbatim (may contain commas) ----------
  if (vU == "RAW") {
    int firstComma = body.indexOf(',');
    String payload = (firstComma < 0) ? "" : body.substring(firstComma + 1);
    if (payload.length() == 0) { Serial.println("[HCR] RAW needs a payload"); return; }
    if (_hcrPort) {
      _hcrPort->print(payload);
      if (!payload.endsWith("\n")) _hcrPort->print('\n');
      hcrNoteVolWrite(-1);   // opaque payload may carry a <PV..> — don't seed from older replies
      _hcrQueryTxMs = millis();   // ...or a <Q..>: its replies are in flight for the next ~100 ms
    }
    if (debugHCR || debugEnabled) Serial.printf("[HCR-DBG] TX raw -> %s\n", payload.c_str());
    return;
  }

  // ---- FN,fn,chan,track : RC-Controller numeric convention ------------
  if (vU == "FN") {
    int fn    = hcrField(body, 1).toInt();
    int chan  = hcrField(body, 2).toInt();
    int track = hcrField(body, 3).toInt();
    // fn reaches the codec as a uint8_t, so 260 silently became fn 4 - a DIFFERENT function ran
    // and the command reported success. Reject it before the cast rather than after.
    if (fn < 0 || fn > 255) {
      Serial.printf("[HCR] FN %d out of range (0-255)\n", fn);
      return;
    }
    // Route the numeric RC-Controller convention through the shared HcrCodec — one
    // source of truth with NaviCore (both compile WcbHcr.cpp). normalize() owns the
    // per-fn ranges (rejects out-of-range chan/track, emotion chan 4, track>99) and
    // covers fns 2-13, 16, 17, 18, 19. fn 14 (PlayWAV) stays on the HCRVocalizer
    // library to keep its 150 ms per-channel debounce — its bytes are identical to
    // the codec's PlayWAV.
    if (fn == 14) {
      if (chan < 0 || chan > 2) {
        Serial.printf("[HCR] FN 14 channel %d out of range (0-2)\n", chan);
        return;
      }
      // fn 14 goes straight to the library for its 150 ms debounce, so it misses the track
      // range check HcrCodec applies to every other fn. Apply the same bound here.
      if (track < 0 || track > 9999) {
        Serial.printf("[HCR] FN 14 track %d out of range (0-9999)\n", track);
        return;
      }
      if (_hcr) { _hcr->PlayWAV(chan, track); _hcr->update(); }
    } else if (_hcrPort && hcrCodec.emit(*_hcrPort, (uint8_t)fn, chan, track)) {
      if (fn == 2 && _hcr) _hcr->update();   // SetEmotion: nudge an immediate status refresh (matches old)
      if (fn == 17 && chan >= 0 && chan <= 2) { hcrNoteVolWrite(chan); hcrCacheCommanded(chan); }  // SetVolume(ch)
      else if (fn >= 17 && fn <= 19)          { hcrNoteVolWrite(-1);   hcrCacheCommanded(-1); }    // ALL / Up/DownAll
    } else {
      Serial.printf("[HCR] FN %d,%d,%d rejected (unknown fn or out-of-range)\n", fn, chan, track);
      return;
    }
    if (debugHCR || debugEnabled) Serial.printf("[HCR-DBG] FN %d,%d,%d\n", fn, chan, track);
    return;
  }

  // ---- Readable verbs --------------------------------------------------
  if (vU == "STIM" || vU == "STIMULATE" || vU == "TRIGGER") {
    int e = hcrEmotion(hcrField(body, 1));
    // OVERLOAD is its own top-level verb; don't silently rewrite it here.
    if (e == OVERLOAD) {
      Serial.printf("[HCR] %s does not take OVERLOAD — use ;H,OVERLOAD\n", vU.c_str());
      return;
    }
    int lv = hcrLevel(hcrField(body, 2));
    if (e < 0 || lv < 0) { Serial.println("[HCR] Usage: ;H,STIM,<H|S|M|C>,<MOD|STRONG>"); return; }
    if (vU == "TRIGGER") _hcr->Trigger(e, lv);
    else                 _hcr->Stimulate(e, lv);
    return;
  }
  if (vU == "OVERLOAD")      { _hcr->Overload();      return; }
  if (vU == "RESETEMOTIONS") { _hcr->ResetEmotions(); return; }

  // STOP / STOPEMOTE take an optional style: NOW (default, unchanged) cuts the
  // vocalizer off with <PSV>; GRACEFUL lets it finish the sound it is making with
  // <PSG>. Before this, nothing in the ;H layer could reach <PSG>, and declaring
  // the port with ?HCR,PORT is what made it unreachable by raw frame too (the
  // port leaves the broadcast loop). Issue #15. An unrecognised style is rejected
  // rather than treated as NOW: silently cutting a droid off is the wrong default
  // for a typo, and the old callers pass no style at all.
  if (vU == "STOP" || vU == "STOPEMOTE") {
    const String st = hcrStopStyle(hcrField(body, 1));
    if (st == "") {
      Serial.printf("[HCR] Usage: ;H,%s[,NOW|GRACEFUL]\n", vU.c_str());
      return;
    }
    const bool graceful = (st == "GRACEFUL");
    // Cancel any ramp in flight FIRST. HcrFade keeps writing after the stop otherwise: a FADEOUT
    // lands its final StopWAV and volume restore ~dur later and a FADEIN keeps raising the
    // volume, both after the user asked for silence. ;H,STOPWAV and ;H,VOL already cancel.
    if (vU == "STOPEMOTE") {
      hcrCancelFade(0);                                // the vocalizer channel
    } else {
      for (int c = 0; c < 3; c++) hcrCancelFade(c);    // STOP silences all three
    }
    if (vU == "STOPEMOTE") { if (graceful) _hcr->StopEmoteGraceful(); else _hcr->StopEmote(); }
    else                   { if (graceful) _hcr->StopGraceful();      else _hcr->Stop();      }
    if (debugHCR) Serial.printf("[HCR-DBG] %s %s\n", vU.c_str(), st.c_str());
    return;
  }

  if (vU == "SETEMOTION") {
    int e = hcrEmotion(hcrField(body, 1));
    int v = hcrField(body, 2).toInt();
    if (e < 0 || e > SCARED || v < 0 || v > 100) {
      Serial.println("[HCR] Usage: ;H,SETEMOTION,<H|S|M|C>,<0-100>"); return;
    }
    _hcr->SetEmotion(e, v); _hcr->update();
    return;
  }

  if (vU == "OVERRIDE") {
    String a = hcrField(body, 1); a.toUpperCase();
    _hcr->OverrideEmotions((a == "1" || a == "ON") ? 1 : 0);
    return;
  }

  if (vU == "MUSE") {
    String a = hcrField(body, 1); a.toUpperCase();
    if (a == "")        { _hcr->Muse(); return; }                  // single muse
    if (a == "GAP") {
      int mn = hcrField(body, 2).toInt();
      int mx = hcrField(body, 3).toInt();
      _hcr->Muse(mn, mx);
      return;
    }
    if (a == "TOGGLE")  { _hcr->SetMuse(_hcr->GetMuse() ? 0 : 1); return; }
    _hcr->SetMuse((a == "1" || a == "ON") ? 1 : 0);
    return;
  }

  if (vU == "PLAY") {
    int ch = hcrChan(hcrField(body, 1));            // A|B
    int fl = hcrField(body, 2).toInt();
    if ((ch != CH_A && ch != CH_B) || fl < 0 || fl > 9999) {
      Serial.println("[HCR] Usage: ;H,PLAY,<A|B>,<0-9999>[,FADEIN,<sec>]"); return;
    }
    String opt = hcrField(body, 3); opt.toUpperCase();
    if (opt == "FADEIN") {
      int sec    = hcrField(body, 4).toInt();
      int target = hcrCurVol(ch);                   // capture intended level
      hcrCancelFade(ch);
      _hcr->SetVolume(ch, 0);                       // silent BEFORE play (no blip)
      hcrNoteVolWrite(ch);
      _hcr->cacheVolume(ch, 0);
      _hcrVolCopied |= (uint8_t)(1 << ch);
      _hcr->PlayWAV(ch, fl); _hcr->update();
      hcrStartFade(ch, 0, target, sec, false, 0);   // 0 -> target
    } else {
      hcrCancelFade(ch);
      _hcr->PlayWAV(ch, fl); _hcr->update();
    }
    return;
  }
  if (vU == "STOPWAV") {
    int ch = hcrChan(hcrField(body, 1));
    if (ch != CH_A && ch != CH_B) { Serial.println("[HCR] Usage: ;H,STOPWAV,<A|B>"); return; }
    hcrCancelFade(ch);
    _hcr->StopWAV(ch);
    return;
  }
  if (vU == "VOL" || vU == "VOLUME") {
    // ;H,VOL[,<V|A|B>],<0-100>
    // Channel is OPTIONAL: omit it to set ALL channels (V, A and B) to the value,
    // mirroring VOLUP/VOLDN. Field 1 is the channel when it names one; otherwise
    // field 1 is the value itself (no channel given -> apply to all).
    String f1  = hcrField(body, 1);
    int    ch  = hcrChan(f1);                        // V|A|B -> index, -1 if not a channel
    bool   all = (ch < 0);                           // numeric field 1 -> all channels
    // A non-channel, non-numeric field 1 is a TYPO, not a request to set every channel:
    // ";H,VOL,X,40" and ";H,VOL,ALL,40" used to take that word as the value, toInt() it to 0,
    // and mute V, A and B - reported as success. Only digits mean "all channels".
    bool f1Numeric = f1.length() > 0;
    for (int i = 0; i < (int)f1.length(); i++) {
      if (!isdigit((unsigned char)f1.charAt(i))) { f1Numeric = false; break; }
    }
    if (all && !f1Numeric) {
      Serial.println("[HCR] Usage: ;H,VOL[,<V|A|B>],<0-100>  (a channel is V, A or B)");
      return;
    }
    String vStr = all ? f1 : hcrField(body, 2);
    int    v    = vStr.toInt();
    if (!vStr.length() || v < 0 || v > 100) {
      Serial.println("[HCR] Usage: ;H,VOL[,<V|A|B>],<0-100>");
      return;
    }
    const int chans[3] = { CH_V, CH_A, CH_B };
    const int n = all ? 3 : 1;
    for (int i = 0; i < n; i++) {
      const int c = all ? chans[i] : ch;
      hcrCancelFade(c);
      hcrSetVol(c, v);
      if (debugHCR) Serial.printf("[HCR-DBG] VOL ch=%d -> %d\n", c, v);
    }
    return;
  }
  if (vU == "VOLUP" || vU == "VOLDN" || vU == "VOLDOWN") {
    // ;H,VOLUP|VOLDN[,<V|A|B>][,<step>]
    // Channel is OPTIONAL: omit it (or pass just the step) to bump ALL channels
    // (V, A and B) by the step. Step default 5.
    String f1   = hcrField(body, 1);
    int    ch   = hcrChan(f1);                       // V|A|B -> index, -1 if not a channel
    bool   all  = (ch < 0);                          // no/invalid channel -> all channels
    // Step is field 2 when a channel was named; otherwise field 1 (the step) or default.
    String sStr = all ? (f1.length() ? f1 : hcrField(body, 2)) : hcrField(body, 2);
    int    step = sStr.length() ? sStr.toInt() : 5;
    if (step <= 0) step = 5;
    const bool up = (vU == "VOLUP");
    const int  chans[3] = { CH_V, CH_A, CH_B };
    const int  n = all ? 3 : 1;
    for (int i = 0; i < n; i++) {
      const int c   = all ? chans[i] : ch;
      const int cur = hcrCurVol(c);
      const int nv  = up ? cur + step : cur - step;
      hcrCancelFade(c);
      hcrSetVol(c, nv);                              // hcrSetVol clamps 0-100
      if (debugHCR) Serial.printf("[HCR-DBG] %s ch=%d %d->%d\n",
                                  vU.c_str(), c, cur, hcrCurVol(c));   // the value actually sent
    }
    return;
  }
  if (vU == "FADEOUT") {
    int ch  = hcrChan(hcrField(body, 1));           // A|B
    int sec = hcrField(body, 2).toInt();
    if (ch != CH_A && ch != CH_B) { Serial.println("[HCR] Usage: ;H,FADEOUT,<A|B>,<sec>"); return; }
    int cur = hcrCurVol(ch);
    hcrStartFade(ch, cur, 0, sec, true, cur);       // ramp->0, StopWAV, restore cur
    return;
  }
  if (vU == "FADEIN") {
    int ch  = hcrChan(hcrField(body, 1));           // A|B
    int sec = hcrField(body, 2).toInt();
    if (ch != CH_A && ch != CH_B) { Serial.println("[HCR] Usage: ;H,FADEIN,<A|B>,<sec>"); return; }
    int target = hcrCurVol(ch);
    hcrStartFade(ch, 0, target, sec, false, 0);     // 0 -> captured target
    return;
  }

  Serial.printf("[HCR] Unknown ;H command: %s\n", verb.c_str());
}

// ==================== Configuration (?HCR,...) ==========================

void clearHCRConfig() {
  uint8_t freedPort   = hcrConfig.serialPort;
  // ?HCR,CLEAR removes the LOCAL host only. The auto-learned remote route is a
  // separate axis (cleared by ?HCR,REMOTE,OFF or a factory reset), so a Wizard
  // full-push CLEAR on a board it models as "no HCR" can't silently wipe a route
  // the Wizard never observed. Preserve it across the memset.
  uint8_t savedRemote = hcrConfig.remoteWCB;

  if (_hcr) { delete _hcr; _hcr = nullptr; }
  _hcrPort = nullptr;

  memset(&hcrConfig, 0, sizeof(hcrConfig));
  hcrConfig.configured = false;
  hcrConfig.baudRate   = 9600;
  hcrConfig.pollSec    = 10;
  hcrConfig.remoteWCB  = savedRemote;

  saveHCRSettings();
  Serial.println("[HCR] Local configuration cleared");
  if (hcrConfig.remoteWCB > 0)
    Serial.printf("  (still routing ;H to WCB%d — %cHCR,REMOTE,OFF to stop)\n",
                  hcrConfig.remoteWCB, LocalFunctionIdentifier);

  if (freedPort > 0) {
    if (!serialBroadcastEnabled[freedPort - 1]) {
      serialBroadcastEnabled[freedPort - 1] = true;
      saveBroadcastSettingsToPreferences();
      Serial.printf("  ✓ Re-enabled broadcast output on S%d\n", freedPort);
    }
    if (blockBroadcastFrom[freedPort - 1]) {
      blockBroadcastFrom[freedPort - 1] = false;
      saveBroadcastBlockSettings();
      Serial.printf("  ✓ Re-enabled broadcast input on S%d\n", freedPort);
    }
    updateBaudRate(freedPort, 9600);
    saveSerialLabelToPreferences(freedPort, "");
    Serial.printf("  ✓ Released S%d (old HCR port)\n", freedPort);
  }
}

static void hcrReservePort(int serialPort, int baudRate) {
  // Release old port if moving.
  if (hcrConfig.configured && hcrConfig.serialPort > 0 &&
      hcrConfig.serialPort != (uint8_t)serialPort) {
    uint8_t oldPort = hcrConfig.serialPort;
    if (!serialBroadcastEnabled[oldPort - 1]) {
      serialBroadcastEnabled[oldPort - 1] = true;
      saveBroadcastSettingsToPreferences();
    }
    if (blockBroadcastFrom[oldPort - 1]) {
      blockBroadcastFrom[oldPort - 1] = false;
      saveBroadcastBlockSettings();
    }
    saveSerialLabelToPreferences(oldPort, "");
    Serial.printf("  ✓ Released S%d (old HCR port)\n", oldPort);
  }

  // Apply baud live (handles S1/S2 divisor + S3-5 software re-init).
  if ((uint32_t)baudRate != baudRates[serialPort - 1]) {
    updateBaudRate(serialPort, baudRate);
  } else {
    applyLiveBaud(serialPort, (uint32_t)baudRate);
  }

  // Reserve the port: HCRVocalizer owns RX, so disable broadcast both ways.
  if (serialBroadcastEnabled[serialPort - 1]) {
    serialBroadcastEnabled[serialPort - 1] = false;
    saveBroadcastSettingsToPreferences();
    Serial.printf("  ⚠️  Disabled broadcast output on S%d (HCR port)\n", serialPort);
  }
  if (!blockBroadcastFrom[serialPort - 1]) {
    blockBroadcastFrom[serialPort - 1] = true;
    saveBroadcastBlockSettings();
    Serial.printf("  ⚠️  Disabled broadcast input on S%d (HCR port)\n", serialPort);
  }
  saveSerialLabelToPreferences(serialPort, "HCR");

  hcrConfig.serialPort = (uint8_t)serialPort;
  hcrConfig.baudRate   = (uint32_t)baudRate;
  hcrConfig.configured = true;
  hcrConfig.remoteWCB  = 0;   // we host it now — not a client of another board
  // pollSec is preserved from NVS/POLL command (default 10, 0 = user set OFF).

  saveHCRSettings();
  beginHCR();
  Serial.printf("[HCR] Configured on S%d at %d baud\n", serialPort, baudRate);
}

void configureHCR(const String &args) {
  String a = args; a.trim();
  String aU = a;   aU.toUpperCase();

  if (aU == "LIST")            { printHCRSettings(); return; }
  if (aU == "CLEAR")           { clearHCRConfig();   return; }
  if (aU == "STATUS")          { printHCRStatus();   return; }
  if (aU == "REFRESH")         {
    if (_hcr) { hcrPoll(); Serial.println("[HCR] Refresh requested"); }
    else      Serial.println("[HCR] Not configured");
    return;
  }

  // ---- REMOTE,W<n> | REMOTE,OFF — route ;H to the HCR on another board ----
  // Persisted routing (auto-learned from WDP, or set by hand / restored from a
  // backup). A board that HOSTS an HCR locally never needs this.
  if (aU.startsWith("REMOTE")) {
    String v = (a.indexOf(',') >= 0) ? a.substring(a.indexOf(',') + 1) : "";
    v.trim(); String vU = v; vU.toUpperCase();
    if (vU == "" || vU == "OFF" || vU == "0") {
      hcrConfig.remoteWCB = 0;
      saveHCRSettings();
      Serial.println("[HCR] Remote routing cleared");
      return;
    }
    int wIdx = vU.indexOf('W');
    int host = (wIdx >= 0) ? v.substring(wIdx + 1).toInt() : v.toInt();
    // Bound MUST match what auto-learn + routing accept (1..MAX_WCB_COUNT, incl.
    // learned peers ABOVE the WCBQ floor) — else an auto-learned host above the
    // floor round-trips into the backup but is rejected on restore, silently
    // dropping the persisted route.
    if (host < 1 || host > MAX_WCB_COUNT || host == WCB_Number) {
      Serial.printf("[HCR] Invalid host. Use %cHCR,REMOTE,W<n> (1-%d, not this board)\n",
                    LocalFunctionIdentifier, MAX_WCB_COUNT);
      return;
    }
    if (hcrConfig.configured) clearHCRConfig();   // was a local host — release the port
    hcrConfig.remoteWCB = (uint8_t)host;
    saveHCRSettings();
    Serial.printf("[HCR] Routing ;H to WCB%d\n", host);
    return;
  }

  // ---- POLL,<sec|OFF> -------------------------------------------------
  if (aU.startsWith("POLL")) {
    String v = (a.indexOf(',') >= 0) ? a.substring(a.indexOf(',') + 1) : "";
    v.trim(); String vU = v; vU.toUpperCase();
    if (vU == "OFF" || vU == "0") hcrConfig.pollSec = 0;
    else {
      int s = v.toInt();
      if (s < 3 || s > 3600) { Serial.println("[HCR] POLL must be 3-3600 s, or OFF (min 3s keeps any serial port safe)"); return; }
      hcrConfig.pollSec = (uint16_t)s;
    }
    saveHCRSettings();
    // Reschedule next poll immediately so the new interval takes effect now.
    _hcrNextPollMs = millis();
    Serial.printf("[HCR] Poll interval = %us%s\n", (unsigned)hcrConfig.pollSec,
                  hcrConfig.pollSec ? "" : " (off)");
    return;
  }

  // ---- GET,<field> ----------------------------------------------------
  if (aU.startsWith("GET,")) {
    if (!_hcr) { Serial.println("[HCR] Not configured"); return; }
    String f = a.substring(4); f.trim(); String fU = f; fU.toUpperCase();
    String key = hcrField(fU, 0);
    if      (key == "EMOTION") { int e = hcrEmotion(hcrField(fU,1));
                                 Serial.printf("[HCR] EMOTION %s = %d\n", f.c_str(),
                                               e >= 0 ? _hcr->GetEmotion(e) : -1); }
    else if (key == "DURATION") Serial.printf("[HCR] DURATION = %.2f\n", _hcr->GetDuration());
    else if (key == "OVERRIDE") Serial.printf("[HCR] OVERRIDE = %d\n", _hcr->GetOverride());
    else if (key == "MUSE")     Serial.printf("[HCR] MUSE = %d\n", _hcr->GetMuse());
    else if (key == "WAVCOUNT") Serial.printf("[HCR] WAVCOUNT = %d\n", _hcr->GetWAVCount());
    else if (key == "PLAYING")  { int c = hcrChan(hcrField(fU,1));
                                  Serial.printf("[HCR] PLAYING %s = %d\n", f.c_str(),
                                                c >= 0 ? _hcr->GetPlayingWAV(c) : -1); }
    else if (key == "VOL")      { int c = hcrChan(hcrField(fU,1));
                                  // Ask the HCR, then print what is cached now: like stock, one
                                  // call behind (the reply lands ~50 ms later; GET again, or read
                                  // STATUS, for it). QM first: its reply absorbs the overlap with
                                  // our trailing '\n', which loses a bare query's reply ~6 in 10.
                                  if (c >= 0 && _hcrPort) {
                                    // No poll reply in flight (as hcrPoll's rule): this query's
                                    // answer postdates any copy, so let it confirm the channel.
                                    if (hcrRepliesQuiet())
                                      _hcrVolCopied &= (uint8_t)~(1 << c);
                                    _hcrPort->print(c == CH_V ? "<QM,QVV>\n" : c == CH_A ? "<QM,QVA>\n" : "<QM,QVB>\n");
                                    _hcrQueryTxMs = millis();
                                  }
                                  Serial.printf("[HCR] VOL %s = %.0f\n", f.c_str(),
                                                c >= 0 ? _hcr->GetVolume(c) : -1.0f); }
    else Serial.println("[HCR] GET fields: EMOTION,H|S|M|C / DURATION / OVERRIDE / "
                        "MUSE / WAVCOUNT / PLAYING,V|A|B / VOL,V|A|B");
    return;
  }

  // ---- PORT,S<port>:<baud> -------------------------------------------
  String spec = a;
  if (aU.startsWith("PORT,")) spec = a.substring(5);   // tolerate ?HCR,PORT,S1:9600
  spec.trim();
  String specU = spec; specU.toUpperCase();

  if (!specU.startsWith("S")) {
    Serial.printf("[HCR] Invalid. Use: %cHCR,PORT,S<port>:<baud>  (e.g. S1:9600)\n",
                  LocalFunctionIdentifier);
    return;
  }
  int colon = spec.indexOf(':');
  if (colon < 0) {
    Serial.printf("[HCR] Missing baud. Use: %cHCR,PORT,S<port>:<baud>\n",
                  LocalFunctionIdentifier);
    return;
  }
  int serialPort = spec.substring(1, colon).toInt();
  int baudRate   = spec.substring(colon + 1).toInt();

  if (serialPort < 1 || serialPort > 5) {
    Serial.println("[HCR] Invalid serial port. Must be S1-S5"); return;
  }
  if (baudRate != 9600 && baudRate != 19200 && baudRate != 38400 &&
      baudRate != 57600 && baudRate != 115200) {
    Serial.println("[HCR] Baud must be 9600/19200/38400/57600/115200"); return;
  }
  // S3-S5 are software UARTs (RMT TX, level-3 GPIO RX ISR) measured exact through 57600 and 0/20 lines at 115200
  // (CLAUDE.md rule 13; ?BAUD applies the same limit, WCB_Storage.cpp). The HCR answers every poll, so its port
  // must receive reliably: 115200 is refused, 19200-57600 are allowed. They were refused above 9600 until
  // 2026-09-24, a limit left over from the bit-banged TX (docs/HIL_TEST_AUDIT.md F1).
  if (serialPort >= 3 && baudRate > 57600) {
    Serial.println("\n⚠️  =============== WARNING ===============");
    Serial.printf("S%d is SOFTWARE SERIAL — %d baud is not received reliably (measured exact through 57600)\n",
                  serialPort, baudRate);
    Serial.println("❌ CONFIGURATION BLOCKED!");
    Serial.printf("  Use a hardware port: %cHCR,PORT,S1:%d   or   S%d:57600\n",
                  LocalFunctionIdentifier, baudRate, serialPort);
    Serial.println("=========================================\n");
    return;
  }

  // ---- Reject a port already claimed by PWM / Kyber / MP3 ----------
  // Mirrors canUsePWMOnPort (WCB_PWM.cpp) so two subsystems can't silently
  // share one UART. Does NOT check HCR itself, so re-configuring HCR on its
  // own port is still allowed.
  // Kyber: only the port a Kyber mode owns - kyberModeReservesPort (WCB_Storage.cpp, tracker #73 D4).
  if (isSerialPortPWMOutput(serialPort) || isSerialPortUsedForPWMInput(serialPort) ||
      isSerialPortUsedForMP3(serialPort) || isSerialPortUsedForWLED(serialPort) ||
      isSerialPortUsedForDFP(serialPort) || kyberModeReservesPort(serialPort)) {
    Serial.printf("[HCR] S%d already in use by PWM/Kyber/MP3/WLED/DFP - config blocked\n", serialPort);
    return;
  }
  // A local Maestro owns its port as firmly: its frames and this device's bytes would share the wire, and this
  // module's CLEAR would reset the port's baud and flags under it (WCB coverage re-scan #15). Its own line, because the
  // one above is matched by tests and tools.
  if (isSerialPortUsedForMaestro(serialPort)) {
    Serial.printf("[HCR] S%d is a local Maestro's port - config blocked\n", serialPort);
    return;
  }
  // A serial mapping reads this port: processIncomingSerial returns before reading a device's port, so a text mapping
  // on it would go deaf, and a raw one would race this device's reader for the bytes (tracker #99; PWM has the same
  // rule both ways, D23).
  if (isSerialPortMonitored(serialPort)) {
    Serial.printf("[HCR] S%d is read by a serial mapping - config blocked\n", serialPort);
    return;
  }

  hcrReservePort(serialPort, baudRate);
}

// ==================== Status / List =====================================

void printHCRSettings() {
  Serial.println("---- HCR Configuration ----");
  if (!hcrConfig.configured) {
    if (hcrConfig.remoteWCB > 0)
      Serial.printf("  Routes ;H to WCB%d (remote host)\n", hcrConfig.remoteWCB);
    else
      Serial.println("  Not configured.  Use ?HCR,PORT,S<port>:<baud>");
    return;
  }
  Serial.printf("  Port:  S%d\n", hcrConfig.serialPort);
  Serial.printf("  Baud:  %lu\n", (unsigned long)hcrConfig.baudRate);
  Serial.printf("  Poll:  %us%s\n", (unsigned)hcrConfig.pollSec,
                hcrConfig.pollSec ? "" : " (off)");
  Serial.printf("  Link:  %s\n", _hcr ? "active" : "inactive");
}

void printHCRStatus() {
  if (!hcrConfig.configured || !_hcr) {
    Serial.println("[HCR:cfg=0]");
    return;
  }
  // age = seconds since the HCR's last parsed frame (-1 = nothing received since
  // the port was bound). It used to be the time since the poll was SENT, which
  // cycled 0..pollSec whether or not the HCR ever answered. rx = frames parsed.
  long ageSec = -1;
  if (_hcrLastRxMs != 0) {
    ageSec = (long)((millis() - _hcrLastRxMs) / 1000UL);
  }
  // vage = seconds since the HCR last confirmed the LEAST recently confirmed of
  // vV/vA/vB (a parsed QVx reply; -1 = one of them never has since the port was
  // bound). A channel the WCB just set stays unconfirmed until a later poll answers,
  // so vage keeps growing meanwhile. age alone can't say how fresh vV/vA/vB are:
  // replies to PLAY/STIM keep it near 0 while no poll has landed.
  long vageSec = 0;
  unsigned long nowMs = millis();
  for (int c = CH_V; c <= CH_B; c++) {
    if (_hcrVolRxMs[c] == 0) { vageSec = -1; break; }
    long a = (long)((nowMs - _hcrVolRxMs[c]) / 1000UL);
    if (a > vageSec) vageSec = a;
  }
  // Cached values only — this must never transmit. It used to call getVolume()
  // x3, which sent <QVV><QVA><QVB> back to back; on S3-S5 the port can't receive
  // while it transmits (enableIntTx(false)), so only vB ever refreshed. It also
  // runs from the ?DEBUG,HCR dump, which then perturbed the link it reported on.
  char line[256];
  snprintf(line, sizeof(line),
    "[HCR:cfg=1,port=%d,poll=%u,age=%ld,H=%d,S=%d,M=%d,C=%d,dur=%.2f,"
    "ovr=%d,muse=%d,wav=%d,pV=%d,pA=%d,pB=%d,vV=%.0f,vA=%.0f,vB=%.0f,rx=%lu,vage=%ld]",
    hcrConfig.serialPort,
    (unsigned)hcrConfig.pollSec,
    ageSec,
    _hcr->GetEmotion(HAPPY), _hcr->GetEmotion(SAD),
    _hcr->GetEmotion(MAD),   _hcr->GetEmotion(SCARED),
    _hcr->GetDuration(),
    _hcr->GetOverride(),
    _hcr->GetMuse(),
    _hcr->GetWAVCount(),
    _hcr->GetPlayingWAV(CH_V), _hcr->GetPlayingWAV(CH_A), _hcr->GetPlayingWAV(CH_B),
    _hcr->GetVolume(CH_V), _hcr->GetVolume(CH_A), _hcr->GetVolume(CH_B),
    (unsigned long)_hcrRxFrames, vageSec);
  Serial.println(line);
}

void emitHCRBackup(const std::function<void(const String &)> &emit) {
  // Client board (no local HCR, routes ;H to a remote host): persist the route.
  if (!hcrConfig.configured) {
    if (hcrConfig.remoteWCB > 0) {
      String suffix = "HCR,REMOTE,W" + String(hcrConfig.remoteWCB);
      emit(suffix);
    }
    return;
  }

  String suffix = "HCR,PORT,S" + String(hcrConfig.serialPort) +
                  ":" + String(hcrConfig.baudRate);
  emit(suffix);

  suffix = "HCR,POLL," + String(hcrConfig.pollSec);
  emit(suffix);
}

// ==================== NVS storage =======================================

void saveHCRSettings() {
  preferences.begin("hcr_cfg", false);
  preferences.putUChar("port", hcrConfig.serialPort);
  preferences.putUInt ("baud", hcrConfig.baudRate);
  preferences.putBool ("en",   hcrConfig.configured);
  preferences.putUShort("poll", hcrConfig.pollSec);
  preferences.putUChar("rwcb", hcrConfig.remoteWCB);
  preferences.end();
}

void loadHCRSettings() {
  preferences.begin("hcr_cfg", true);
  hcrConfig.serialPort = preferences.getUChar ("port", 0);
  hcrConfig.baudRate   = preferences.getUInt  ("baud", 9600);
  hcrConfig.configured = preferences.getBool  ("en",   false);
  hcrConfig.pollSec    = preferences.getUShort("poll", 10);
  hcrConfig.remoteWCB  = preferences.getUChar ("rwcb", 0);
  preferences.end();

  if (hcrConfig.configured) {
    Serial.printf("[HCR] Loaded: S%d at %lu baud, poll=%us\n",
                  hcrConfig.serialPort,
                  (unsigned long)hcrConfig.baudRate,
                  (unsigned)hcrConfig.pollSec);
  } else if (hcrConfig.remoteWCB > 0) {
    Serial.printf("[HCR] Loaded: routes ;H to WCB%d\n", hcrConfig.remoteWCB);
  }
}

// Auto-learn the HCR host from a WDP advert. First-host-wins + persisted: never
// override a local host or an already-stored host (a physical move is re-set by
// hand / ?HCR,REMOTE). Returns true if a host was newly stored.
bool hcrAutoAddRemote(uint8_t hostWCB) {
  if (hostWCB == 0 || hostWCB == WCB_Number) return false;
  if (hcrConfig.configured)                  return false;   // we host it locally
  if (hcrConfig.remoteWCB != 0)              return false;   // already have a host
  hcrConfig.remoteWCB = hostWCB;
  saveHCRSettings();
  Serial.printf("[WDP] HCR host learned — routing ;H to WCB%d\n", hostWCB);
  return true;
}
