greghulette/Wireless_Communication_Board-WCB/Wizard/parser.js

/**
 * WCB Backup Parser & Data Model
 * 
 * Parses the output of the ?backup command from WCB firmware.
 * Builds a structured JavaScript object (BoardConfig) from the
 * chained command string.
 * 
 * The ?backup command outputs two formats:
 *   1. Configured format  — uses board's current delimiter & funcchar
 *   2. Factory reset format — always uses ^ delimiter and ? funcchar
 * 
 * The parser extracts the factory reset format line (always last)
 * since it has a known, stable format regardless of board config.
 */

// ─────────────────────────────────────────────
// Default BoardConfig — represents a fresh/unconfigured board
// All fields set to firmware defaults
// ─────────────────────────────────────────────
function createDefaultBoardConfig() {
  return {
    // Board Identity
    hwVersion:    0,       // 0 = not set, 1=1.0, 21=2.1, 23=2.3, 24=2.4, 31=3.1, 32=3.2
    statusLedPin: 38,      // GPIO pin for onboard NeoPixel — HW 3.1/3.2 only; 38 is the firmware default for both (WCB_Help.cpp:1009). Not auto-changed by HW version.
    wcbNumber:    1,
    wcbQuantity:  1,
    meshChannel:  1,       // ESP-NOW mesh channel (1–13); network-wide, all boards must match
    livePeerCount: null,   // PEERSLIVE telemetry (read-only; null = not reported)
    alias:        '',      // Friendly per-WCB name; ≤24 chars; '' = unset
    specialPeer:  false,   // ?SPECIAL,ON enables tracking of the special peer (NaviCore)
    specialPeerId: 20,     // special peer ID (1-20); used only when specialPeer is true
    // ---- Wizard-only metadata (never sent to firmware) ----------------
    // Slot type: 'wcb' (default — board card) or 'client' (lightweight
    // client view). Flipping does NOT alter what's on the physical board.
    type:         'wcb',
    clientAlias:  '',      // Friendly name for the client device at this slot
    isRelay:      false,   // true when the device's backup carried ?RELAY,1 (a MgmtRelay)


    // Network
    espnowPassword: 'change_me_or_risk_takeover',
    macOctet2:    '00',
    macOctet3:    '00',

    // Command Characters
    delimiter:    '^',
    funcChar:     '?',
    cmdChar:      ';',

    // Serial Ports — index 0 = Serial1 ... index 4 = Serial5
    serialPorts: [
      { baud: 9600, broadcastIn: true,  broadcastOut: true, label: '', claimedBy: null },
      { baud: 9600, broadcastIn: true,  broadcastOut: true, label: '', claimedBy: null },
      { baud: 9600, broadcastIn: true,  broadcastOut: true, label: '', claimedBy: null },
      { baud: 9600, broadcastIn: true,  broadcastOut: true, label: '', claimedBy: null },
      { baud: 9600, broadcastIn: true,  broadcastOut: true, label: '', claimedBy: null },
    ],

    // S0/USB broadcast output — global opt-in (NOT a per-serial-port setting). Round-tripped
    // through backup import/export; set on the board via ?SBOS0 / ?BCAST,OUT,S0. No UI toggle.
    broadcastToS0: false,

    // WiFi (?WIFI) — PER BOARD, unlike meshChannel which is system-wide. Each board
    // independently hosts an AP, joins one, or stays off; the CHANNEL is not part of
    // this because the radio only has one and it always follows meshChannel.
    // The password is carried so a restore can bring an AP back working — a restore
    // that replayed the SSID without the passphrase would fail closed at boot and the
    // board would come up with no AP and nothing saying why.
    wifi: {
      mode:     'off',   // 'off' | 'ap' | 'join'
      apSsid:   '',      // '' = firmware derives WCB-<alias> / WCB-<number>
      apPass:   '',      // >= 8 chars or the firmware refuses to start the AP
      joinSsid: '',
      joinPass: '',
    },

    // Kyber
    kyber: {
      mode:          'none',  // 'none' | 'local' | 'remote'
      port:          null,    // 1-5 — Maestro port, only relevant for 'local'
      baud:          115200,  // baud rate of the Kyber Maestro serial port
      marcduinoPort: null,    // 1-5 — Marcuino port (9600, broadcasts), or null
    },

    // MP3 Trigger
    mp3: {
      enabled:   false,
      port:      null,   // 1-5 — serial port the MP3 Trigger is wired to
      baud:      9600,
      volume:    0,      // 0 = loudest, 64 = inaudible
      onError:   '',     // stored sequence key to run on error (optional)
      remoteWCB: 0,      // 0 = none; else this board routes ;A to the MP3 on WCB<n>
    },

    // HCR (Human-Cyborg Relations) Vocalizer
    hcr: {
      enabled:   false,
      port:      null,   // 1-5 — serial port the HCR is wired to
      baud:      9600,
      poll:      10,     // status auto-poll interval (s); 0 = off
      remoteWCB: 0,      // 0 = none; else this board routes ;H to the HCR on WCB<n>
    },

    // DFPlayer Mini (alternate audio device) — baud fixed at 9600 by the module;
    // volume 0 = silent .. 30 = loudest (the INVERSE of the MP3 Trigger's scale).
    dfp: {
      enabled:   false,
      port:      null,   // 1-5 — serial port the DFPlayer is wired to
      baud:      9600,   // fixed by the module — not user-adjustable
      volume:    15,     // 0 = silent .. 30 = loudest
      onError:   '',     // stored sequence key to run on a module error (optional)
      remoteWCB: 0,      // 0 = none; else this board routes ;D to the DFPlayer on WCB<n>
    },

    // WLED (serial lighting) — array of { id, port, baud }. LOCAL WLED nodes on
    // this board, each with a system-wide ID (1-9). ID-addressed, mirrors maestros;
    // reach a WLED on another board with ;L<id> (firmware routes it).
    wleds: [],

    // Remote WLEDs this board auto-learned from other boards (display-only, read-only
    // in the UI, never pushed). { id, host, baud }. Populated from the ?WLED,<id>:
    // W<host>S0 lines the firmware puts in the backup.
    wledRemotes: [],

    // Maestros — array of { id, port, baud }
    maestros: [],

    // Mappings — array of { type, sourcePort, rawMode, destinations: [{ wcbNumber, port }] }
    mappings: [],

    // ETM
    etm: {
      enabled:          true,
      timeoutMs:        500,
      heartbeatSec:     10,
      missedHeartbeats: 5,   // matches the firmware initialiser (WCB.ino) and NVS default
      bootHeartbeatSec: 2,
      messageCount:     20,
      messageDelayMs:   100,
      checksumEnabled:  true,
    },

    // Stored Sequences — array of { key, value }
    sequences: [],

    // Variables — array of { name, value } (persistent named int32s on the board)
    variables: [],

    // PWM Output Ports — array of port numbers that are PWM outputs
    pwmOutputPorts: [],

    // WDP (mesh discovery). The firmware only EMITS these when they are OFF
    // (Code/WCB/WCB.ino:3023-3024), so a config carrying neither line means both are ON.
    // Nothing parsed them before, so an export/restore silently re-enabled discovery on a
    // board where the user had deliberately turned it off.
    wdpEnabled:  true,
    wdpAutoJoin: true,

    // Firmware version (populated from GitHub Releases, not from board)
    fwVersion: null,

    // Source tracking — where did this config come from?
    // 'default' | 'board' | 'file'
    source: 'default',
  };
}

// ─────────────────────────────────────────────
// Default SystemConfig — wraps general + per-board configs
// ─────────────────────────────────────────────
function createDefaultSystemConfig() {
  return {
    // Droid name — stored in file header only, not on board
    droidName: '',

    // General settings — must match across all boards
    general: {
      wcbQuantity:    1,
      meshChannel:    1,
      espnowPassword: 'change_me_or_risk_takeover',
      macOctet2:      '00',
      macOctet3:      '00',
      delimiter:      '^',
      funcChar:       '?',
      cmdChar:        ';',
      // NaviCore (special peer) — network-wide: same on every WCB. Field names
      // mirror the per-board config so extractGeneralFields() works uniformly.
      specialPeer:    false,
      specialPeerId:  20,
      // Animation controller for the whole system: 'none' | 'navicore' | 'kyber'.
      // UI state (tools page) — derived from board configs; not pushed directly.
      controller:     'none',
      etm: {
        enabled:          true,
        timeoutMs:        500,
        heartbeatSec:     10,
        missedHeartbeats: 5,   // matches the firmware initialiser (WCB.ino) and NVS default
        bootHeartbeatSec: 2,
        messageCount:     20,
        messageDelayMs:   100,
        checksumEnabled:  true,
      },
    },

    // Per-board configs — array indexed by board position (not WCB number)
    boards: [],

    // Source tracking
    source: 'default',
    lastModified: null,
  };
}

// ─────────────────────────────────────────────
// Hardware Version Helpers
// ─────────────────────────────────────────────
const HW_VERSION_MAP = {
  '1':  { display: '1.0',  binary: 'ESP32',   value: 1  },
  '21': { display: '2.1',  binary: 'ESP32',   value: 21 },
  '23': { display: '2.3',  binary: 'ESP32',   value: 23 },
  '24': { display: '2.4',  binary: 'ESP32',   value: 24 },
  '31': { display: '3.1',  binary: 'ESP32S3', value: 31 },
  '32': { display: '3.2',  binary: 'ESP32S3', value: 32 },
};

function hwValueToDisplay(value) {
  return HW_VERSION_MAP[String(value)]?.display ?? 'Unknown';
}

function hwValueToBinary(value) {
  return HW_VERSION_MAP[String(value)]?.binary ?? 'ESP32';
}

// ─────────────────────────────────────────────
// Core Backup String Parser
// 
// Accepts either:
//   - The full raw ?backup serial output (multi-line)
//   - Just the chained command string line
//
// Returns a BoardConfig object.
// ─────────────────────────────────────────────
function parseBackupString(rawOutput) {
  const config = createDefaultBoardConfig();
  config.source = 'board';

  // ── Token extraction strategy ─────────────────────────────────────────────
  // Board backups (identified by the "WCB Configuration Backup" header) print
  // each command on its own line ABOVE the chained sections.  Those per-line
  // commands are trivial to parse regardless of configured funcChar/delimiter.
  //
  // The factory-reset chained line is intentionally designed to dynamically
  // switch its own delimiter/funcChar mid-stream (so pasting it into a
  // terminal works), which makes static splitting unreliable.
  //
  // File imports use the stable ?/^ format produced by buildSystemFile and are
  // still parsed via the chained-line path.
  let tokens;
  if (rawOutput.includes('WCB Configuration Backup')) {
    tokens = extractIndividualCommandLines(rawOutput);
  } else {
    tokens = extractChainedTokens(rawOutput);
  }

  if (!tokens.length) {
    console.warn('[WCB Parser] No command tokens found in backup output');
    return config;
  }

  // Pre-pass: extract WCB number before the main parse loop so that MAESTRO
  // token routing (wcb === config.wcbNumber) works correctly even when ?MAESTRO
  // appears before ?WCB in the firmware backup output.
  for (const token of tokens) {
    const trimmed = token.trim();
    if (!trimmed || !trimmed.startsWith('?')) continue;
    const body  = trimmed.substring(1);
    const upper = body.toUpperCase();
    const uParts = upper.split(',');
    if (uParts[0] === 'WCB' && uParts[1] && !uParts[1].startsWith('Q')) {
      config.wcbNumber = parseInt(body.split(',')[1]) || 1;
      break;
    }
  }

  for (const token of tokens) {
    const trimmed = token.trim();
    if (!trimmed || !trimmed.startsWith('?')) continue;

    // Strip leading ? to get the command body
    const body = trimmed.substring(1);
    parseToken(body, config);
  }

  // After parsing, infer the Kyber Marcuino port from the serial port label so
  // the UI can restore it after a boardPull.  The label 'Kyber Marcuino' is
  // written to the board during the push; it comes back in the backup as
  // ?LABEL,S<n>,Kyber Marcuino which the LABEL parser case stores on the port.
  if (config.kyber.mode === 'local') {
    const marcIdx = config.serialPorts.findIndex(
      p => p.label?.toLowerCase() === 'kyber marcuino'
    );
    config.kyber.marcduinoPort = marcIdx >= 0 ? marcIdx + 1 : null;
  }

  // After parsing, evaluate port claims
  evaluatePortClaims(config);

  return config;
}

// ─────────────────────────────────────────────
// Legacy runtime variable segments — shared regex builder.
// Older firmware emitted variables as runtime "<cmdChar>V,name,value" commands
// (e.g. ";V,foo,1") instead of the funcChar-prefixed ?VAR,SET CONFIG form.
// The 'V' verb matches case-INsensitively (";v,foo,1" is the same command —
// hence the 'i' flag), but variable NAMES remain case-SENSITIVE: the captured
// name is re-emitted verbatim, and [A-Za-z0-9_] lists both cases explicitly,
// so the 'i' flag cannot fold distinct names together.
// `prefix` anchors the segment for the caller's context:
//   '^'    — a whole trimmed line (extractIndividualCommandLines)
//   '\\^'  — a segment glued to the end of a chained token (extractChainedTokens)
// Value accepts an integer or TRUE/FALSE (both accepted by the firmware and
// by parseToken's VAR,SET case).
// ─────────────────────────────────────────────
function buildLegacyVarRe(cmdChar, prefix) {
  const cmdEsc = cmdChar.replace(/[.*+?^${}()|[\]\\]/g, '\\$&');
  return new RegExp(`${prefix}${cmdEsc}V,([A-Za-z0-9_]{1,15}),(-?\\d+|TRUE|FALSE)$`, 'i');
}

// ─────────────────────────────────────────────
// Board-backup path: parse the per-line commands the firmware prints above the
// chained sections.  Each line is a single command with any funcChar prefix,
// so there is no delimiter-switching ambiguity.
// Returns tokens normalised to '?COMMAND,...' strings.
// ─────────────────────────────────────────────
function extractIndividualCommandLines(rawOutput) {
  const lines    = rawOutput.split(/\r?\n/);
  const tokens   = [];

  // Detect the board's configured funcChar.
  // The firmware prints e.g. ".FUNCCHAR,." when funcChar is non-default.
  // Match: any single character, then "FUNCCHAR,", then the new char.
  let funcChar = '?';
  for (const line of lines) {
    const m = line.trim().match(/^.FUNCCHAR,(.)/i);
    if (m?.[1]) { funcChar = m[1]; break; }
  }

  // Detect the board's configured cmdChar the same way (e.g. ".CMDCHAR,/").
  // Older firmware emitted variables as runtime ";V,name,value" lines using the
  // cmdChar prefix instead of the funcChar-prefixed ?VAR,SET CONFIG form.
  let cmdChar = ';';
  for (const line of lines) {
    const m = line.trim().match(/^.CMDCHAR,(.)/i);
    if (m?.[1]) { cmdChar = m[1]; break; }
  }

  // Legacy runtime variable line, anchored to the whole line (";V,name,1",
  // ";v,name,1" — see buildLegacyVarRe).
  const legacyVarLineRe = buildLegacyVarRe(cmdChar, '^');

  // Collect individual command lines that appear before the chained sections.
  // The firmware prints one "Serial.println(lfi + cmd)" per command, then the
  // "=== For Configured Boards ===" header marks the start of the chained block.
  for (const line of lines) {
    const trimmed = line.trim();
    if (!trimmed) continue;

    // Stop when the chained section begins
    if (trimmed.includes('=== For Configured') || trimmed.includes('=== For Factory')) break;

    // Skip header/comment/separator lines
    if (trimmed.startsWith('***')) continue;
    if (trimmed.startsWith('---')) continue;
    if (/^[-=*]+$/.test(trimmed)) continue;

    // Accept lines that start with '?' or the detected funcChar.
    // Also accept legacy runtime variable lines ";V,name,value" (cmdChar
    // prefix, 'V' verb case-insensitive — shared regex with the chained-token
    // peel loop) — normalise them to the VAR,SET CONFIG form for parseToken.
    let body = null;
    if (trimmed.startsWith('?'))               body = trimmed.slice(1);
    else if (trimmed.startsWith(funcChar))     body = trimmed.slice(1);
    else {
      const lm = trimmed.match(legacyVarLineRe);
      if (lm) body = `VAR,SET,${lm[1]},${lm[2]}`;
    }

    // Skip lines that start with a known word (non-command output like "WARNING:",
    // "Booting", "ETM:", etc.) — they won't have a single-char funcChar prefix
    if (body !== null && body.length > 0) {
      tokens.push('?' + body); // normalise prefix to '?' for parseToken
    }
  }

  return tokens;
}

// ─────────────────────────────────────────────
// File-import path: split the stable ?/^ chained string produced by
// buildSystemFile (always written with outputFuncChar:'?' / outputDelim:'^').
// ─────────────────────────────────────────────
function extractChainedTokens(rawOutput) {
  let commandString = extractFactoryResetLine(rawOutput);
  if (!commandString) commandString = rawOutput.trim();
  if (!commandString) return [];

  // Detect the configured cmdChar (appears as a ?CMDCHAR,<c> token in the
  // chain) so legacy runtime variable segments can be recognised below.
  const cmdChar = commandString.match(/\?CMDCHAR,(.)/i)?.[1] ?? ';';

  // Older firmware emitted variables as runtime "^;V,name,value" segments which
  // glue onto the END of the previous token when splitting on "^?".  Strip them
  // off (otherwise they'd fold into a preceding ?SEQ value and corrupt it) and
  // re-emit them as normalised ?VAR,SET tokens.  Shared case-insensitive regex
  // with the per-line path — "^;v,name,1" peels identically to "^;V,name,1".
  const legacyVarRe = buildLegacyVarRe(cmdChar, '\\^');

  // Split on "^?" boundaries.  ?SEQ,SAVE values embed "^" internally to chain
  // device commands, so we split on the two-char boundary "^?" to avoid tearing
  // saved-sequence values apart.
  const rawParts = commandString.split('^?');
  const tokens     = [];
  const legacyVars = [];
  for (let i = 0; i < rawParts.length; i++) {
    let part = rawParts[i].trim();
    if (!part) continue;

    // Peel trailing legacy variable segments (may be stacked: "...^;V,a,1^;V,b,2")
    const partVars = [];
    let m;
    while ((m = part.match(legacyVarRe))) {
      partVars.unshift(`?VAR,SET,${m[1]},${m[2]}`);  // unshift keeps original order
      part = part.slice(0, part.length - m[0].length).trim();
    }
    legacyVars.push(...partVars);

    if (!part) continue;
    tokens.push(i === 0 ? part : '?' + part); // restore '?' consumed by split
  }
  return tokens.concat(legacyVars);
}

// ─────────────────────────────────────────────
// Extract the factory reset command line from raw ?backup output
// ─────────────────────────────────────────────
function extractFactoryResetLine(rawOutput) {
  const lines = rawOutput.split(/\r?\n/);

  let foundHeader = false;
  for (const line of lines) {
    const trimmed = line.trim();

    // Look for the factory reset section header
    if (trimmed.includes('For Factory Reset') || trimmed.includes('Fresh Boards')) {
      foundHeader = true;
      continue;
    }

    // The next non-empty, non-comment line after the header is our command string
    if (foundHeader && trimmed.length > 0 && !trimmed.startsWith('***')) {
      return trimmed;
    }
  }

  // Fallback: look for any line that starts with ?HW, which is always first in backup
  for (const line of lines) {
    const trimmed = line.trim();
    if (trimmed.startsWith('?HW,') || trimmed.startsWith('?hw,')) {
      return trimmed;
    }
  }

  return null;
}
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
